AnasSarkiz/magnetic-shutter-remote/evidence/R7-components/jauch-850-pack.png

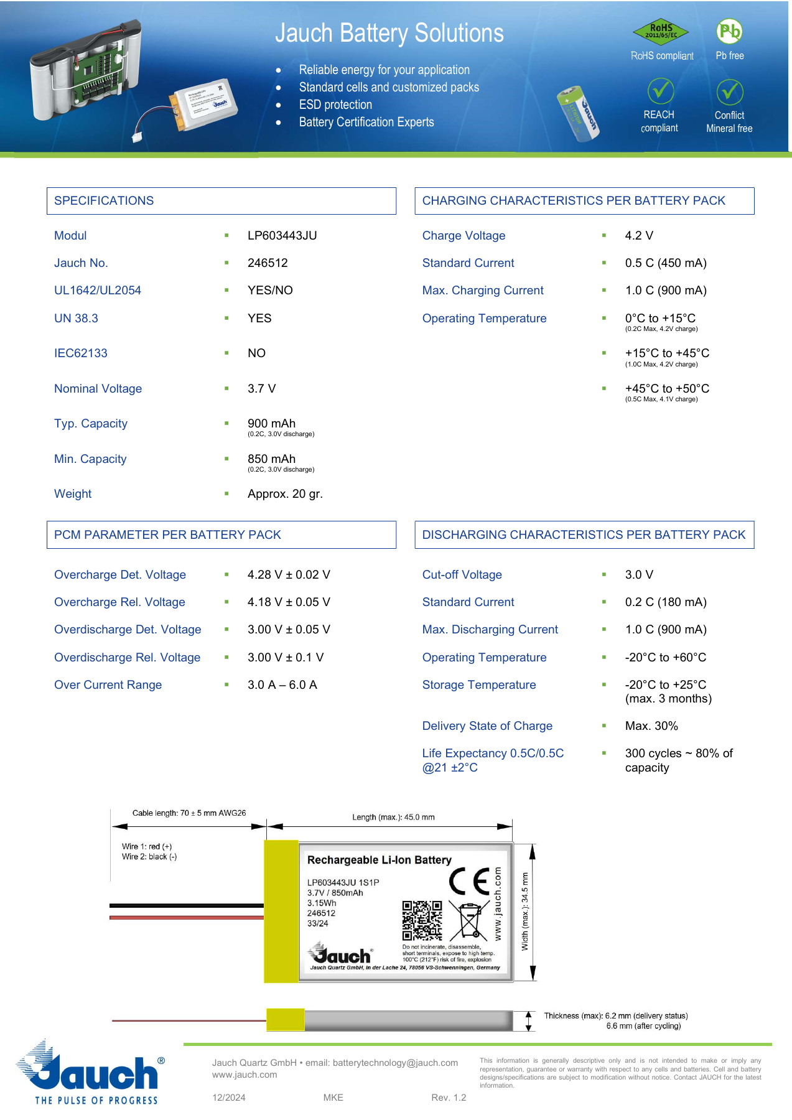
evidence/R7-components/jauch-850-pack.png
