AnasSarkiz/magnetic-shutter-remote/evidence/USB4215-import-audit/external-process-review/package/README.md

# GCT USB4215 / JLCPCB external qualification package

**ENGINEERING QUALIFICATION ONLY - NOT FOR FABRICATION**

Version **external-review-1**, 2026-10-03. Exact part **GCT USB4215-03-A / C37616412**. Candidate **BLOCKED**; remote board **R5 DFM REVIEW — NOT FOR FABRICATION**. No R6, PCB edit or manufacturing approval.

This is a component-only engineering review, not order-ready PCB data. It contains exact GCT drawing/specification, source identity, dimensioned copper/drill comparison, independent source/import/CAM paste views, four shell details, aperture table, import-fix summary, paste/process findings and separate unsent questions. No full R5 project, credentials, raw board CAM, BOM/CPL or unrelated repository content is included.

1. [Exact source register](SOURCE-REGISTER.md)
2. [Dimensioned copper/drill comparison](copper-drill-dimensioned-comparison.png)
3. [Aperture geometry](APERTURE-GEOMETRY.md)
4. [Paste qualification](PASTE-QUALIFICATION.md)
5. [Thermal/process context and shell table](SOLDER-PROCESS.md)
6. [Local tooling fix summary](IMPORTER-FIX-SUMMARY.md)
7. [GCT unresolved questions](GCT-REQUEST.md)
8. [JLCPCB exact process-coverage questions](JLCPCB-REQUEST.md)

The copper/drill comparison image/SVG is preserved **pre-fix evidence**. Its old caption "import drops 16 explicit TOP-paste regions" describes the original pipeline. The later importer fix closes that fidelity defect, as shown in the current source/import/CAM images and summary; the original dimensional evidence was not edited.

**SUPPLIER CAD INTENDS PASTE ON FOUR SHELL FEATURES**; that is not GCT process approval or JLCPCB assembly coverage. Published temperatures remain test conditions with production limits unconfirmed. Neither request has been sent; there are no external responses. No-response is not approval.

`MANIFEST.sha256` covers every other member. Verify with a SHA256-aware tool after extraction. Once sent, preserve this ZIP/hash exactly; clarification packages require a new version/name. Physical validation remains **POST-PROTOTYPE PHYSICAL VALIDATION**.
