AnasSarkiz/magnetic-shutter-remote/cloud/ENVIRONMENT-START.md

Use the existing isolated checkout /workspace/magnetic-shutter-remote; do not create a worktree. Preserve a later task-derived working branch, all changes, and local commits. Do not fetch/switch/reset an active task.
Before running anything, read AGENTS.md, cloud/SETUP.md, cloud/HANDOFF.md and cloud/STATUS.md. Require these files, cloud/R7-PORTABLE-MANIFEST.json and the R8 context; verify git merge-base --is-ancestor b25353c0a1d7adceeab9a966aaf68a6cb3594cc9 HEAD. If context is missing or HEAD is old main, stop and report; never run the old board.
No server is needed. From the checkout, use bash with set -euo pipefail. Export npm_config_cache="$PWD/.codex/runtime/npm-cache". Record git HEAD/status and actual host/cgroup memory/CPU/OOM limits under ignored .codex/logs with unique timestamps. Run bash cloud/setup.sh and bash cloud/smoke.sh, retaining separate logs with tee and pipefail. Report exit statuses, test counts, warnings and final tracked/untracked status; do not discard changes. The onboarding instance observed 32 GiB memory.max and a four-CPU quota, not a guaranteed plan allocation. Node25.6.0/Bun1.3.9 are task-local; Python>=3.11 required. Python3.14 is only for later optional CAM.
Setup/start smoke stays lightweight: do not route, run a root board build, broad DFM, viewer, 3D/CAM/SDK build as part of environment initialization. The source-edit/commit/push/PR/board-publication prohibitions apply to this onboarding run only, not permanently to later engineering tasks. Later user-authorized tasks may implement the ESP32 board and publish qualified prototype steps under AGENTS.md after the required gates pass. Frozen baselines remain immutable. Ordering, payment, assembler upload and supplier contact require separate authorization. Keep the ESP32 power-metadata warning and unresolved issues075/076 explicit; smoke is not qualification or fabrication validation.
Only later, after component qualification and placement gates pass and the task authorizes heavy work, invoke every heavy job through python3 cloud/run-heavy.py -- <command>, sequentially. This wrapper records resources/OOM and preserves failures; it does not waive gates.
Use provider-managed authentication; no user tokens/secrets. Keep environment private/only me and network restricted. Do not broaden repository access or share the environment. This onboarding task does not publish the environment or board; the user controls environment Publish.
