AnasSarkiz/magnetic-shutter-remote/cloud/TASK-PROMPT.md

Continue magnetic shutter remote R8 on this Cloud branch. Read AGENTS.md, cloud/HANDOFF.md, VALIDATION.md, issue075/076 and the repository-local tscircuit skill before changing anything. Run cloud/setup.sh and cloud/smoke.sh; report actual memory/runtime limits. Preserve baselines/ and main. Do not route on the Mac or run multiple heavy jobs. The ESP32-C3-WROOM-02-N4/C2934560 migration is unfinished: resolve the documented import/qualification gates through supported tooling, then complete power/boot/UART circuitry, mechanical fit, unrouted checks, routing and same-revision exports. One battery, one USB-C, no torch. Keep all fitted parts verified JLCPCB imports; no custom substitute footprints/generated-import or JSON patches. Use cloud/run-heavy.py for Linux heavy builds after placement passes. Do not call the existing Nordic JSON an ESP32 build, waive warnings, change manufacturer thresholds, order, pay or contact suppliers. Preserve exact prior results and known failures. Update issue reports and validation with real evidence, then publish only qualified prototype steps with matching build circuit.json. Physical tests remain POST-PROTOTYPE PHYSICAL VALIDATION.
