AnasSarkiz/magnetic-shutter-remote/evidence/USB4215-import-audit/UNSENT-QUALIFICATION-QUESTIONS.md

# USB4215 qualification questions — prepared only, NOT SENT

These are not substituted for authoritative answers. No files were sent or uploaded.

## GCT manufacturer

For USB4215-03-A, drawing/specification A, 26 April 2024, please identify the intended soldering method for each of the four through-hole shell stakes (PIP reflow, wave/selective, manual secondary, or another method). For a 1.0 mm PCB, please provide approved copper/mask/paste treatment, stencil thickness and shell paste volume/overprint guidance. The C37616412 supplier model uses twelve separate rectangular contact apertures and four segmented capsule shell apertures (~1.0 ×1.8 mm rear; ~1.0 ×2.2 mm front). Are these approved? Please provide allowable reflow-cycle count and confirm the section 7.0 time/temperature limits. If post-reflow manual shell soldering is allowed, specify maximum iron temperature, contact time, repeated operations and housing restrictions. Please identify the applicable document/revision.

Supporting drawings: preserved GCT drawing/spec, [source metrology](../USB-replacement-search-2026-10-03/continued-search/USB4215-source-metrology.png), [actual TOP paste CAM](final/cam-paste.png), [aperture dimensions](final/aperture-metrology.json). Supplier model/package UUID: 3104977db58742e399663286e4a66eac, title USB-C-SMD_GT-USB-7010B. The unrelated model title is disclosed, not treated as GCT authorization.

## JLCPCB assembler

For exact part C37616412 / GCT USB4215-03-A, does your PCBA process solder all four plated shell slots, and by what method? Is it included in Economic/Standard SMT assembly, or must a THT/PIP/selective/manual or special service be requested? What stencil thickness, shell paste/overprint, mask openings, inspection and order options do you require for a 1.0 mm PCB? Please confirm coverage of the four shell anchors explicitly; “SMT Assembly” alone does not answer this. Can you use the GCT land drawing with the separately preserved supplier paste geometry, and what changes or manufacturer approval are required? Confirm any X-ray or special inspection requirement for this exact connector.

Manufacturer process limits must come from GCT; assembler process coverage must come from JLCPCB. No party is asked to certify the other's responsibility.
