AnasSarkiz/magnetic-shutter-remote/evidence/USB4215-import-audit/external-process-review/GCT-REQUEST.md

# GCT technical request — finalized, NOT SENT

**ENGINEERING QUALIFICATION ONLY — NOT FOR FABRICATION**

Subject: USB4215-03-A stencil and shell-anchor soldering qualification

Please provide exact-part engineering guidance for GCT **USB4215-03-A**, drawing/specification Rev A, 2024-04-26. We are evaluating the C37616412 supplier package, UUID `3104977db58742e399663286e4a66eac`, for a 1.0 mm PCB. Its copper and plated-slot geometry have been compared with your drawing. The supplied CAD contains **12 contact paste apertures and four shell paste apertures**; the attached images/table preserve those contours. This is supplier CAD, not a GCT-approved stencil claim. Its library title is USB-C-SMD_GT-USB-7010B and its metadata links another part, so we need your independent approval.

**A. Stencil / paste**

1. Are the four supplied shell paste apertures intended to solder the four shell anchors during SMT reflow?
2. Is this exact supplier paste/stencil pattern approved or recommended by GCT for USB4215-03-A?
3. If not, please provide the recommended stencil thickness, contact aperture dimensions, shell aperture dimensions, and paste reduction/expansion or overprint rules for this PCB thickness. Please identify any required solder-mask treatment.

**B. Production reflow**

Section 7.0 publishes peak 255–260 °C, 60 s above 217 °C, 50 s above 230 °C and 5 s above 250 °C. Are these approved production-process limits, or heat-resistance/qualification-test conditions only? Please specify the recommended/maximum production peak temperature, maximum peak duration, time above liquidus, allowed reflow-cycle count, and ramp/preheat constraints.

**C. Shell completion**

Are **all four shell anchors on USB4215-03-A intended to be completely soldered in the same SMT reflow operation using these four apertures**? If yes, is any secondary soldering required? If no, please identify the required manual/selective/wave or other process. For any permitted manual step after reflow, provide maximum iron temperature, maximum contact time, permitted repeat/heating-cycle limits and applicable housing restrictions.

Please identify the applicable drawing/process document and revision. Responses must apply specifically to USB4215-03-A. We are not asking GCT to certify JLCPCB's assembly coverage.

Suggested attachment: `GCT-USB4215-JLCPCB-QUALIFICATION.zip`. Nothing has been sent or uploaded.
