AnasSarkiz/magnetic-shutter-remote/evidence/USB4215-import-audit/external-process-review/JLCPCB-REQUEST.md

# JLCPCB technical request — finalized, NOT SENT

**ENGINEERING QUALIFICATION ONLY — NOT FOR FABRICATION**

Subject: C37616412 exact shell-anchor coverage and stencil confirmation

Please confirm the PCBA process for **C37616412 / GCT USB4215-03-A**, supplier package UUID `3104977db58742e399663286e4a66eac`, on a 1.0 mm PCB. Your exact-part listing records Extended SMT Assembly, Economic and Standard. Our recorded 2026-10-03 check showed 145 stock / 63 available to order; availability is separate from process qualification. Attached geometry shows 12 contact paste apertures and four paste apertures over plated shell-anchor slots.

1. Does Extended SMT assembly for this exact part solder all 12 contact paste features **and all four shell-anchor paste features**?
2. Are all four shell anchors completed during normal SMT reflow using the supplied paste apertures?
3. Is any THT, selective, wave, manual or special process required after SMT? If so, identify the exact process and its operating profile/limits so it can be checked against GCT's permitted process.
4. Is this exact supplier stencil/paste geometry accepted by your standard stencil process? State the stencil thickness, any contact/shell aperture modifications or required overprint, and any mask treatment needed.
5. If the four shell anchors are not automatically included, what service/order option must be selected?
6. Are any exact-connector PCBA order notes, engineering confirmations, special inspection or other assembly requirements needed?

Please answer for C37616412 specifically. A generic statement that Extended parts are SMT compatible does not establish shell-anchor coverage. GCT manufacturer thermal/process approval is being requested separately; we are not asking JLCPCB to substitute for that approval.

Suggested attachment: `GCT-USB4215-JLCPCB-QUALIFICATION.zip`. Nothing has been sent or uploaded.
