AnasSarkiz/magnetic-shutter-remote/evidence/USB4215-import-audit/external-process-review/package/SOURCE-REGISTER.md

# Exact source register

**ENGINEERING QUALIFICATION ONLY - NOT FOR FABRICATION**

GCT / Global Connector Technology **USB4215-03-A / C37616412**. Drawing/specification **Rev A, 2024-04-26**. Component UUID `907b9bea7a60481d8a3d3aef3cba8ef1`; package UUID `3104977db58742e399663286e4a66eac`.

Supplier library title `USB-C-SMD_GT-USB-7010B`; its metadata links another part, C2837092. Neither that title/link nor successful import is GCT authority. Copper/drills were independently compared against the included GCT drawing. The paste shapes are supplier geometry requiring separate manufacturer approval.

[Machine-readable source register](SOURCE-REGISTER.json) records exact original raw CAD, regenerated import, Circuit JSON and final paste hashes, together with manufacturer/supplier URLs. Those full CAD/CAM files are preserved locally and intentionally excluded from this compact external review.

The 2026-10-03 stock observation is **145 stock / 63 available to order / Extended / SMT Assembly / Economic and Standard / MSL1**. This is a dated observation, not a sourceability guarantee or shell-process approval. No special X-ray requirement was displayed; that is not a waiver. No response, contact or upload occurred.

Official sources: [GCT exact product](https://gct.co/connector/usb4215), [GCT drawing](https://gct.co/files/drawings/usb4215.pdf), [GCT specification](https://gct.co/files/specs/usb4215-spec.pdf), [JLCPCB exact part](https://jlcpcb.com/partdetail/39339856-USB4215_03A/C37616412).
