AnasSarkiz/magnetic-shutter-remote/tooling/r7-paste-review-requirements.txt

aiofiles==25.1.0
blinker==1.9.0
cairocffi==0.9.0
cffi==2.1.1
charset-normalizer==3.5.2
click==8.5.0
Flask==3.1.3
gerbonara==1.5.0
h11==0.16.0
h2==4.4.1
hpack==4.2.0
Hypercorn==0.18.0
hyperframe==6.1.0
itsdangerous==2.2.0
Jinja2==3.1.6
MarkupSafe==3.0.3
numpy==2.5.3
pcb-tools==0.1.6
pillow==12.3.0
priority==2.0.0
pycparser==3.0
Quart==0.23.1
reportlab==4.4.3
rtree==1.4.1
scipy==1.18.1
shapely==2.1.2
svgpathtools==1.7.2
svgwrite==1.4.3
Werkzeug==3.1.9
wsproto==1.3.2
