AnasSarkiz/magnetic-shutter-remote/baselines/r7/mechanical/drawing-r2-1.png

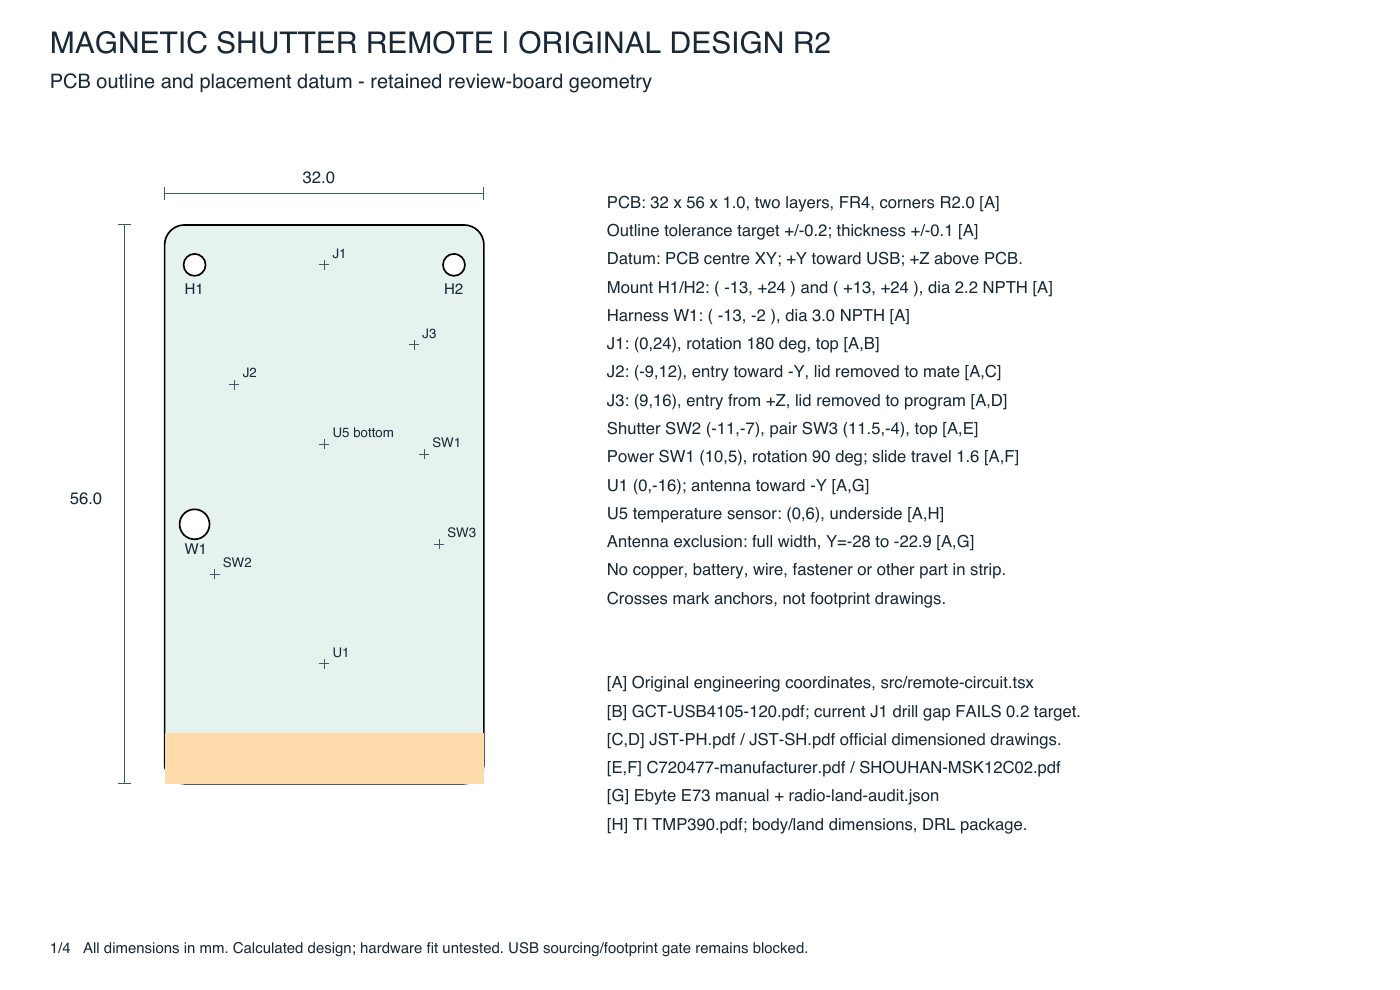
baselines/r7/mechanical/drawing-r2-1.png
