AnasSarkiz/magnetic-shutter-remote/baselines/r7/mechanical/drawing-r2-4.png

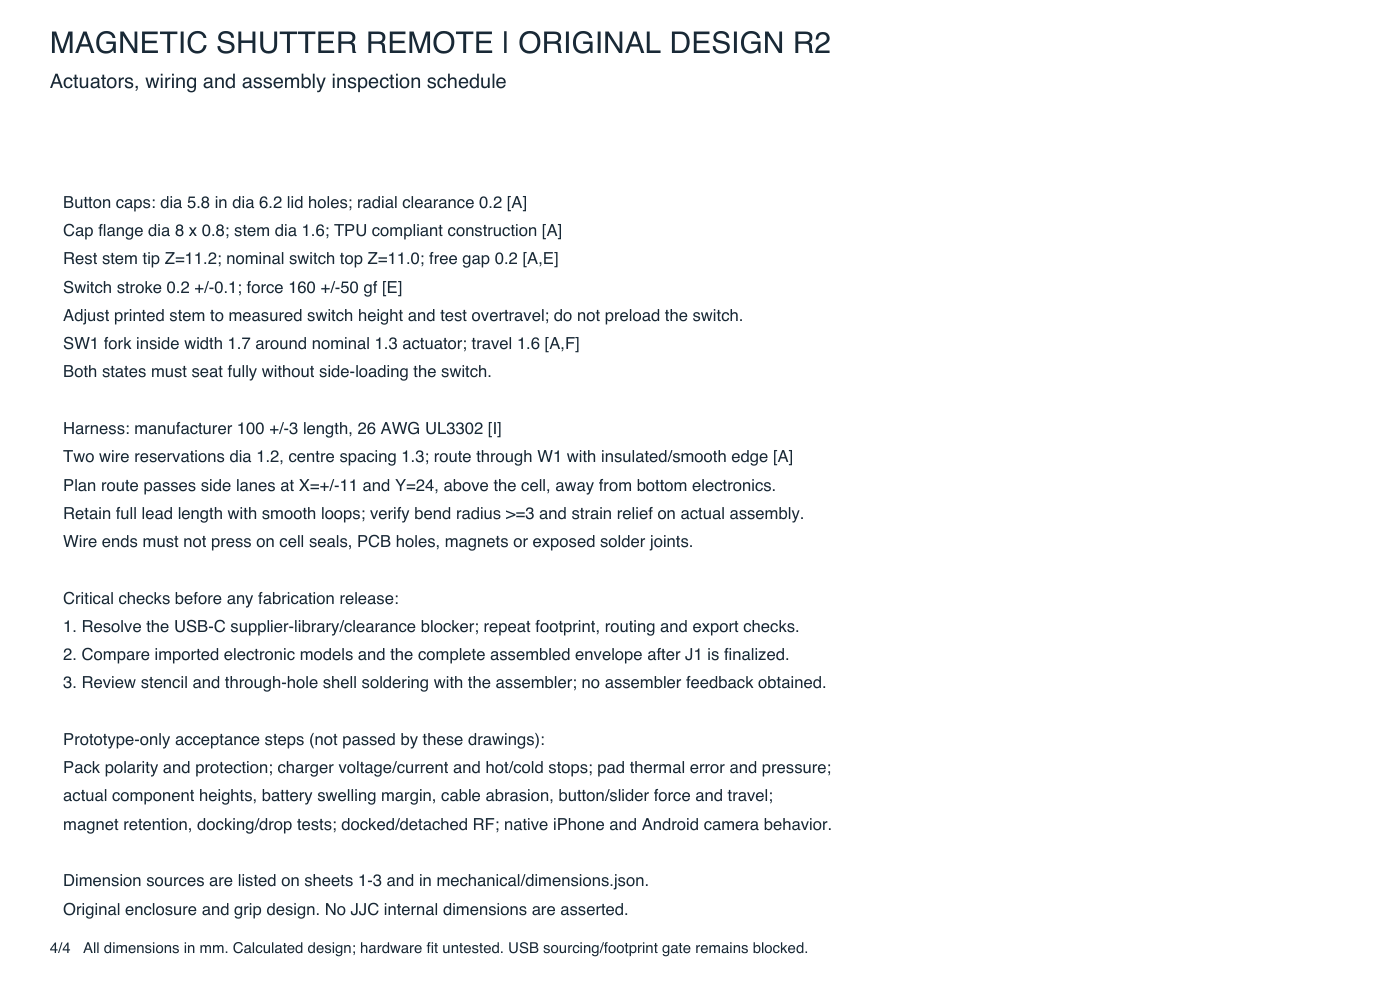
baselines/r7/mechanical/drawing-r2-4.png
