AnasSarkiz/magnetic-shutter-remote/baselines/r7/mechanical/drawing-r3-2.png

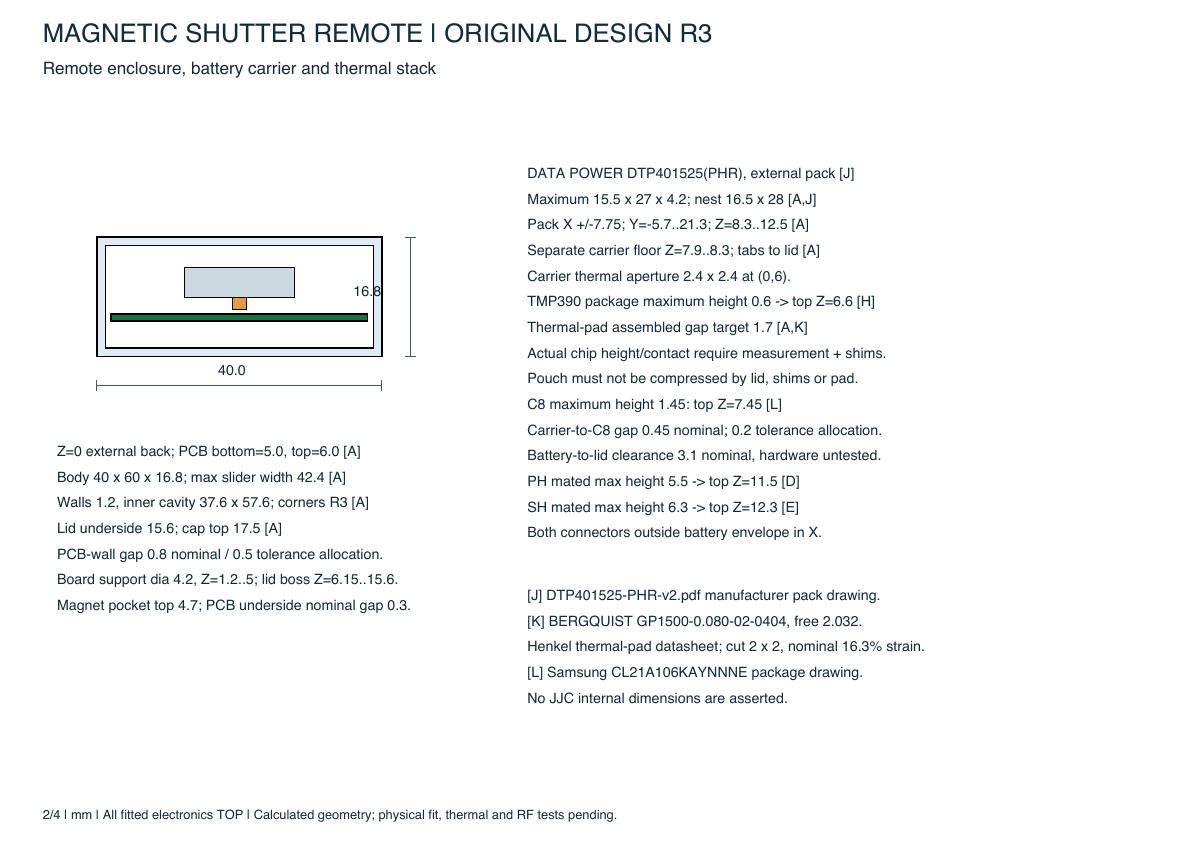
baselines/r7/mechanical/drawing-r3-2.png
