AnasSarkiz/magnetic-shutter-remote/baselines/r7/mechanical/drawing-r3-4.png

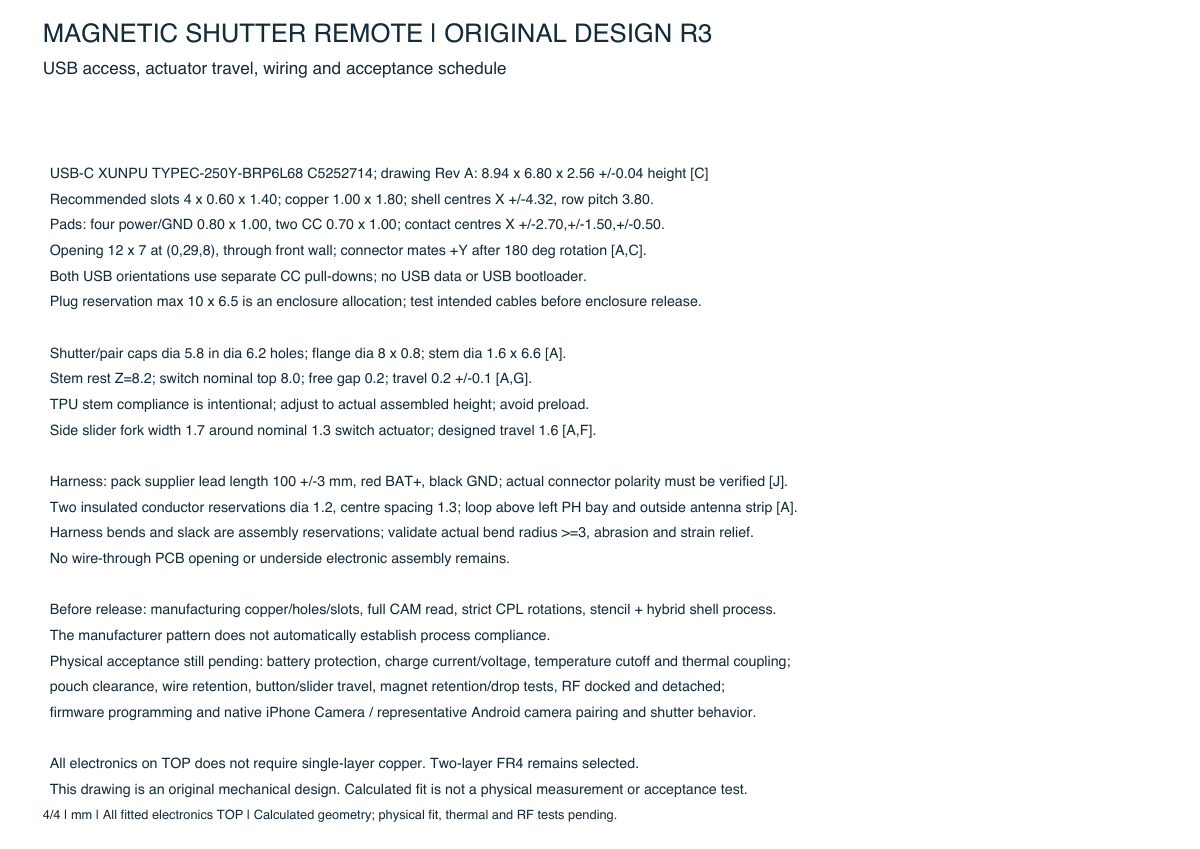
baselines/r7/mechanical/drawing-r3-4.png
