AnasSarkiz/magnetic-shutter-remote/baselines/r7/mechanical/remote-cutaway-r3.png

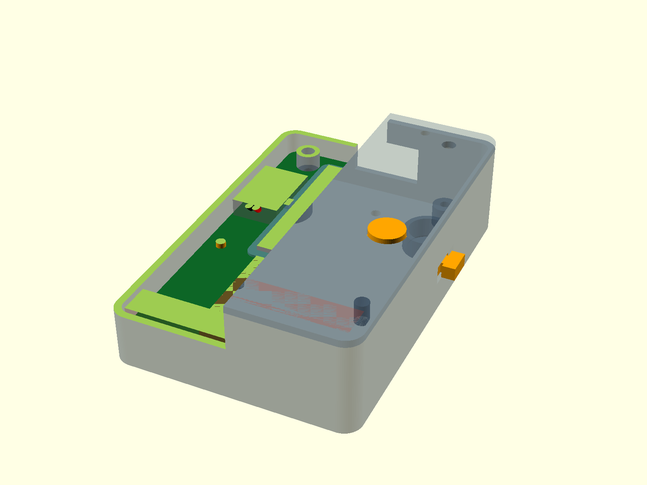
baselines/r7/mechanical/remote-cutaway-r3.png
