AnasSarkiz/magnetic-shutter-remote/evidence/R7-components/pt4115-official-pinout.png

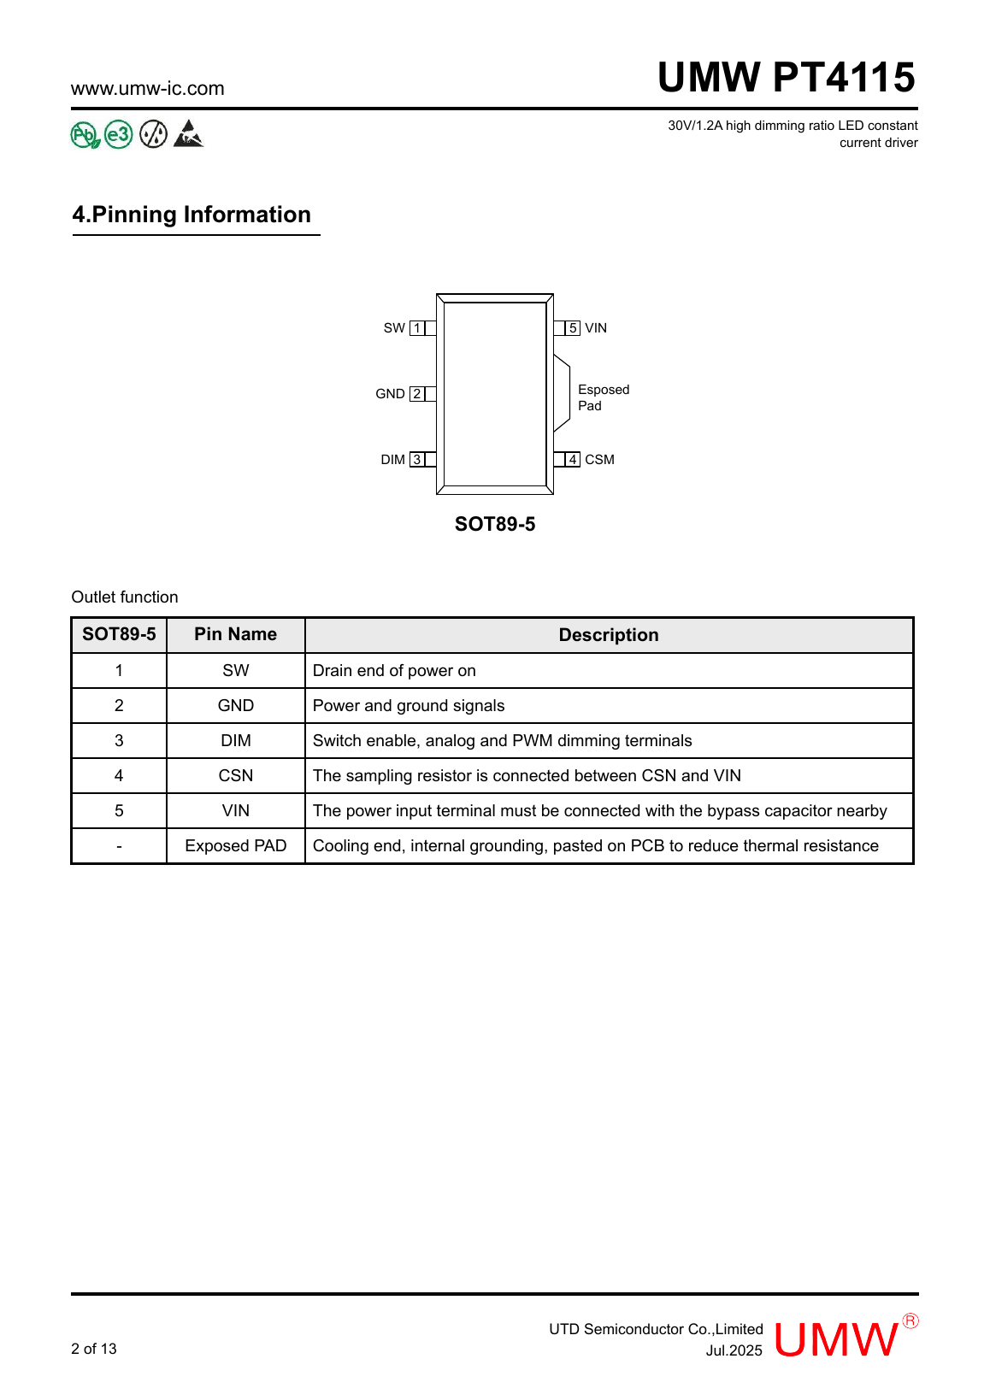
evidence/R7-components/pt4115-official-pinout.png
