AnasSarkiz/magnetic-shutter-remote/evidence/R7-components/pt4115-pinout.png

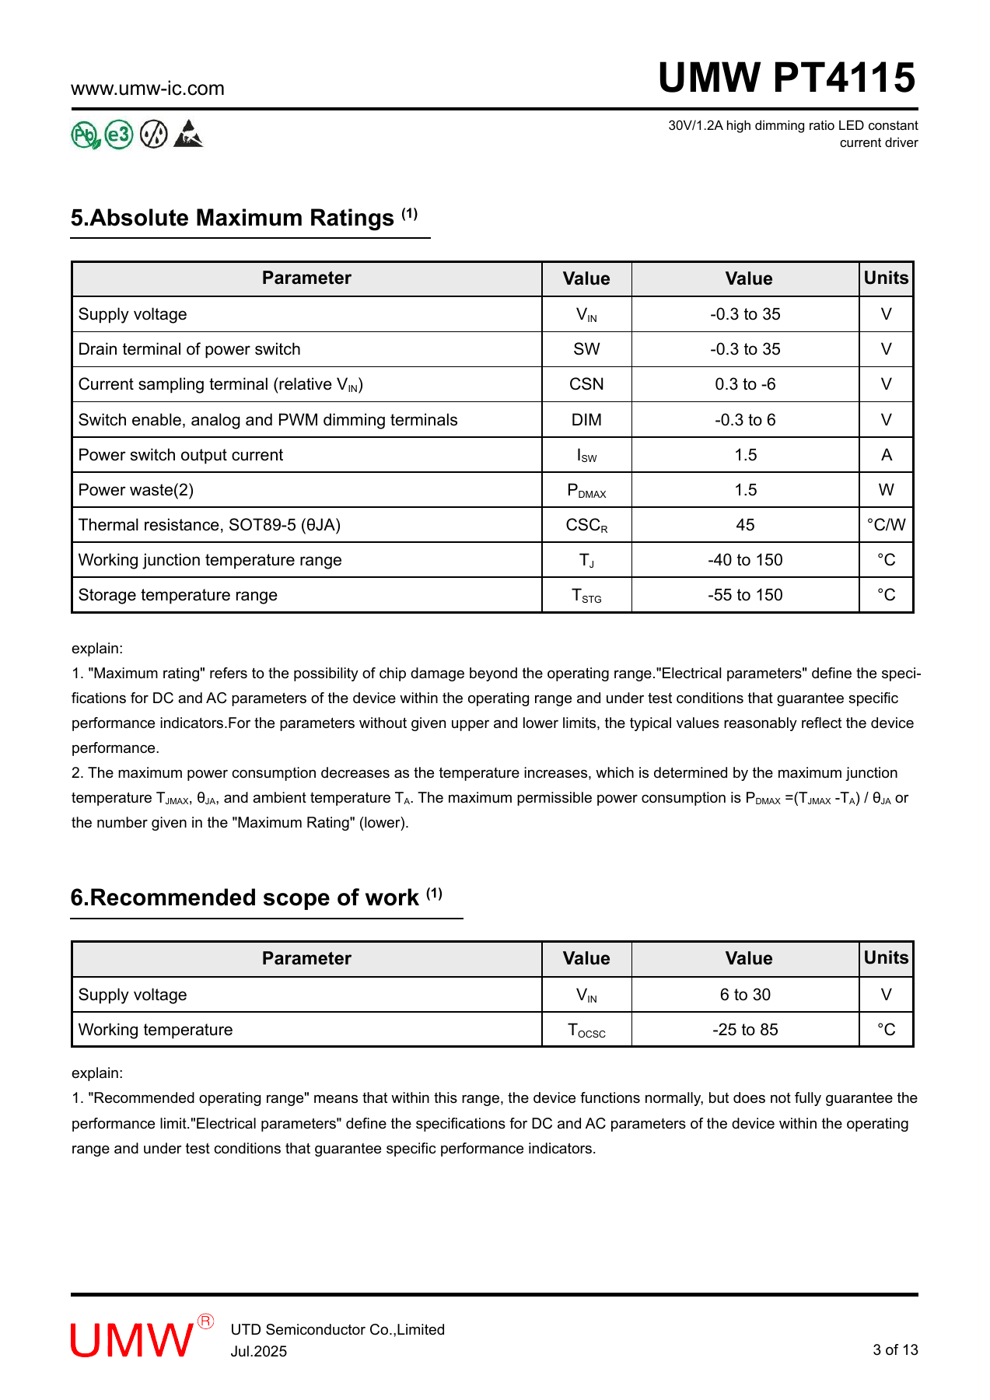
evidence/R7-components/pt4115-pinout.png
