AnasSarkiz/magnetic-shutter-remote/evidence/R7-power/DTP603443-pack-drawing.png

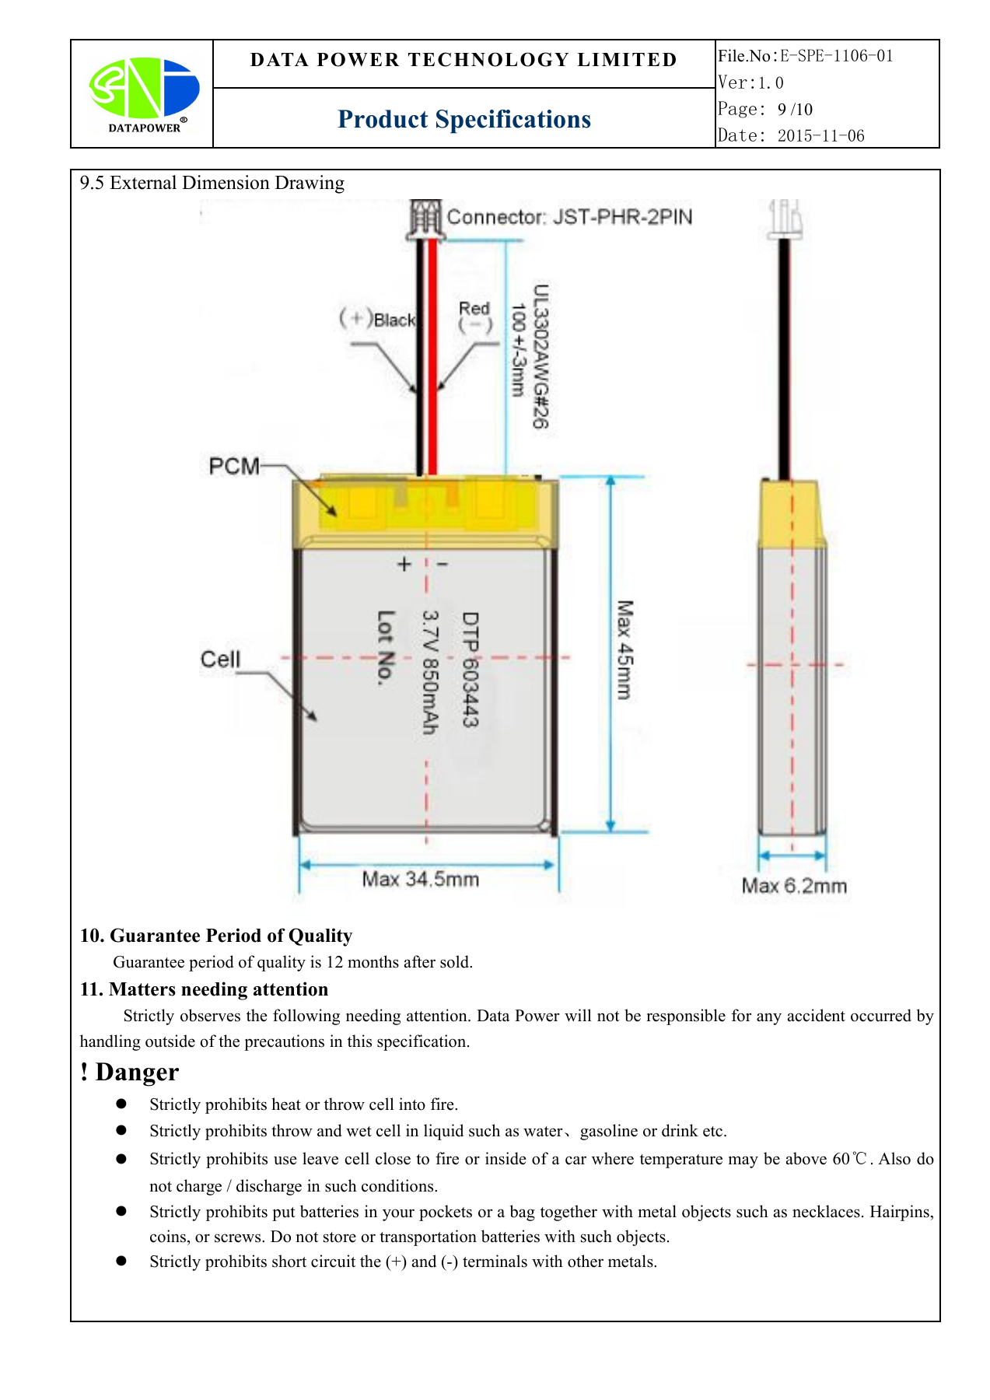
evidence/R7-power/DTP603443-pack-drawing.png
