AnasSarkiz/magnetic-shutter-remote/evidence/R7-power/PKCELL-pack-drawing.png

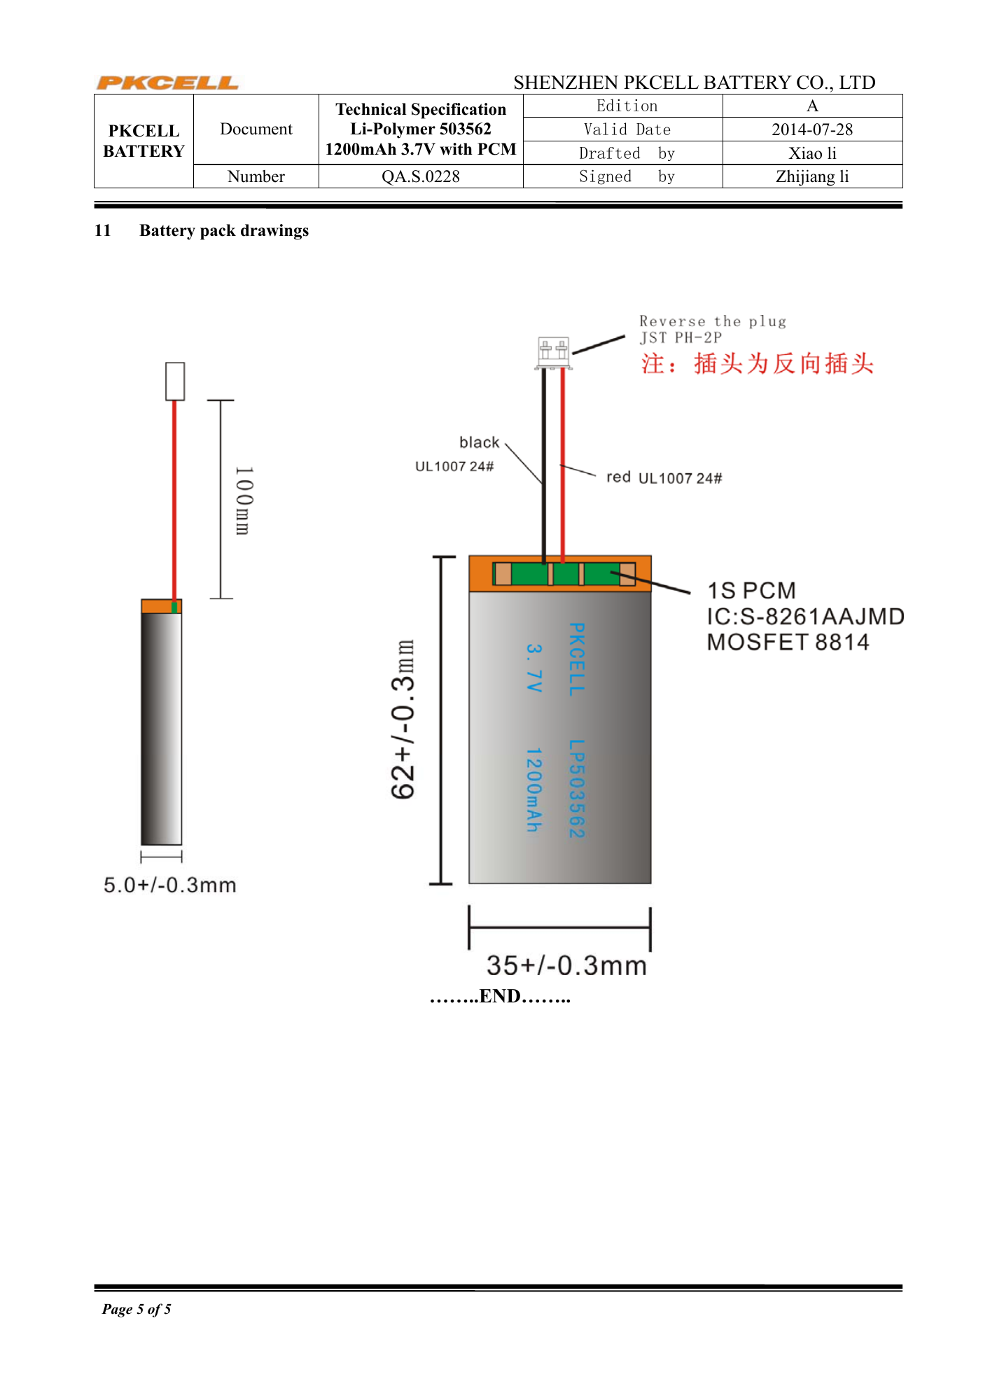
evidence/R7-power/PKCELL-pack-drawing.png
