AnasSarkiz/magnetic-shutter-remote/evidence/R7-power/TI-current-limit-equation.png

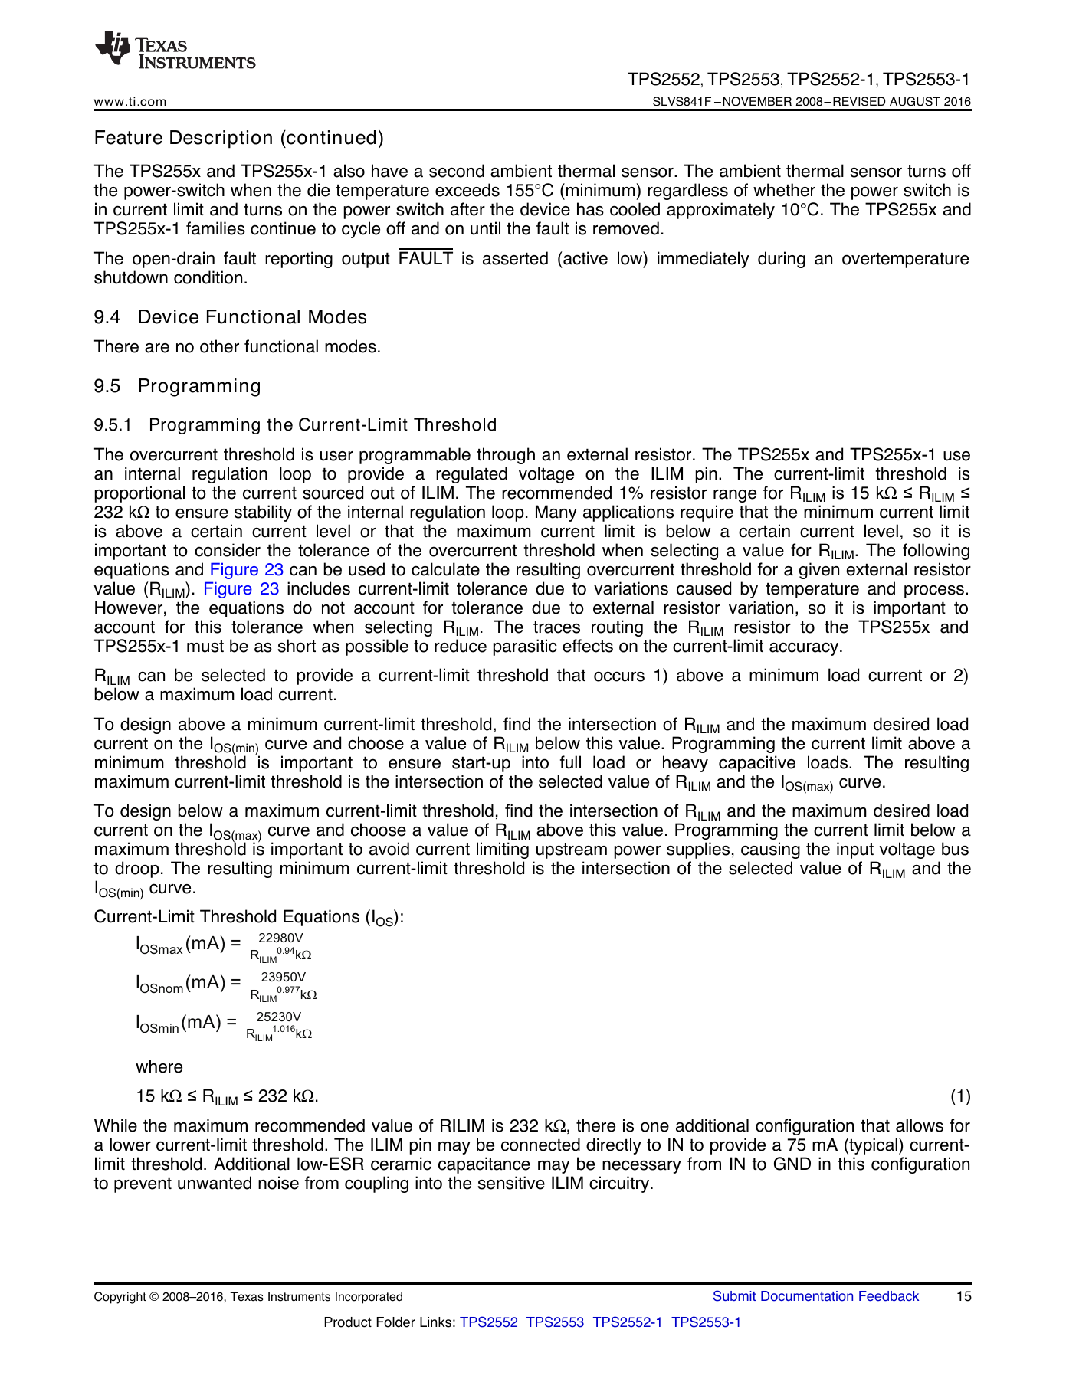
evidence/R7-power/TI-current-limit-equation.png
