AnasSarkiz/magnetic-shutter-remote/references/R5/C456012.png

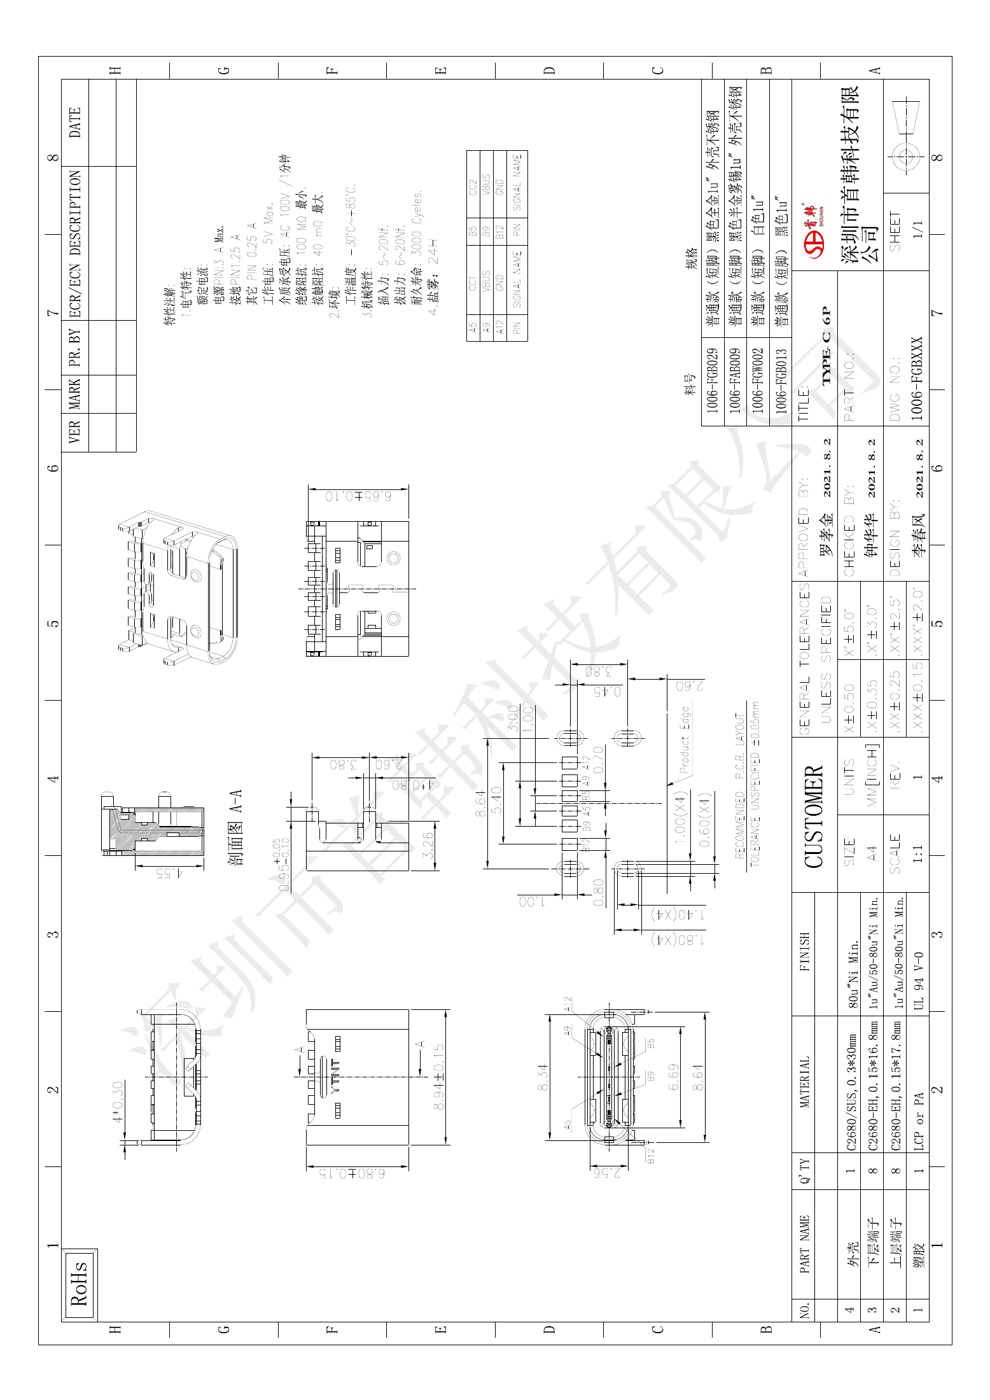
references/R5/C456012.png
