AnasSarkiz/magnetic-shutter-remote/references/R5/C668623.png

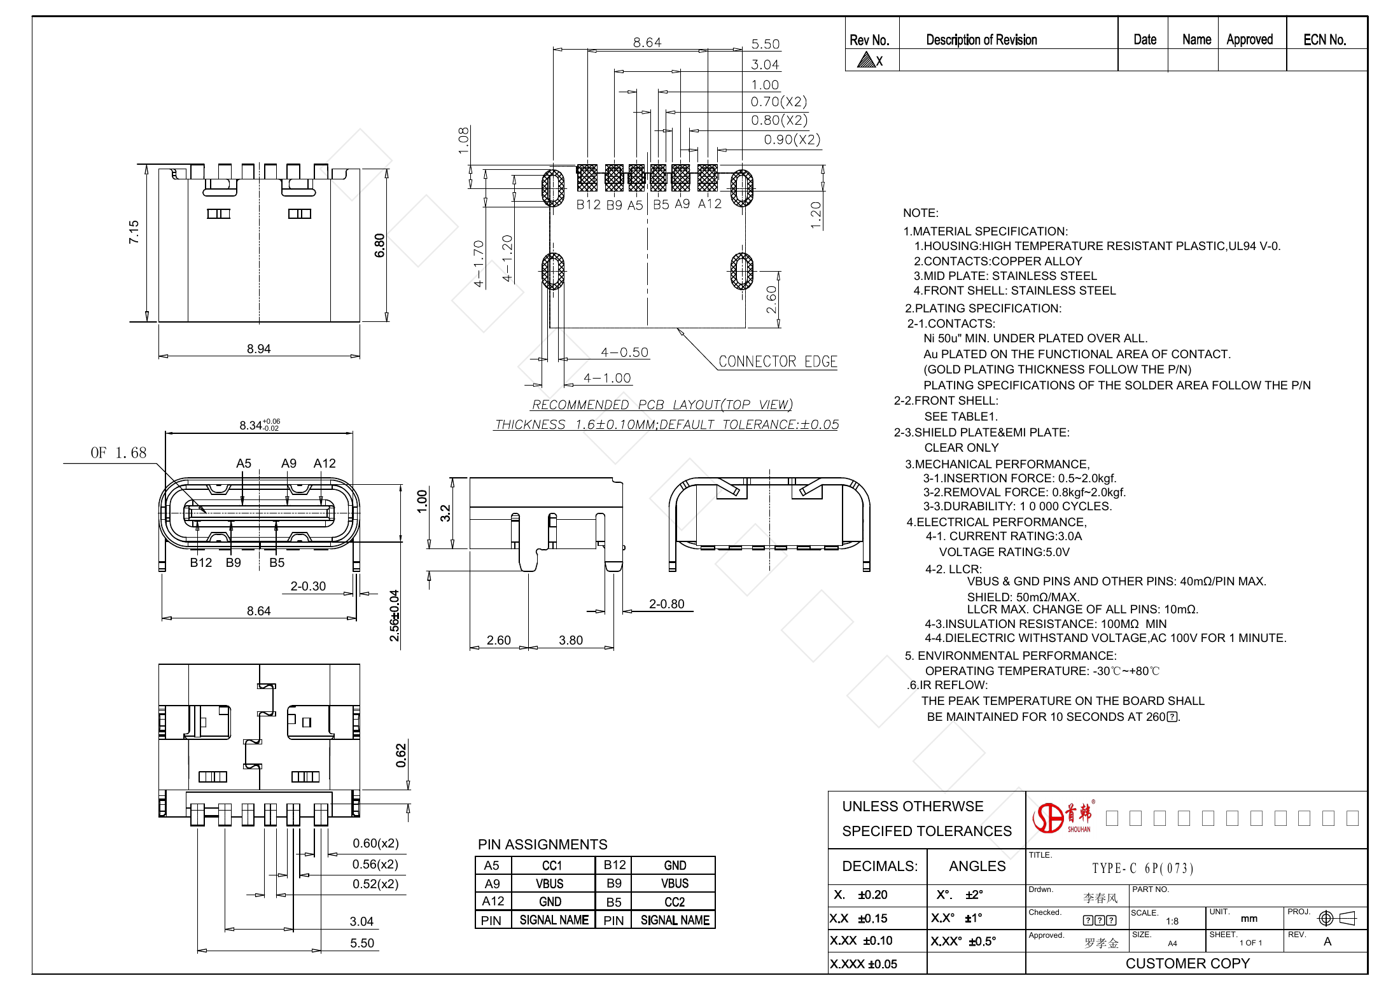
references/R5/C668623.png
