AnasSarkiz/magnetic-shutter-remote/references/R5/GCT-USB4125-current.png

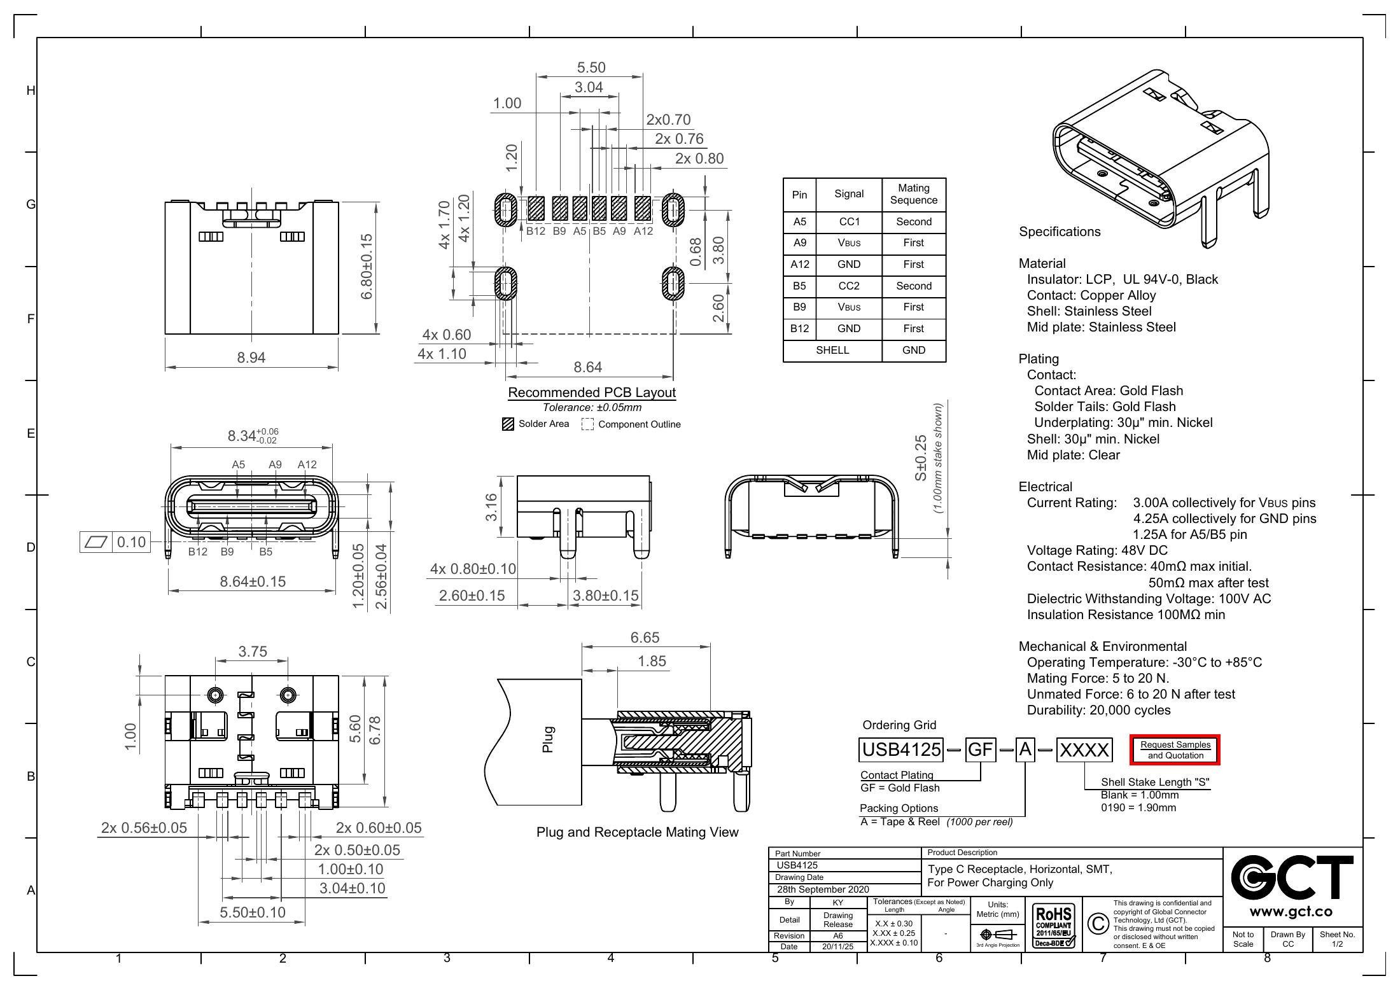
references/R5/GCT-USB4125-current.png
