AnasSarkiz/magnetic-shutter-remote/tscircuit-issues/evidence/023-fanout-treats-schematic-sheet-as-routing-group/repro-fanout-in-schematic-sheet.png

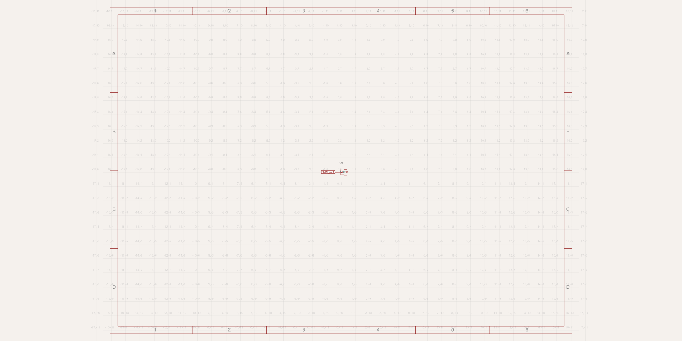
tscircuit-issues/evidence/023-fanout-treats-schematic-sheet-as-routing-group/repro-fanout-in-schematic-sheet.png
