AnasSarkiz/magnetic-shutter-remote/BOM.md

# R6 verified electronic BOM

37 fitted references; TOP only; J1 GCT USB4215-03-A. Engineering prototype — not production qualified. Shell inspection/manual rework may be required.

J1 availability rechecked 2026-10-03: 125 stock, 43 orderable. Other sourcing dates remain explicit in CSV. No reservations. U1 requires Standard assembly and X-ray. Battery and mechanical parts are separately installed.

| References | Qty | Exact MPN | Package | C-number | Category | Available | Checked |
|---|---:|---|---|---|---|---:|---|
| U1 | 1 | E73-2G4M08S1C | SMD module, 43 pads, 13 x 18 x 3 mm | [C356849](https://jlcpcb.com/partdetail/Chengdu_Ebyte_ElecTech-E732G4M08S1C/C356849) | Extended | 1246 | 2026-10-01 |
| U2 | 1 | BQ25185DLHR | WSON-10, 2.2 x 2 mm, exposed pad | [C19725033](https://jlcpcb.com/partdetail/BQ25185DLHR/C19725033) | Extended | 3739 | 2026-10-01 |
| U5 | 1 | TMP390A2DRLR | SOT-563 / DRL-6 | [C5219772](https://jlcpcb.com/partdetail/TMP390A2DRLR/C5219772) | Extended | 37585 | 2026-10-01 |
| U4 | 1 | TPS3839G33DBZR | SOT-23-3 / DBZ | [C485802](https://jlcpcb.com/partdetail/TPS3839G33DBZR/C485802) | Extended | 3375 | 2026-10-01 |
| R3 | 1 | 0603WAF1502T5E | 0603 | [C22809](https://jlcpcb.com/partdetail/0603WAF1502T5E/C22809) | Basic | 4275297 | 2026-10-01 |
| R8 | 1 | 0603WAF1303T5E | 0603 | [C22795](https://jlcpcb.com/partdetail/0603WAF1303T5E/C22795) | Extended | 546495 | 2026-10-01 |
| R9 | 1 | 0603WAF1002T5E | 0603 | [C25804](https://jlcpcb.com/partdetail/0603WAF1002T5E/C25804) | Basic | 16156915 | 2026-10-01 |
| R10 | 1 | 0603WAF1621T5E | 0603 | [C22844](https://jlcpcb.com/partdetail/0603WAF1621T5E/C22844) | Extended | 27604 | 2026-10-01 |
| R11 | 1 | 0603WAF1872T5E | 0603 | [C22893](https://jlcpcb.com/partdetail/0603WAF1872T5E/C22893) | Extended | 131350 | 2026-10-01 |
| C8 | 1 | CL21A106KAYNNNE | 0805 | [C15850](https://jlcpcb.com/partdetail/CL21A106KAYNNNE/C15850) | Basic | 3794120 | 2026-10-01 |
| C9 | 1 | TCC0603COG470J500CT | 0603 | [C282505](https://jlcpcb.com/partdetail/TCC0603COG470J500CT/C282505) | Extended | 8111 | 2026-10-01 |
| U3 | 1 | TPS7A0230PDBVR | SOT-23-5 (DBV) | [C3747031](https://jlcpcb.com/partdetail/TexasInstruments-TPS7A0230PDBVR/C3747031) | Extended | 37516 | 2026-10-01 |
| J1 | 1 | USB4215-03-A | SMT 16-contact USB-C; four plated shell slots | [C37616412](https://jlcpcb.com/partdetail/39339856-USB4215_03A/C37616412) | Extended | 43 | 2026-10-03 |
| J2 | 1 | S2B-PH-SM4-TB(LF)(SN) | PH 2 mm, side-entry SMT | [C295747](https://jlcpcb.com/partdetail/JST-S2B_PH_SM4_TB_LF_SN/C295747) | Extended | 20398 | 2026-10-01 |
| J3 | 1 | BM06B-SRSS-TB(LF)(SN) | SH 1 mm, top-entry SMT | [C160392](https://jlcpcb.com/partdetail/JST-BM06B_SRSS_TB_LF_SN/C160392) | Extended | 28818 | 2026-10-01 |
| SW1 | 1 | MSK12C02 | SMD 8 x 2.8 mm, 3 contacts + shell | [C431540](https://jlcpcb.com/partdetail/MSK12C02/C431540) | Extended | 188023 | 2026-10-01 |
| SW2, SW3 | 2 | TS-1088-AR02016 | SMD tactile 4 x 3 x 2 mm | [C720477](https://jlcpcb.com/partdetail/SHOUHAN-TS_1088_AR02016/C720477) | Basic | 742195 | 2026-10-01 |
| Q1, Q2 | 2 | 2N7002 | SOT-23 | [C8545](https://jlcpcb.com/partdetail/JiangsuChangjingElectronicsTechnologyCoLtd-2N7002/C8545) | Basic | 1522993 | 2026-10-01 |
| R1, R2 | 2 | 0603WAF5101T5E | 0603 imperial / 1608 metric | [C23186](https://jlcpcb.com/partdetail/UNIROYAL-0603WAF5101T5E/C23186) | Basic | 24338678 | 2026-10-01 |
| R4, R7 | 2 | 0603WAF1001T5E | 0603 imperial / 1608 metric | [C21190](https://jlcpcb.com/partdetail/UNIROYAL-0603WAF1001T5E/C21190) | Basic | 16868949 | 2026-10-01 |
| R5, R6, R12, R13 | 4 | 0603WAF1003T5E | 0603 imperial / 1608 metric | [C25803](https://jlcpcb.com/partdetail/UNIROYAL-0603WAF1003T5E/C25803) | Basic | 20485261 | 2026-10-01 |
| C1, C2, C3, C4 | 4 | CL10A475KO8NNNC | 0603 imperial / 1608 metric | [C19666](https://jlcpcb.com/partdetail/Samsung-CL10A475KO8NNNC/C19666) | Basic | 2016787 | 2026-10-01 |
| C5, C6, C7 | 3 | CC0603KRX7R9BB104 | 0603 imperial / 1608 metric | [C14663](https://jlcpcb.com/partdetail/YAGEO-CC0603KRX7R9BB104/C14663) | Basic | 41987508 | 2026-10-01 |
| LED1, LED2 | 2 | KT-0603R | 0603 imperial / 1608 metric | [C2286](https://jlcpcb.com/partdetail/HubeiKENTOElec-KT_0603R/C2286) | Basic | 4349467 | 2026-10-01 |
