AnasSarkiz/magnetic-shutter-remote/evidence/R7-power/PURCHASED-RING-SHORTLIST.md

# Inexpensive purchased ring options — checked 2026-10-04

User requested inexpensive DigiKey or Mouser options. These are assembled external rings, not JLCPCB board BOM entries. Prices shown in USD for quantity one, excluding shipping/tax. Listed stock is not reserved and may change. No order, automatic selection or R7 PCB modification.

| Exact product | Purchase sources and listed price | Dimensions / control | Requirement gaps |
|---|---|---|---|
| Adafruit 5138, DigiKey 1528-5138-ND / Mouser 485-5138 | [DigiKey](https://www.digikey.com/en/products/detail/adafruit-industries-llc/5138/15293458), [Mouser](https://www.mouser.com/en/ProductDetail/Adafruit/5138?qs=TCDPyi3sCW3uGD3Iop6Jrw%3D%3D): $8.50; respective pages list 90 / 20 available | 70 mm OD; 5 mm PCB width; 5 V power-only; power PWM controls entire ring | Fixed cool white; no verified CRI ≥90. Manufacturer technical table states 1 A at 5 V (5 W input), while description references 500 mA supply capability. Do not resolve that inconsistency by guessing. Manufacturer explicitly requires heat mitigation for operation longer than a minute. Not accepted at full power for current compact 1.5–2 W target. |
| Adafruit 2855, DigiKey 1528-1607-ND / Mouser 485-2855 | [DigiKey](https://www.digikey.com/en/products/detail/adafruit-industries-llc/2855/5878297), [Mouser](https://www.mouser.com/en/ProductDetail/Adafruit/2855?qs=E8JTJTJKghaSu1Gt5cN4OQ%3D%3D): $11.95; respective pages list 269 / 13 available | 16 RGBW LEDs; 44.5 mm OD, 31.75 mm ID, 3.25 mm stated thickness; neutral-white approximately 4500 K plus RGB; serial control | No verified CRI ≥90 or photography-quality tunable-white endpoints. Requires power, ground and data, with proper logic interface. Power budget and camera PWM/banding not qualified. Candidate for low-cost interface/fit experiments, not final photography acceptance. |
| Adafruit 2862, DigiKey 1528-2333-ND | [DigiKey](https://www.digikey.com/en/products/detail/adafruit-industries-llc/2862/5878439): $19.95; search result lists 33 available | 24 RGBW LEDs; 65.5 mm OD; neutral-white approximately 4500 K plus RGB; 5 V, 800 kHz serial input | Same unverified CRI/CCT limitations as 2855. Larger format; current limit must prevent full simultaneous RGBW drive exceeding battery budget. Not final-qualified. |

## Manufacturer evidence

- [Adafruit 5138](https://www.adafruit.com/product/5138): power/current table, fixed white, PWM and heat warning. Power-only integration is possible in principle but exact reduced-power performance is not documented here.
- [Adafruit 2855](https://www.adafruit.com/product/2855): assembled/tested RGBW ring, dimensions, serial brightness control.
- [Adafruit 2862](https://www.adafruit.com/product/2862) and [manufacturer product document](https://mm.digikey.com/Volume0/opasdata/d220001/medias/docus/2379/2862_Web.pdf): 5 V / serial protocol; approximately 400 Hz PWM stated in historical document. Product revisions must be identified before binding firmware. This may produce camera banding; physical phone exposure tests remain pending, not presumed failures or passes.
- [Manufacturer ring guide](https://learn.adafruit.com/adafruit-neopixel-uberguide/advanced-coding?view=all): RGBW white variants have fixed approximately 3000/4500/6000 K white emitters. Adding RGB to a fixed-white ring does not establish CRI ≥90 or qualified 2500/5500/9000 K output.

No option above has been shown to meet all previously accepted photography requirements. Do not silently relax those requirements. The 2855 is the most compact inexpensive digital-control experiment among these, not a claimed final solution. The 5138 is the cheapest power-only connection but has explicit power/heat and color limitations. Exact supply, connector and battery sizing remain unselected.

## Cheaper-options follow-up — 2026-10-04

- **DFRobot DFR0888-12**, DigiKey **1738-DFR0888-12-ND**, Mouser **426-DFR0888-12**: listed **$6.90** at [DigiKey](https://www.digikey.com/en/products/detail/dfrobot/DFR0888-12/16678681) and [Mouser](https://www.mouser.com/ProductDetail/DFRobot/DFR0888-12?qs=MyNHzdoqoQJ5TOT4n%252BLeCw%3D%3D). [Manufacturer](https://www.dfrobot.com/product-2540.html) identifies 12 WS2812 RGB LEDs, 47 mm OD / 26 mm ID, 3.3–5 V, PH2.0-3P interface and cable included. RGB only, no dedicated white emitter or verified CRI ≥90. Manufacturer lists maximum current <100 mA; do not infer a 1.5–2 W photography output from generic WS2812 specifications. **Cheaper assembled ring, but not selected or qualified for the fill-light requirements.** DigiKey's erroneous one-LED category entry is not the manufacturer bead count.
- **DFRobot FIT0875**, [manufacturer listing](https://www.dfrobot.com/product-2498.html): **$3.90**, preassembled white 6500 K COB light **bar, not a ring**, 60×8×1.7 mm, 5 V / 600 mA / 3 W, heat sink included and required for long-term use. No verified CRI ≥90 or variable white. This would change product geometry and require a lower-power qualification; not selected. Do not claim the rigid 60 mm bar can be bent into a ring.
- AliExpress listing `1005008305573236` could not be accessed through the reader (internal error). Price-aggregator history was not treated as a verified current seller price or authoritative power/CRI evidence. No candidate accepted from it.

Cheaper assembled hardware exists, but no newly reviewed option closes the photography-quality or shared-power integration gates. No PCB, BOM, connector, battery or firmware change was made for this follow-up.
