AnasSarkiz/magnetic-shutter-remote/evidence/R8-components/C15516-listing-text.txt

TPS63031DSKR | Texas Instruments | JLCPCB Coupons Assembly Parts Lib For PCBA Only Upload BOM Search 0 Parts Cart Sign In Sign In Upload BOM Search Products In Stock Parts Bom Tool Request a Quote Support Online Chat > Chat with our live agent for fast reply. Mon-Fri: 24 hours, Sat: 9am-6pm, GMT+8 Email Us > Contact us at support@jlcpcb.com Typically reply within hours. Help Center > Get instant answers. 24/7 Available. Services & Tools Electronic Parts BOM Tool Request a Quote Manufacturers PCB Assembly Support Contact Us How to Order User Guides Sourcing Tips Payment Methods Company About Us Quality Assurance How We Work Certifications Security JLCAPI News Cooperation Careers Electronics EasyEDA JLCPCB JLCDFM LCSC OSHWLAB Mechanical JLC3DP JLCCNC JLCMC Download JLCONE Desktop—Get $524 Exclusive Coupons CONNECT WITH US Services & Tools Electronic Parts BOM Tool Request a Quote Manufacturers PCB Assembly Support Contact Us How to Order User Guides Sourcing Tips Payment Methods Company About Us Quality Assurance How We Work Certifications Security JLCAPI News Cooperation Careers Electronics EasyEDA JLCPCB JLCDFM LCSC OSHWLAB Mechanical JLC3DP JLCCNC JLCMC Download JLCONE Desktop—Get $524 Exclusive Coupons CONNECT WITH US © 2026 JLCPCB.COM All Rights Reserved. Privacy Policy Terms & Conditions Cookies Policy Do Not Sell or Share My Personal Information JLCPCB Parts Library All Components Power Management (PMIC) DC-DC Converters TPS63031DSKR Extended 1 / 4 * Images are for reference only TPS63031DSKR Attributes Value Manufacturer Texas Instruments MFR.Part # TPS63031DSKR JLCPCB Part # C15516 Package SON-10-EP(2.5x2.5) Description -40℃~+125℃@(TJ) 1 1.8V~5.5V 2.4MHz 25uA 3.3V 900mA Buck-Boost Buck-Boost Built-in Fixed Yes SON-10-EP(2.5x2.5) DC-DC Converters ROHS EasyEDA Libraries PCB Footprint or Symbol ECCN EAR99 Datasheet Download Source JLCPCB Assembly Type SMT Assembly PCBA Type Economic and Standard MSL Level MSL 1 Note: The purchased components are stored in your JLCPCB parts library for future PCBA orders only, and cannot be shipped separately. Specifications Attributes Value Category Power Management (PMIC)/DC-DC Converters Manufacturer Texas Instruments Package SON-10-EP(2.5x2.5) Operating Temperature -40℃~+125℃@(TJ) Function Buck-Boost Synchronous Rectifier Yes Frequency - Switching 2.4MHz Output Type Fixed Voltage - Supply 1.8V~5.5V Output Current 900mA Quiescent Current 25uA Features Overcurrent Protection、Light load efficient mode、Load disconnect、Frequency synchronization Switch tube (built-in/external) Built-in Topology Buck-Boost Output Voltage 3.3V Number of Outputs 1 Results remaining : 0 View Similar PCB Assembly Tips Documents PCB Footprint/Symbol Related Products JLCPCB Parts Library All Components Power Management (PMIC) DC-DC Converters TPS63031DSKR * Images are for reference only TPS63031DSKR Extended Manufacturer Texas Instruments MFR.Part # TPS63031DSKR JLCPCB Part # C15516 Package SON-10-EP(2.5x2.5) Description -40℃~+125℃@(TJ) 1 1.8V~5.5V 2.4MHz 25uA 3.3V 900mA Buck-Boost Buck-Boost Built-in Fixed Yes SON-10-EP(2.5x2.5) DC-DC Converters ROHS EasyEDA Libraries PCB Footprint or Symbol ECCN EAR99 Datasheet Download Source JLCPCB Assembly Type SMT Assembly PCBA Type Economic and Standard MSL Level MSL 1 Note: The purchased components are stored in your JLCPCB parts library for future PCBA orders only, and cannot be shipped separately. * Images are for reference only TPS63031DSKR Extended Manufacturer Texas Instruments MFR.Part # TPS63031DSKR JLCPCB Part # C15516 Package SON-10-EP(2.5x2.5) Description -40℃~+125℃@(TJ) 1 1.8V~5.5V 2.4MHz 25uA 3.3V 900mA Buck-Boost Buck-Boost Built-in Fixed Yes SON-10-EP(2.5x2.5) DC-DC Converters ROHS EasyEDA Libraries PCB Footprint or Symbol ECCN EAR99 Datasheet Download Source JLCPCB Assembly Type SMT Assembly PCBA Type Economic and Standard MSL Level MSL 1 Note: The purchased components are stored in your JLCPCB parts library for future PCBA orders only, and cannot be shipped separately. Specifications PCB Assembly Tips Documents PCB Footprint/Symbol TPS63031DSKR Specifications TPS63031DSKR technical specifications, attributes, and parameters. Report an Error? Attributes Value Category Power Management (PMIC)/DC-DC Converters Manufacturer Texas Instruments Package SON-10-EP(2.5x2.5) Operating Temperature -40℃~+125℃@(TJ) Function Buck-Boost Synchronous Rectifier Yes Frequency - Switching 2.4MHz Output Type Fixed Voltage - Supply 1.8V~5.5V Output Current 900mA Quiescent Current 25uA Features Overcurrent Protection、Light load efficient mode、Load disconnect、Frequency synchronization Switch tube (built-in/external) Built-in Topology Buck-Boost Output Voltage 3.3V Number of Outputs 1 Results remaining : 0 View Similar PCB Assembly Tips From components to fully assembled PCBs. JLCPCB supports PCB assembly for the TPS63031DSKR . Sign up to receive and start your assembly today → 1 Step 1 - Pre-order the parts you need from JLCPCB. 2 Step 2 - Place a PCBA order to have those parts assembled onto your boards. 3 Step 3 - JLCPCB manufactures and assembles your boards in as fast as 3 days. Learn more about JLCPCB Assembly TPS63031DSKR Documents TPS63031DSKR datasheets or manufacturer documentation. Datasheet: TPS63031DSKR Datasheet (PDF) TPS63031DSKR Schematic Symbol & PCB Footprint The TPS63031DSKR schematic symbol and PCB footprint are available in the EasyEDA PCB design tool.
