AnasSarkiz/magnetic-shutter-remote/evidence/R8-components/C2934560-listing-text.txt

ESP32-C3-WROOM-02-N4 | Espressif Systems | JLCPCB Coupons Assembly Parts Lib For PCBA Only Upload BOM Search 0 Parts Cart Sign In Sign In Upload BOM Search Products In Stock Parts Bom Tool Request a Quote Support Online Chat > Chat with our live agent for fast reply. Mon-Fri: 24 hours, Sat: 9am-6pm, GMT+8 Email Us > Contact us at support@jlcpcb.com Typically reply within hours. Help Center > Get instant answers. 24/7 Available. Services & Tools Electronic Parts BOM Tool Request a Quote Manufacturers PCB Assembly Support Contact Us How to Order User Guides Sourcing Tips Payment Methods Company About Us Quality Assurance How We Work Certifications Security JLCAPI News Cooperation Careers Electronics EasyEDA JLCPCB JLCDFM LCSC OSHWLAB Mechanical JLC3DP JLCCNC JLCMC Download JLCONE Desktop—Get $524 Exclusive Coupons CONNECT WITH US Services & Tools Electronic Parts BOM Tool Request a Quote Manufacturers PCB Assembly Support Contact Us How to Order User Guides Sourcing Tips Payment Methods Company About Us Quality Assurance How We Work Certifications Security JLCAPI News Cooperation Careers Electronics EasyEDA JLCPCB JLCDFM LCSC OSHWLAB Mechanical JLC3DP JLCCNC JLCMC Download JLCONE Desktop—Get $524 Exclusive Coupons CONNECT WITH US © 2026 JLCPCB.COM All Rights Reserved. Privacy Policy Terms & Conditions Cookies Policy Do Not Sell or Share My Personal Information JLCPCB Parts Library All Components IoT/Communication Modules WiFi Modules ESP32-C3-WROOM-02-N4 Extended 1 / 3 * Images are for reference only ESP32-C3-WROOM-02-N4 Attributes Value Manufacturer Espressif Systems MFR.Part # ESP32-C3-WROOM-02-N4 JLCPCB Part # C2934560 Package SMD,20x18mm Description -105dBm -40℃~+85℃ 2.4GHz 20.5dBm 345mA 3V~3.6V 82mA Bluetooth5.0 ESP32-C3 Chip Integrated Bluetooth function、Support USB interface On-board PCB Antenna UART、SPI、I2C、I2S、JTAG、USB SMD,20x18mm WiFi Modules ROHS EasyEDA Libraries PCB Footprint or Symbol ECCN 5A992C Datasheet Download Source JLCPCB Assembly Type SMT Assembly PCBA Type Economic and Standard MSL Level MSL 3 Note: The purchased components are stored in your JLCPCB parts library for future PCBA orders only, and cannot be shipped separately. Specifications Attributes Value Category IoT/Communication Modules/WiFi Modules Manufacturer Espressif Systems Package SMD,20x18mm Antenna Type On-board PCB Antenna Operating Temperature -40℃~+85℃ Sensitivity -105dBm Output Power 20.5dBm Voltage - Supply 3V~3.6V Frequency 2.4GHz Features Integrated Bluetooth function、Support USB interface Utilized IC / Part ESP32-C3 Chip Interface Type UART、SPI、I2C、I2S、JTAG、USB Receive  Current 82mA Wireless Standard Bluetooth5.0 Send  Current 345mA Results remaining : 0 View Similar PCB Assembly Tips Documents PCB Footprint/Symbol Related Products JLCPCB Parts Library All Components IoT/Communication Modules WiFi Modules ESP32-C3-WROOM-02-N4 * Images are for reference only ESP32-C3-WROOM-02-N4 Extended Manufacturer Espressif Systems MFR.Part # ESP32-C3-WROOM-02-N4 JLCPCB Part # C2934560 Package SMD,20x18mm Description -105dBm -40℃~+85℃ 2.4GHz 20.5dBm 345mA 3V~3.6V 82mA Bluetooth5.0 ESP32-C3 Chip Integrated Bluetooth function、Support USB interface On-board PCB Antenna UART、SPI、I2C、I2S、JTAG、USB SMD,20x18mm WiFi Modules ROHS EasyEDA Libraries PCB Footprint or Symbol ECCN 5A992C Datasheet Download Source JLCPCB Assembly Type SMT Assembly PCBA Type Economic and Standard MSL Level MSL 3 Note: The purchased components are stored in your JLCPCB parts library for future PCBA orders only, and cannot be shipped separately. * Images are for reference only ESP32-C3-WROOM-02-N4 Extended Manufacturer Espressif Systems MFR.Part # ESP32-C3-WROOM-02-N4 JLCPCB Part # C2934560 Package SMD,20x18mm Description -105dBm -40℃~+85℃ 2.4GHz 20.5dBm 345mA 3V~3.6V 82mA Bluetooth5.0 ESP32-C3 Chip Integrated Bluetooth function、Support USB interface On-board PCB Antenna UART、SPI、I2C、I2S、JTAG、USB SMD,20x18mm WiFi Modules ROHS EasyEDA Libraries PCB Footprint or Symbol ECCN 5A992C Datasheet Download Source JLCPCB Assembly Type SMT Assembly PCBA Type Economic and Standard MSL Level MSL 3 Note: The purchased components are stored in your JLCPCB parts library for future PCBA orders only, and cannot be shipped separately. Specifications PCB Assembly Tips Documents PCB Footprint/Symbol ESP32-C3-WROOM-02-N4 Specifications ESP32-C3-WROOM-02-N4 technical specifications, attributes, and parameters. Report an Error? Attributes Value Category IoT/Communication Modules/WiFi Modules Manufacturer Espressif Systems Package SMD,20x18mm Antenna Type On-board PCB Antenna Operating Temperature -40℃~+85℃ Sensitivity -105dBm Output Power 20.5dBm Voltage - Supply 3V~3.6V Frequency 2.4GHz Features Integrated Bluetooth function、Support USB interface Utilized IC / Part ESP32-C3 Chip Interface Type UART、SPI、I2C、I2S、JTAG、USB Receive  Current 82mA Wireless Standard Bluetooth5.0 Send  Current 345mA Results remaining : 0 View Similar PCB Assembly Tips From components to fully assembled PCBs. JLCPCB supports PCB assembly for the ESP32-C3-WROOM-02-N4 . Sign up to receive and start your assembly today → 1 Step 1 - Pre-order the parts you need from JLCPCB. 2 Step 2 - Place a PCBA order to have those parts assembled onto your boards. 3 Step 3 - JLCPCB manufactures and assembles your boards in as fast as 3 days. Learn more about JLCPCB Assembly ESP32-C3-WROOM-02-N4 Documents ESP32-C3-WROOM-02-N4 datasheets or manufacturer documentation. Datasheet: ESP32-C3-WROOM-02-N4 Datasheet (PDF) ESP32-C3-WROOM-02-N4 Schematic Symbol & PCB Footprint The ESP32-C3-WROOM-02-N4 schematic symbol and PCB footprint are available in the EasyEDA PCB design tool.
