AnasSarkiz/magnetic-shutter-remote/evidence/R8-components/ESP32-GEOMETRY.md

# ESP32-C3 footprint audit

| Terminal | X (mm) | Y (mm) | Imported copper (mm) | Espressif recommendation (mm) |
|---|---:|---:|---|---|
| 1 | -8.750046 | 5.999988 | 1.9999960 × 0.9999980 | 1.5 × 0.9 |
| 2 | -8.750046 | 4.500118 | 1.9999960 × 0.9999980 | 1.5 × 0.9 |
| 3 | -8.750046 | 2.999994 | 1.9999960 × 0.9999980 | 1.5 × 0.9 |
| 4 | -8.750046 | 1.500124 | 1.9999960 × 0.9999980 | 1.5 × 0.9 |
| 5 | -8.750046 | 0.000000 | 1.9999960 × 0.9999980 | 1.5 × 0.9 |
| 6 | -8.750046 | -1.499870 | 1.9999960 × 0.9999980 | 1.5 × 0.9 |
| 7 | -8.750046 | -2.999994 | 1.9999960 × 0.9999980 | 1.5 × 0.9 |
| 8 | -8.750046 | -4.499864 | 1.9999960 × 0.9999980 | 1.5 × 0.9 |
| 9 | -8.750046 | -5.999988 | 1.9999960 × 0.9999980 | 1.5 × 0.9 |
| 10 | 8.750046 | -5.999988 | 1.9999960 × 0.9999980 | 1.5 × 0.9 |
| 11 | 8.750046 | -4.499864 | 1.9999960 × 0.9999980 | 1.5 × 0.9 |
| 12 | 8.750046 | -2.999994 | 1.9999960 × 0.9999980 | 1.5 × 0.9 |
| 13 | 8.750046 | -1.499870 | 1.9999960 × 0.9999980 | 1.5 × 0.9 |
| 14 | 8.750046 | 0.000000 | 1.9999960 × 0.9999980 | 1.5 × 0.9 |
| 15 | 8.750046 | 1.500124 | 1.9999960 × 0.9999980 | 1.5 × 0.9 |
| 16 | 8.750046 | 2.999994 | 1.9999960 × 0.9999980 | 1.5 × 0.9 |
| 17 | 8.750046 | 4.500118 | 1.9999960 × 0.9999980 | 1.5 × 0.9 |
| 18 | 8.750046 | 5.999988 | 1.9999960 × 0.9999980 | 1.5 × 0.9 |
| 19 | -0.139954 | 0.900176 | 0.6999986 × 0.6999986 | 0.7 × 0.7 |
| 19 | -0.139954 | -0.199898 | 0.6999986 × 0.6999986 | 0.7 × 0.7 |
| 19 | -0.139954 | -1.299972 | 0.6999986 × 0.6999986 | 0.7 × 0.7 |
| 19 | 0.959866 | 0.900176 | 0.6999986 × 0.6999986 | 0.7 × 0.7 |
| 19 | 0.959866 | -0.199898 | 0.6999986 × 0.6999986 | 0.7 × 0.7 |
| 19 | 0.959866 | -1.299972 | 0.6999986 × 0.6999986 | 0.7 × 0.7 |
| 19 | 2.059940 | -1.299972 | 0.6999986 × 0.6999986 | 0.7 × 0.7 |
| 19 | 2.059940 | -0.199898 | 0.6999986 × 0.6999986 | 0.7 × 0.7 |
| 19 | 2.059940 | 0.900176 | 0.6999986 × 0.6999986 | 0.7 × 0.7 |

Source → import geometry maximum difference: 5.084821452783217e-14 mm.
Pin 19 has nine ground tiles. No source or import was altered.
Recommendations are not manufacturer-published dimensional tolerances. Larger lands are an unqualified variation, not proof the physical part cannot fit.
