AnasSarkiz/magnetic-shutter-remote/evidence/R7-components/al1793-land-pattern.png

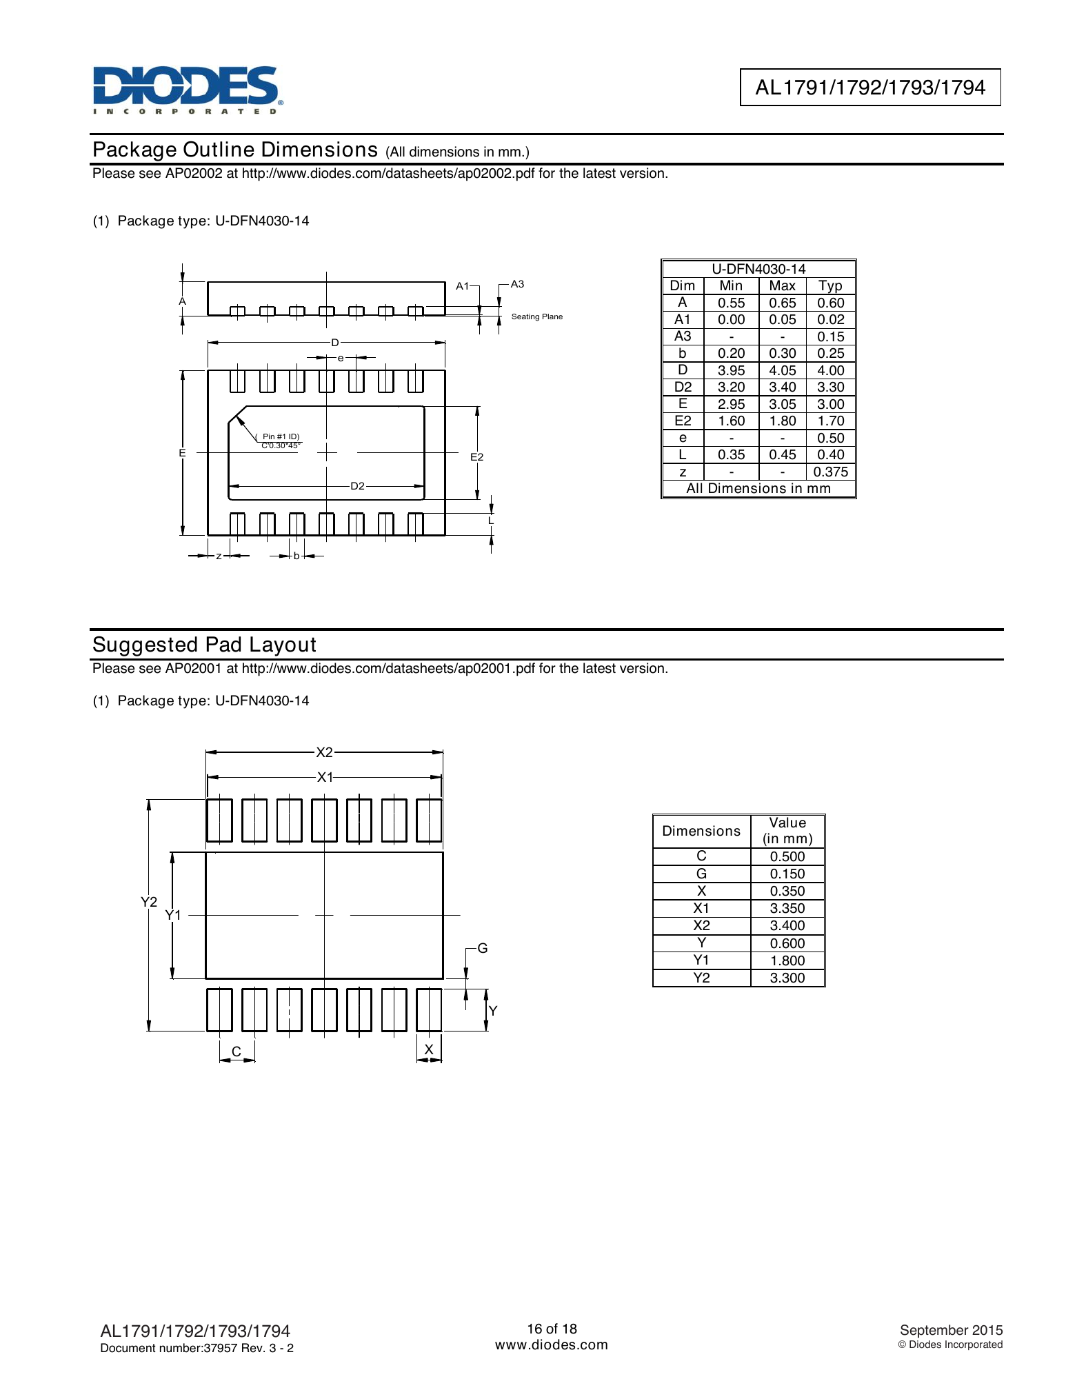
evidence/R7-components/al1793-land-pattern.png
