AnasSarkiz/magnetic-shutter-remote/evidence/R7-components/al8860-land-pattern.png

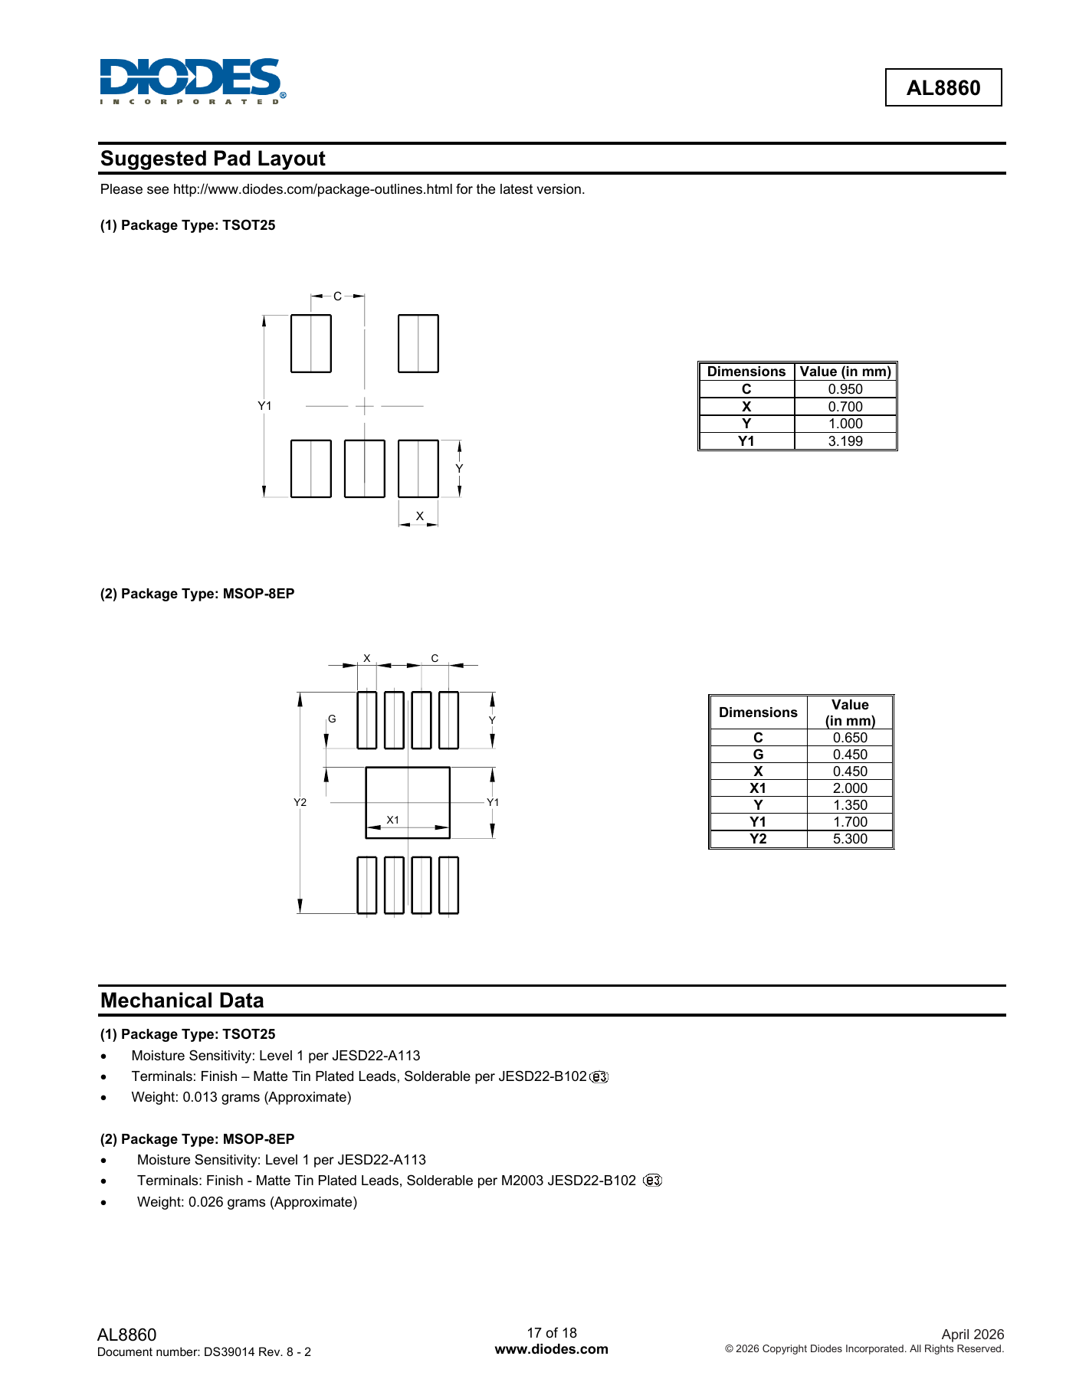
evidence/R7-components/al8860-land-pattern.png
