AnasSarkiz/magnetic-shutter-remote/evidence/R7-components/jauch-850-dimensions.png

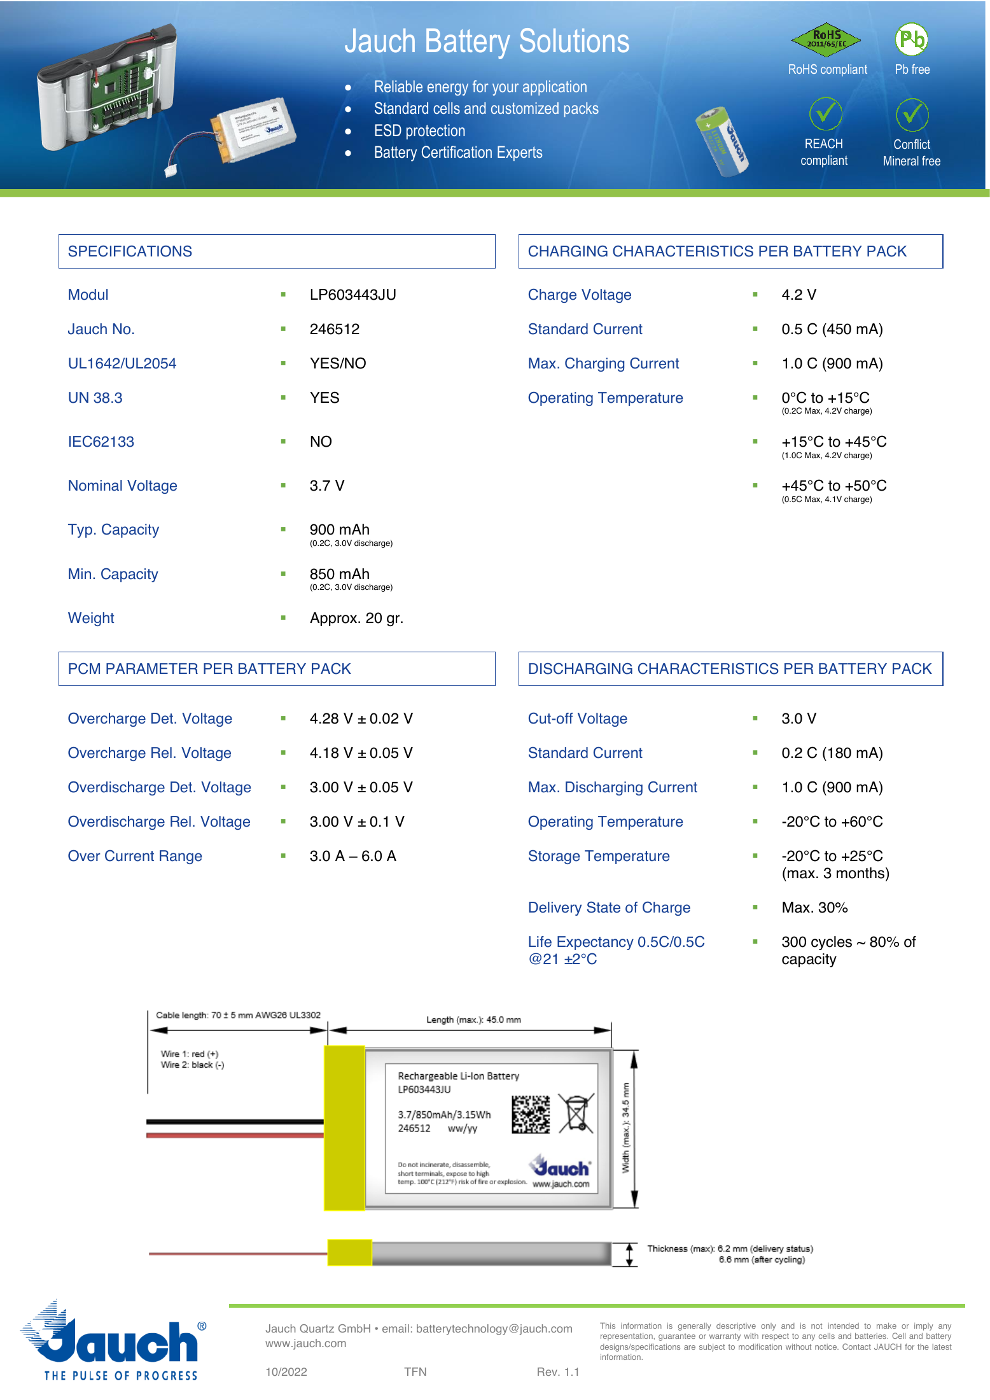
evidence/R7-components/jauch-850-dimensions.png
