AnasSarkiz/magnetic-shutter-remote/evidence/R7-components/jst-land-pattern.png

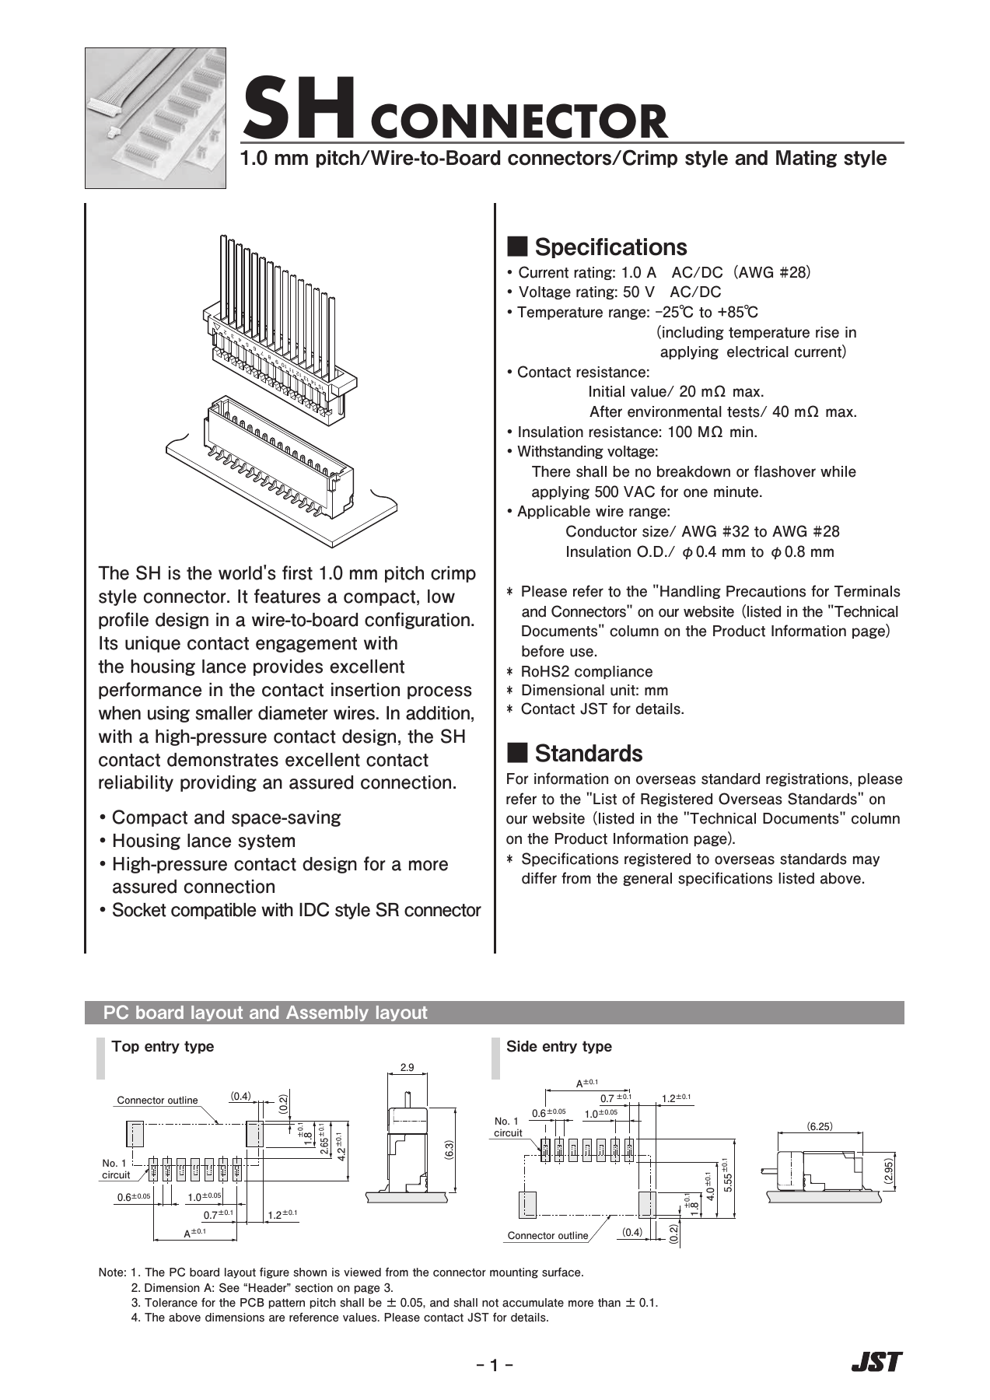
evidence/R7-components/jst-land-pattern.png
