AnasSarkiz/magnetic-shutter-remote/evidence/R7-components/osram-page-15.png

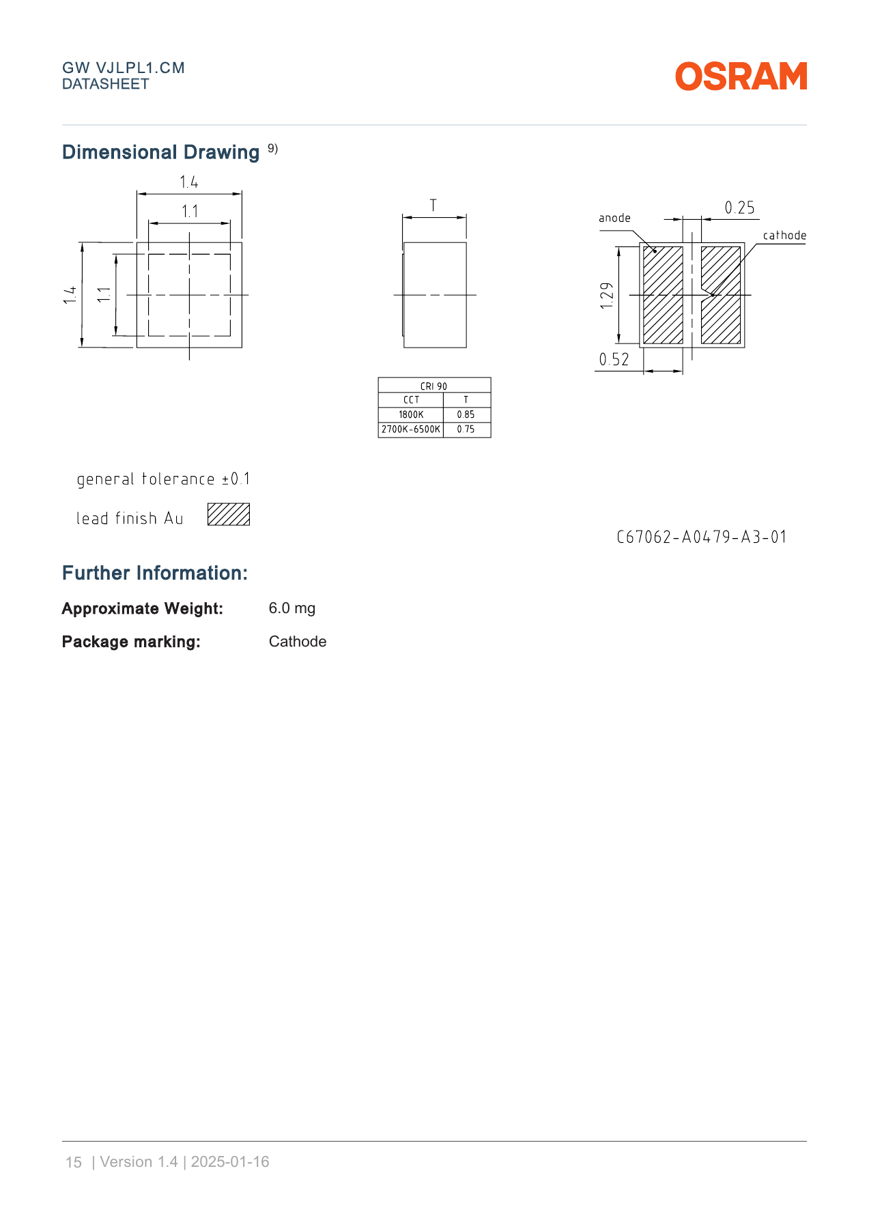
evidence/R7-components/osram-page-15.png
