AnasSarkiz/magnetic-shutter-remote/evidence/R7-components/osram-page-16.png

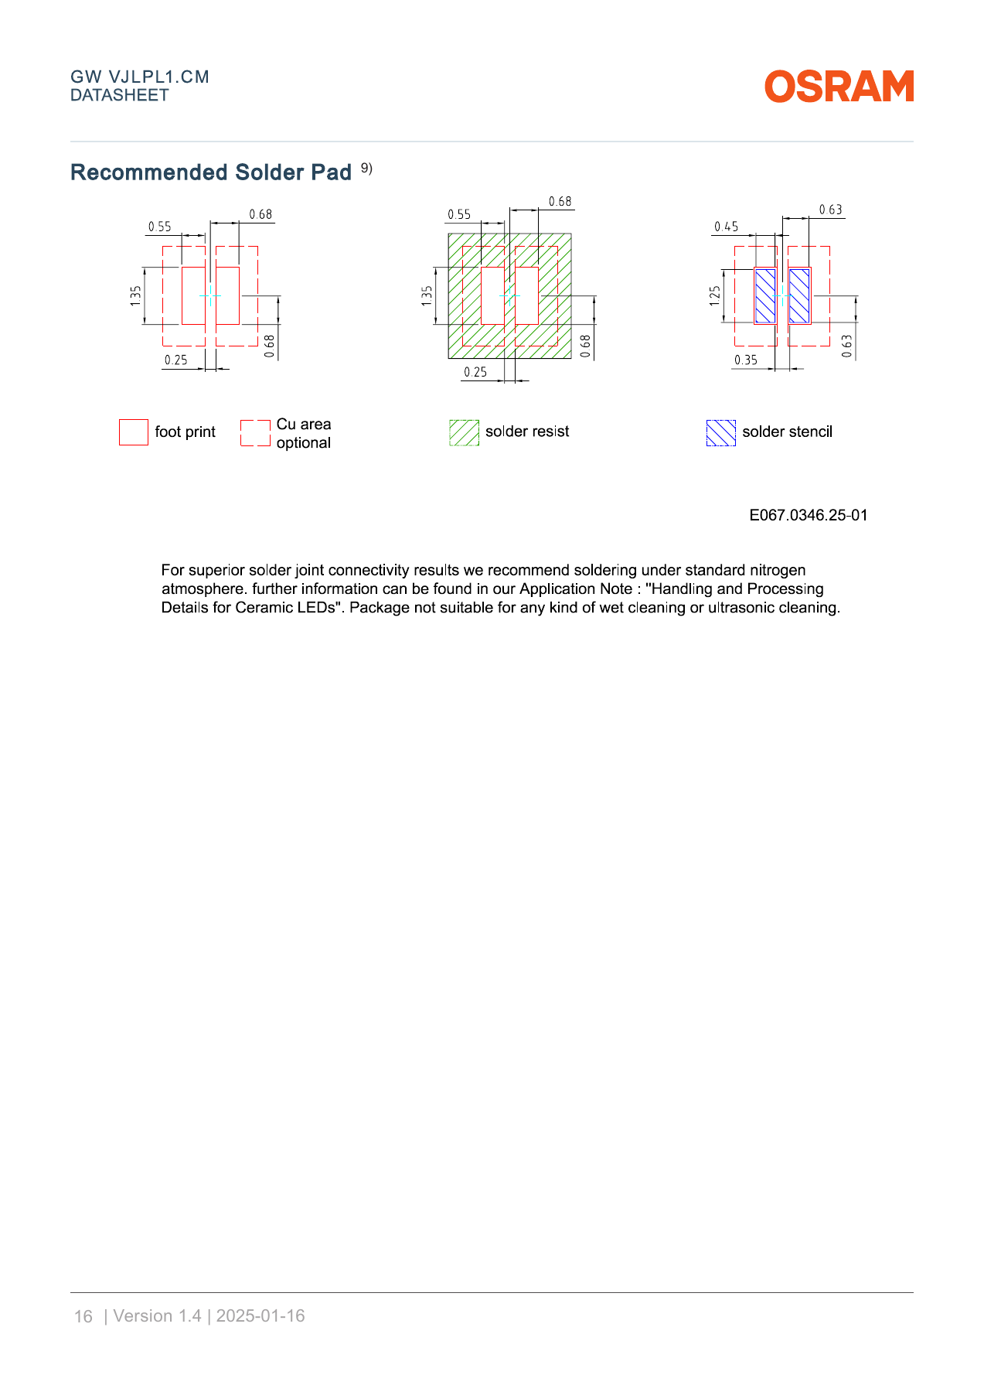
evidence/R7-components/osram-page-16.png
