AnasSarkiz/magnetic-shutter-remote/evidence/R7-components/osram-page-17.png

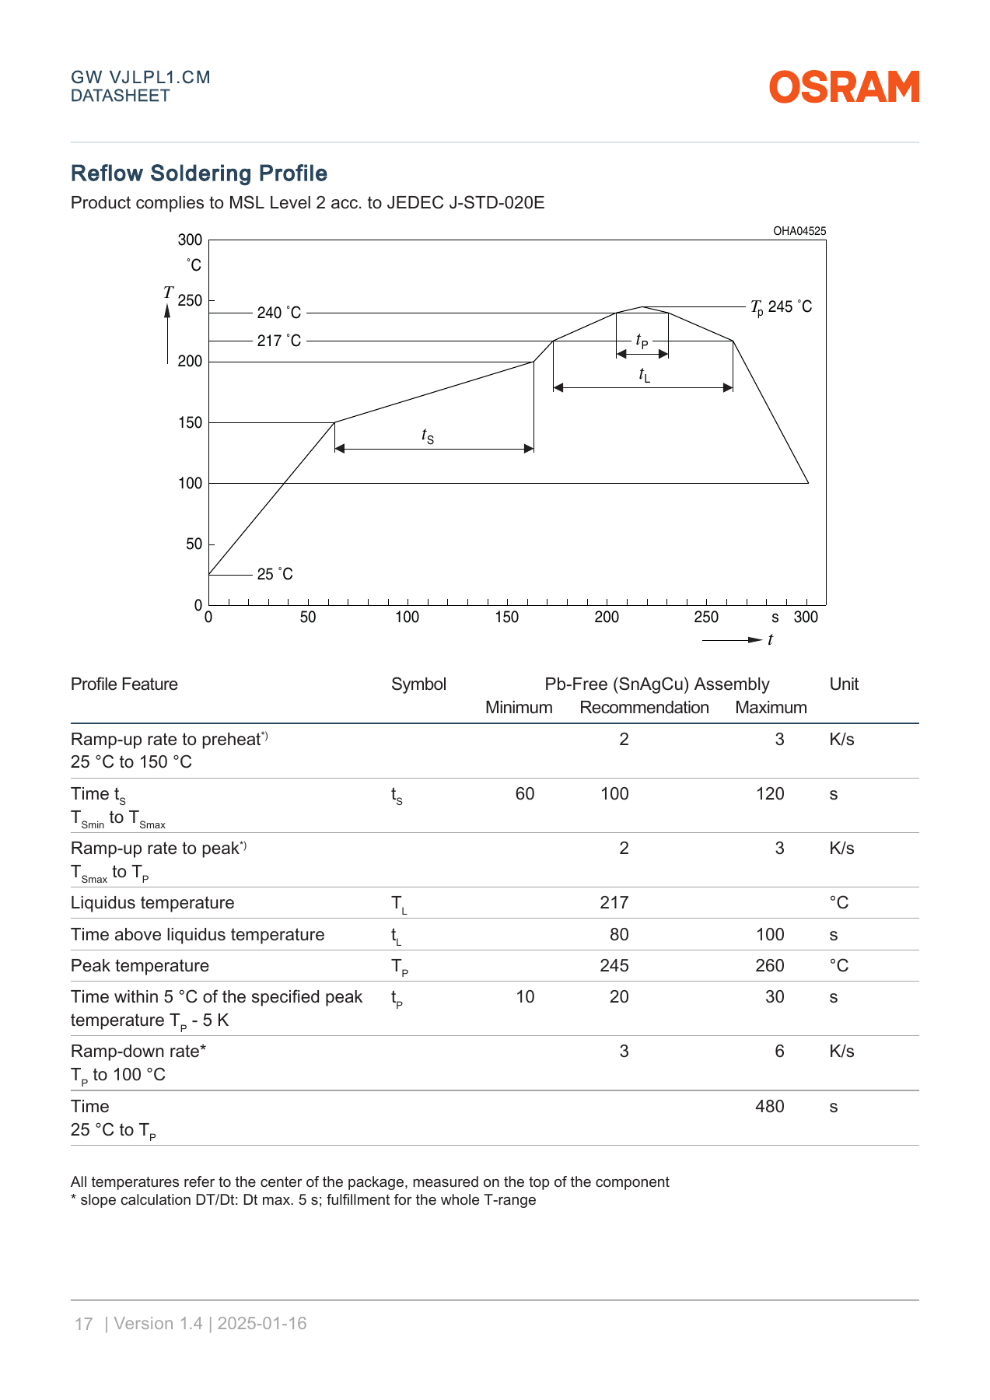
evidence/R7-components/osram-page-17.png
