AnasSarkiz/magnetic-shutter-remote/evidence/R7-components/osram-reflow-profile.png

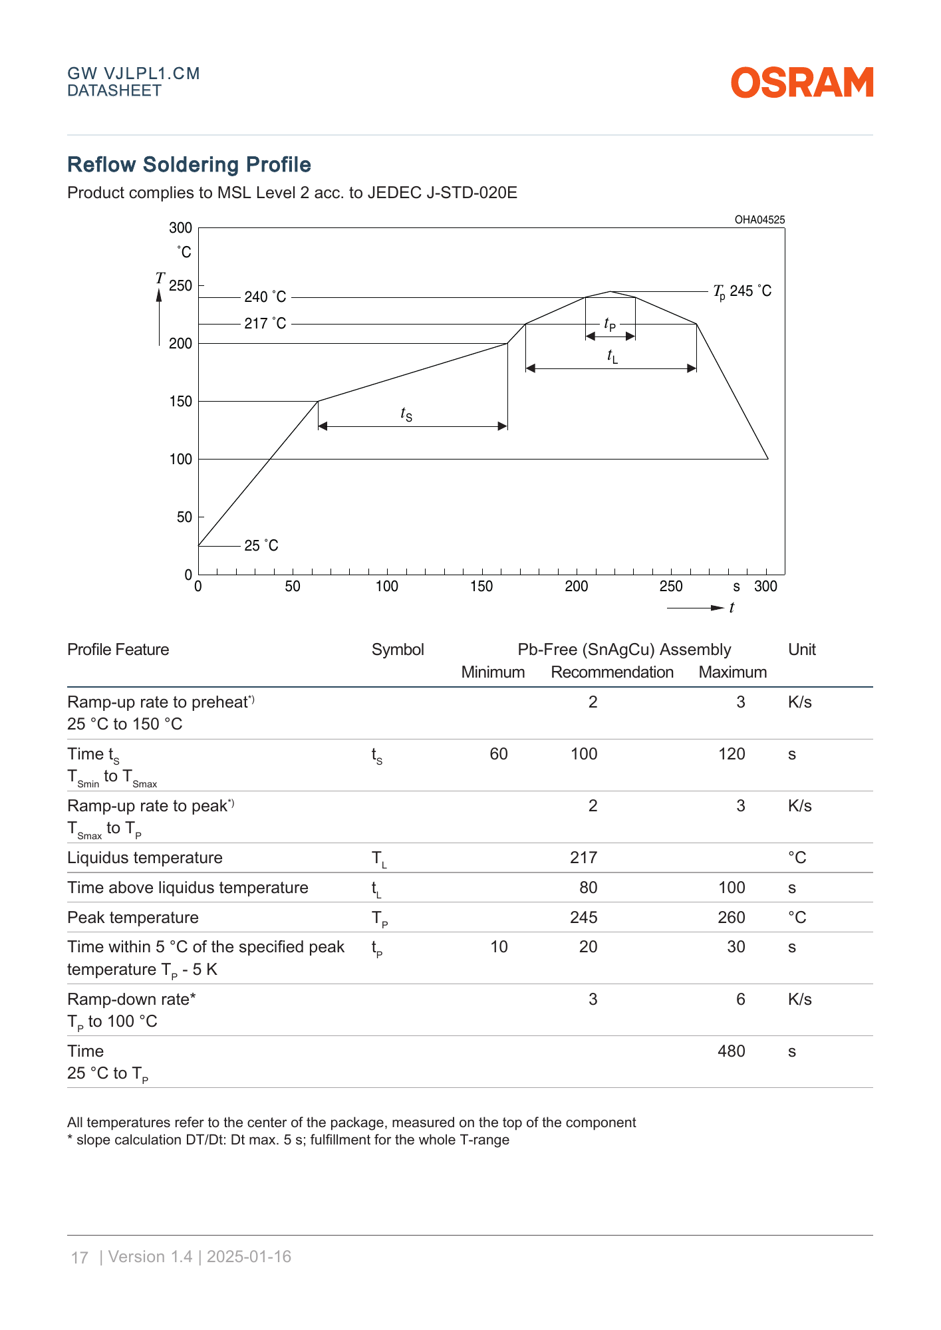
evidence/R7-components/osram-reflow-profile.png
