AnasSarkiz/magnetic-shutter-remote/evidence/R7-components/pt4115-package.png

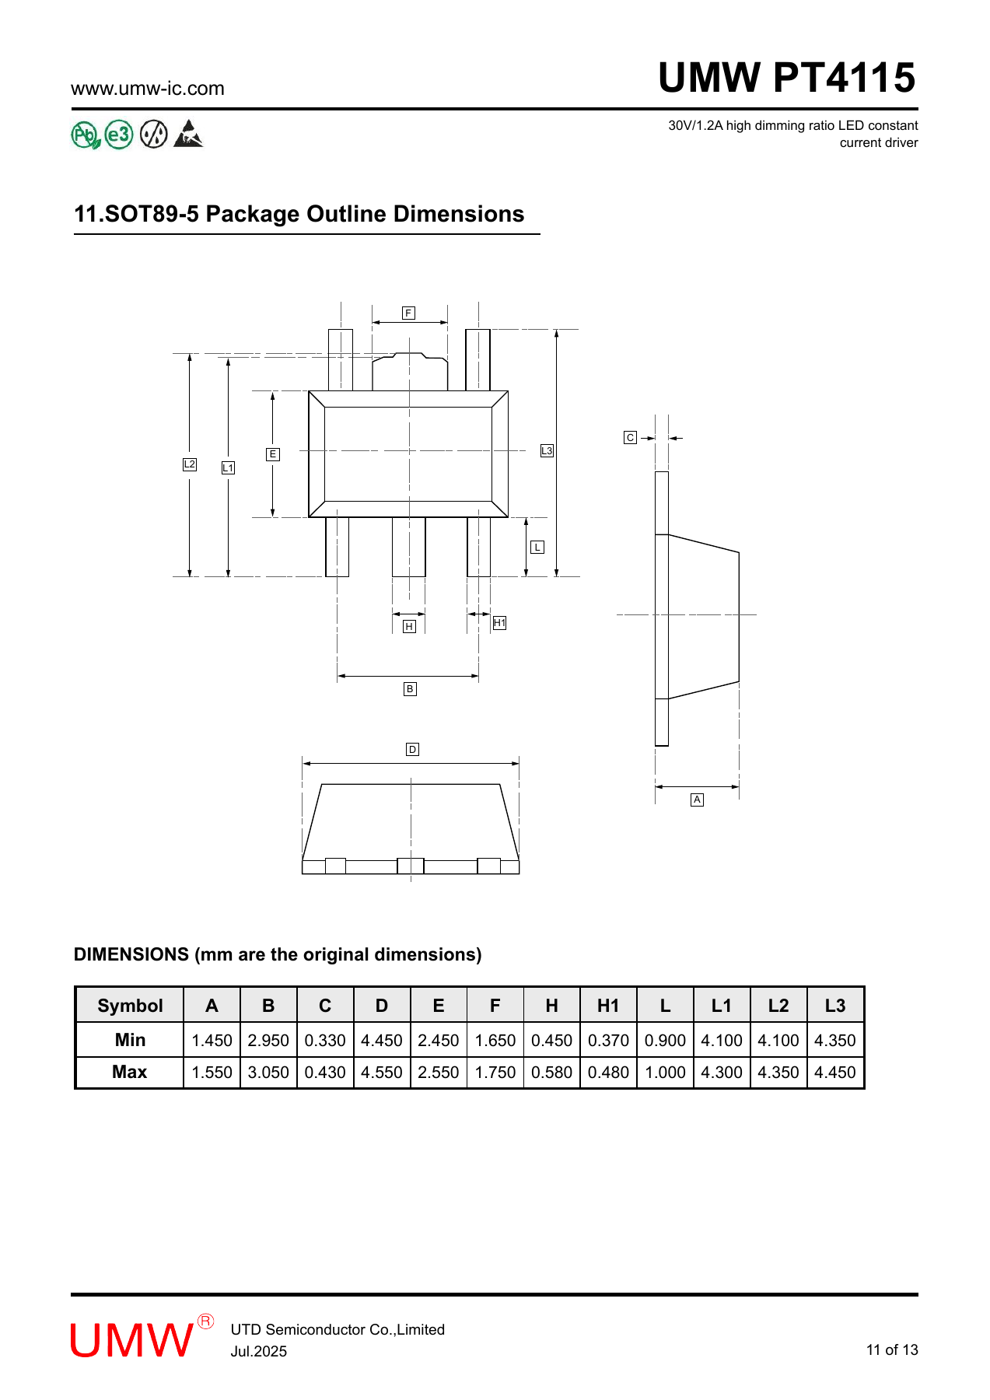
evidence/R7-components/pt4115-package.png
