AnasSarkiz/magnetic-shutter-remote/evidence/R7-components/pt4115-paste-cam.png

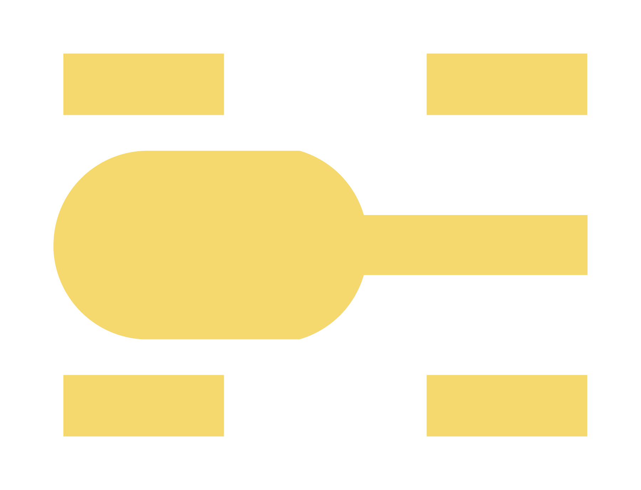
evidence/R7-components/pt4115-paste-cam.png
