AnasSarkiz/magnetic-shutter-remote/evidence/R7-order-review/board-dimensions.png

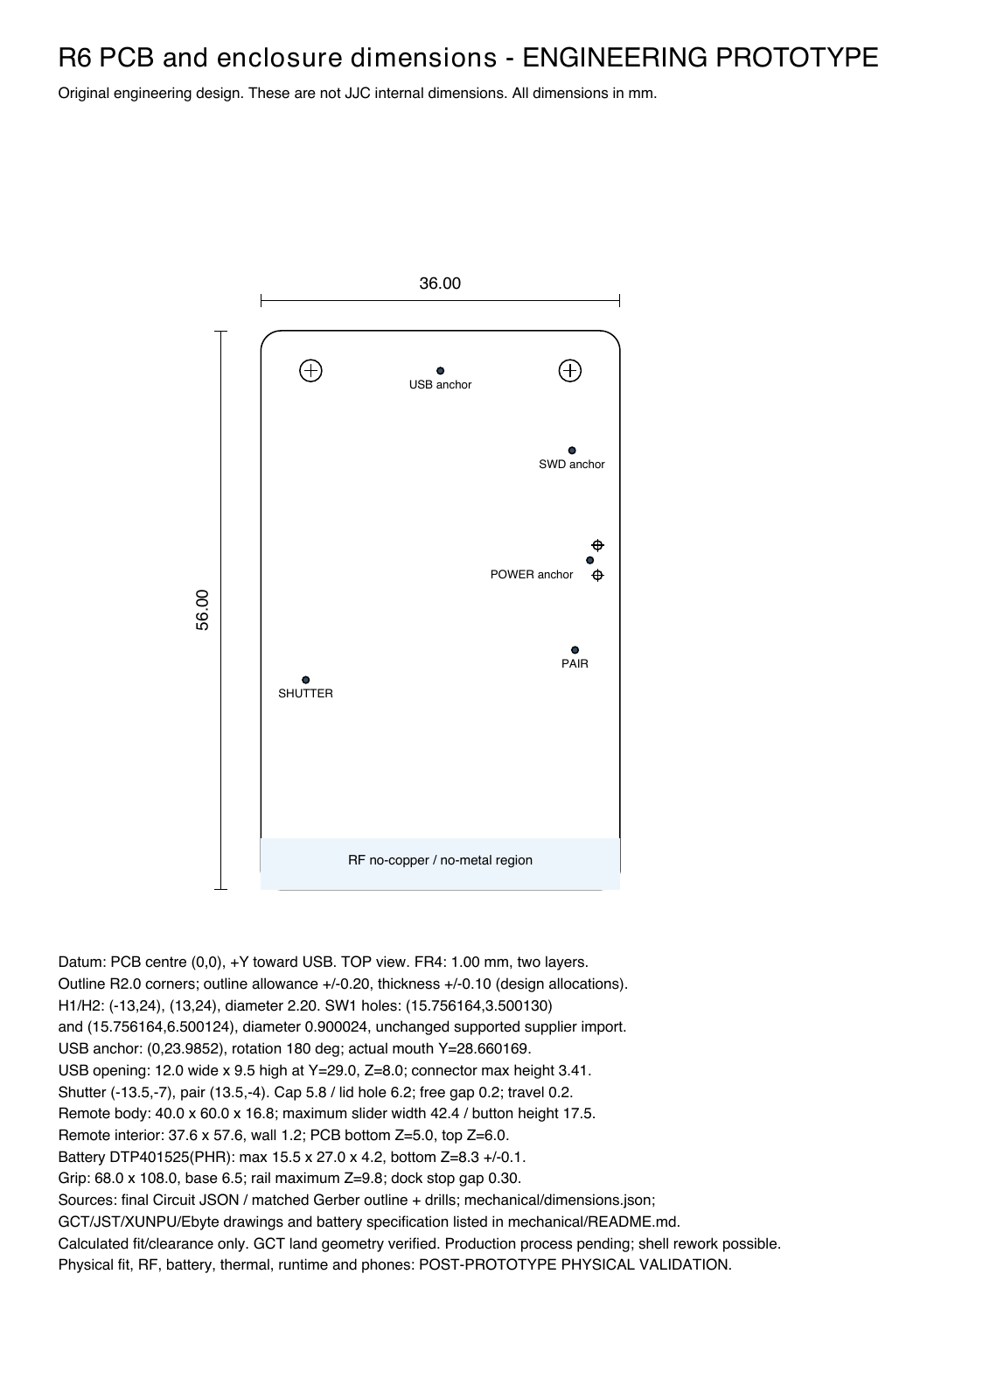
evidence/R7-order-review/board-dimensions.png
