AnasSarkiz/magnetic-shutter-remote/evidence/R7-order-review/J1-actual-cam-overlay.png

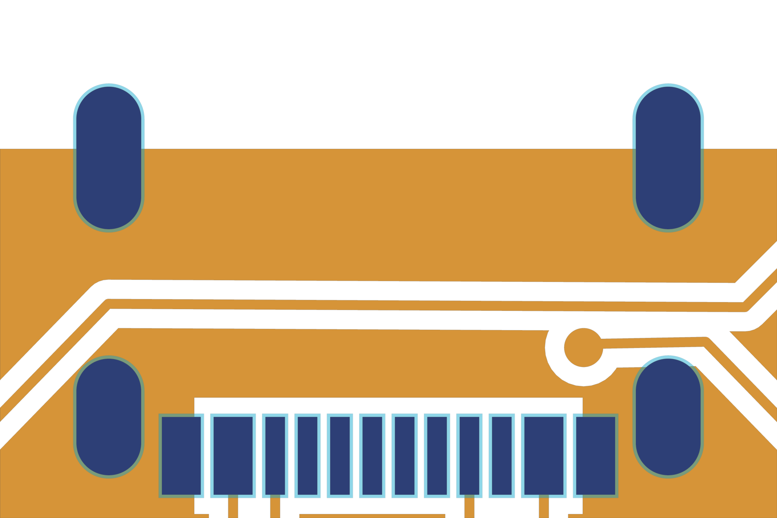
evidence/R7-order-review/J1-actual-cam-overlay.png
