AnasSarkiz/magnetic-shutter-remote/evidence/R7-order-review/visual/B_Mask.png

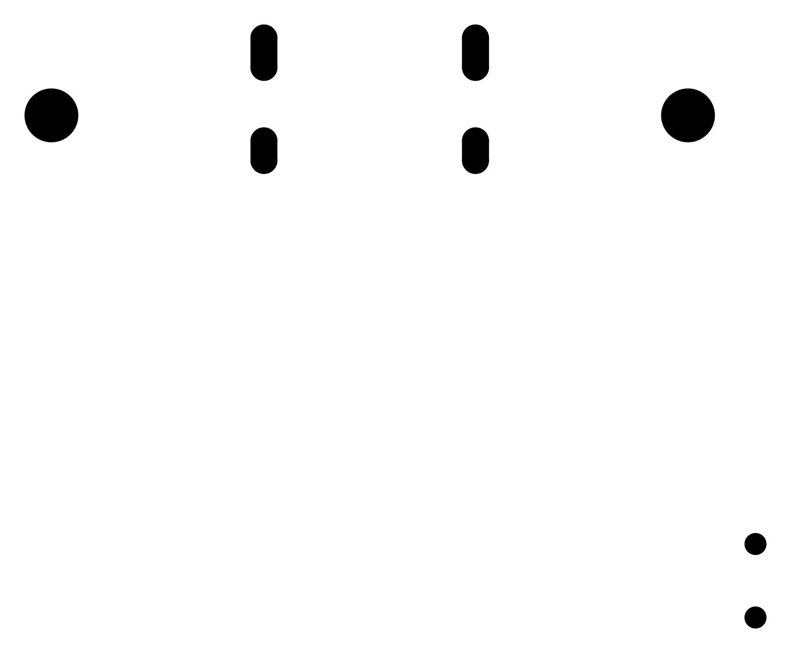
evidence/R7-order-review/visual/B_Mask.png
