AnasSarkiz/magnetic-shutter-remote/evidence/R7-order-review/visual/CAM-top-all-drills.png

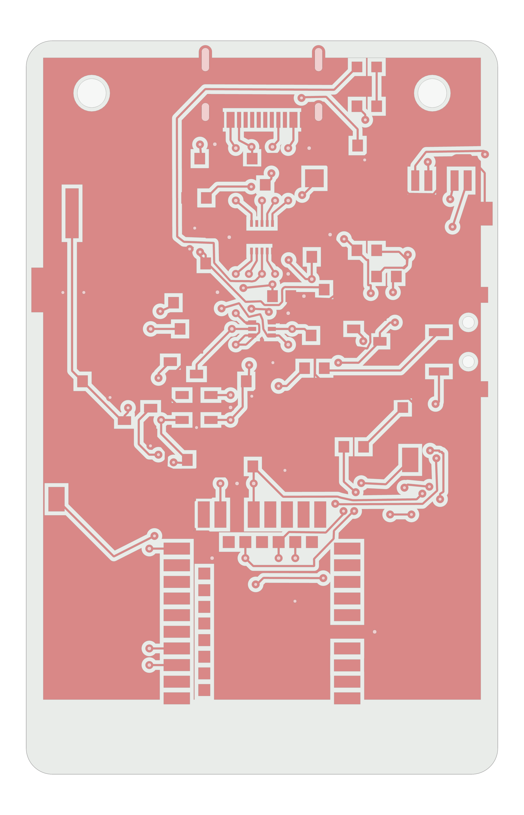
evidence/R7-order-review/visual/CAM-top-all-drills.png
