AnasSarkiz/magnetic-shutter-remote/evidence/R7-order-review/visual/Edge_Cuts.png

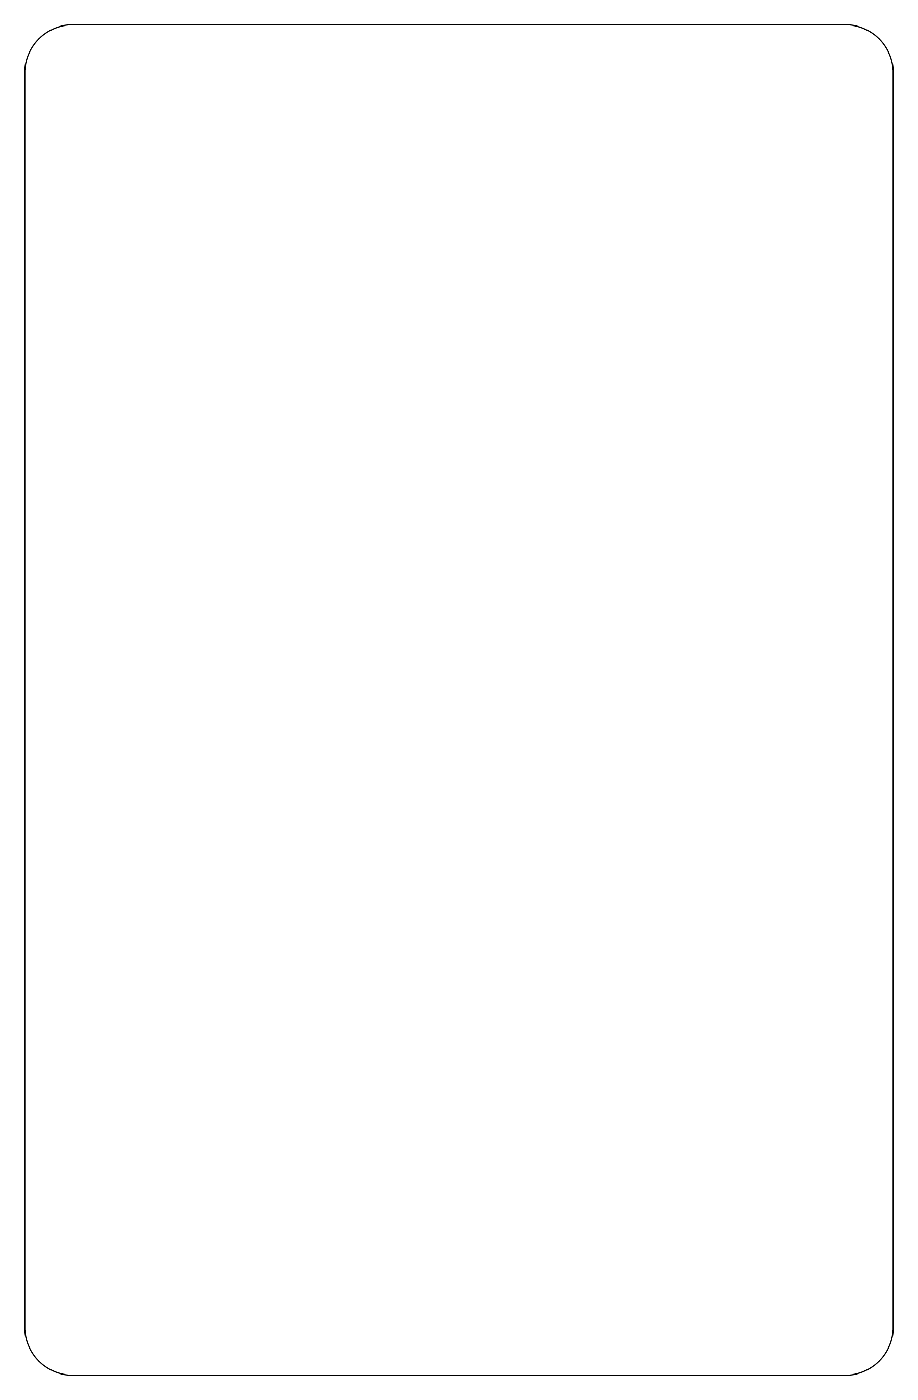
evidence/R7-order-review/visual/Edge_Cuts.png
