AnasSarkiz/magnetic-shutter-remote/evidence/R7-order-review/visual/F_Mask.png

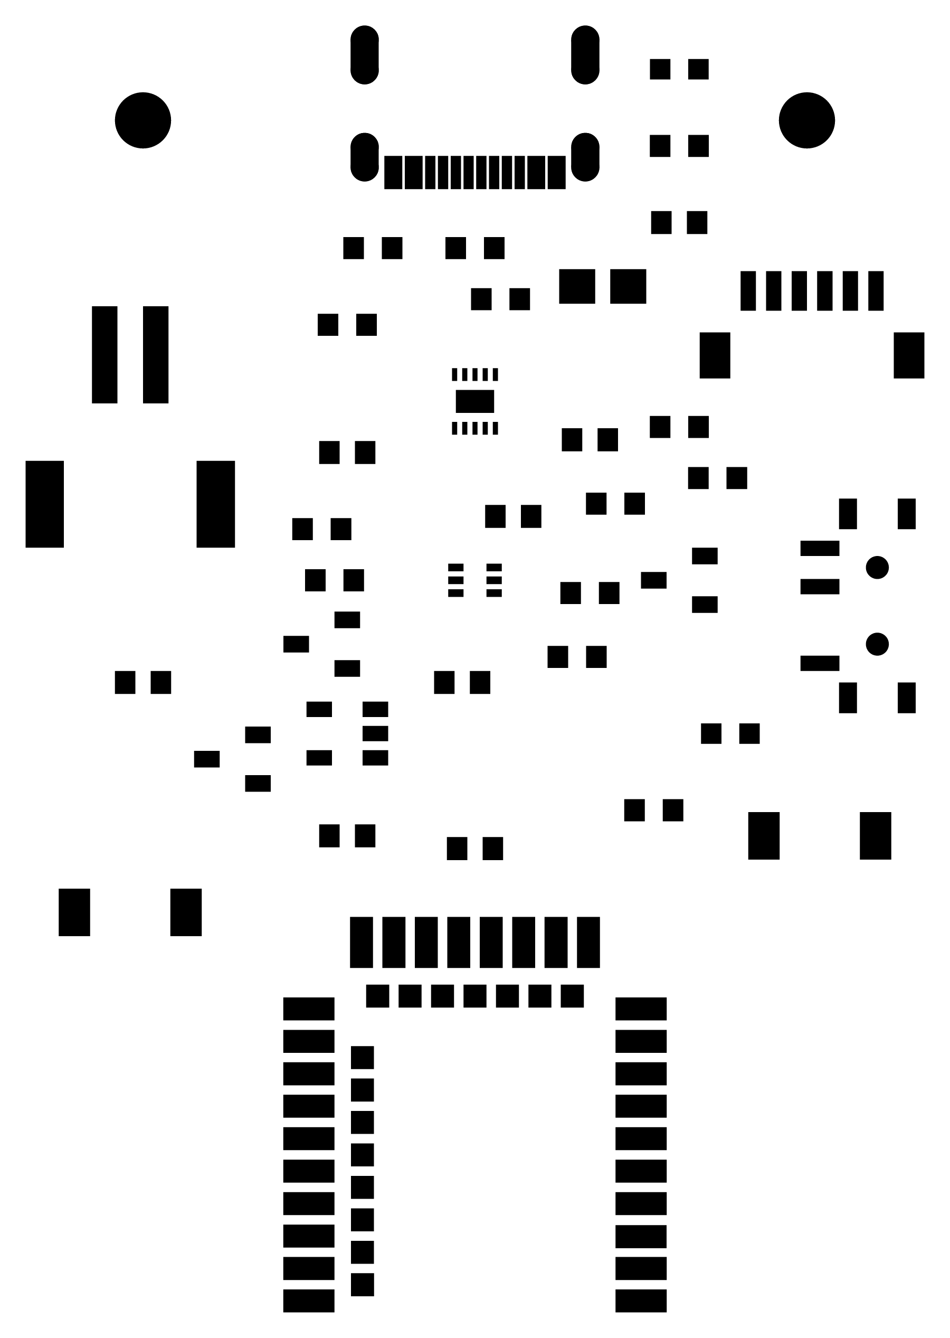
evidence/R7-order-review/visual/F_Mask.png
