AnasSarkiz/magnetic-shutter-remote/evidence/R7-order-review/visual/F_Paste.png

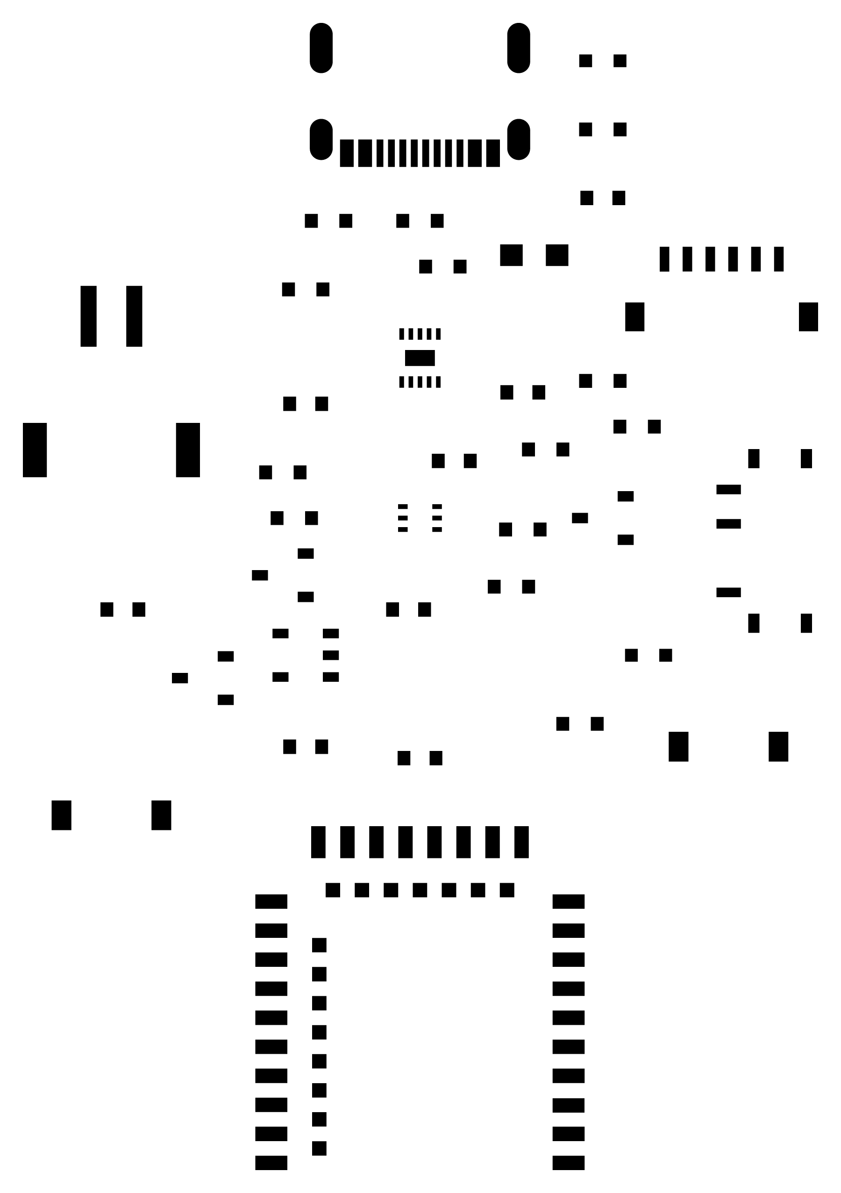
evidence/R7-order-review/visual/F_Paste.png
