AnasSarkiz/magnetic-shutter-remote/evidence/R8-components/esp32-dimensions.png

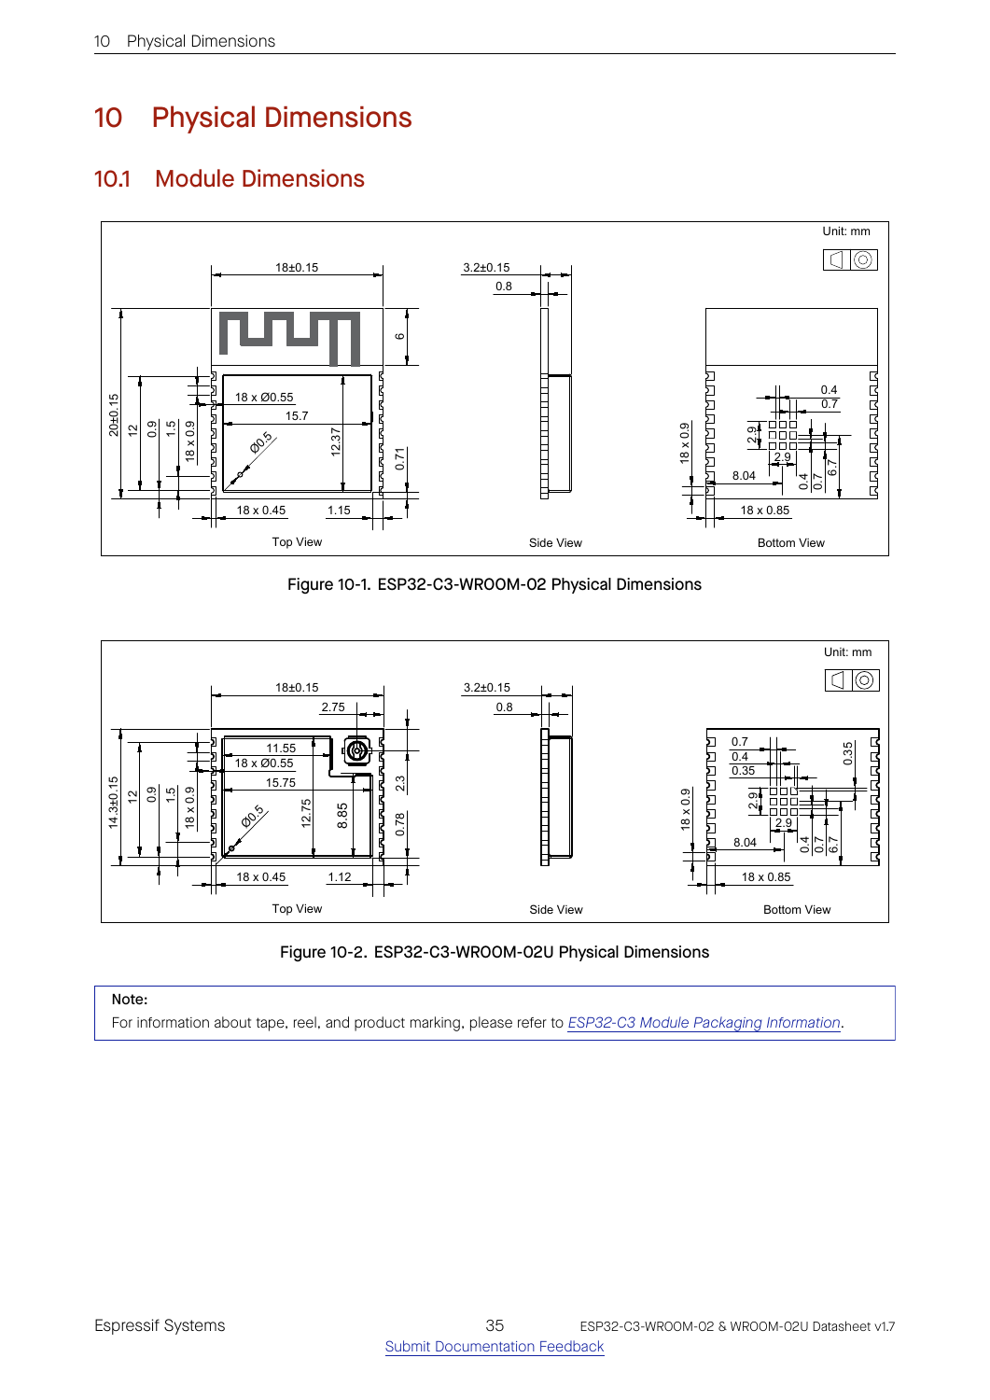
evidence/R8-components/esp32-dimensions.png
