AnasSarkiz/magnetic-shutter-remote/evidence/R8-components/official-devkit-top.png

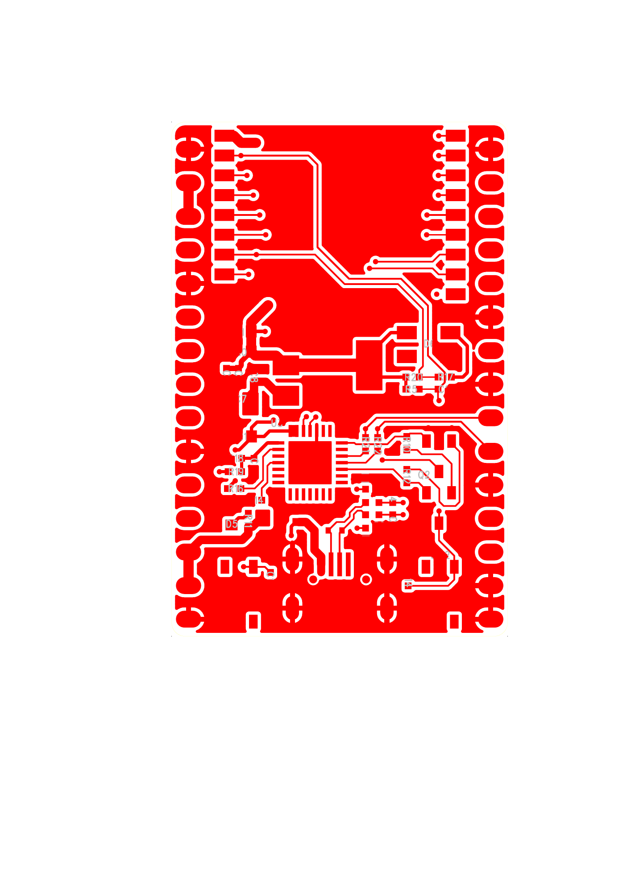
evidence/R8-components/official-devkit-top.png
