AnasSarkiz/magnetic-shutter-remote/evidence/R7-order-review/assembly-top.png

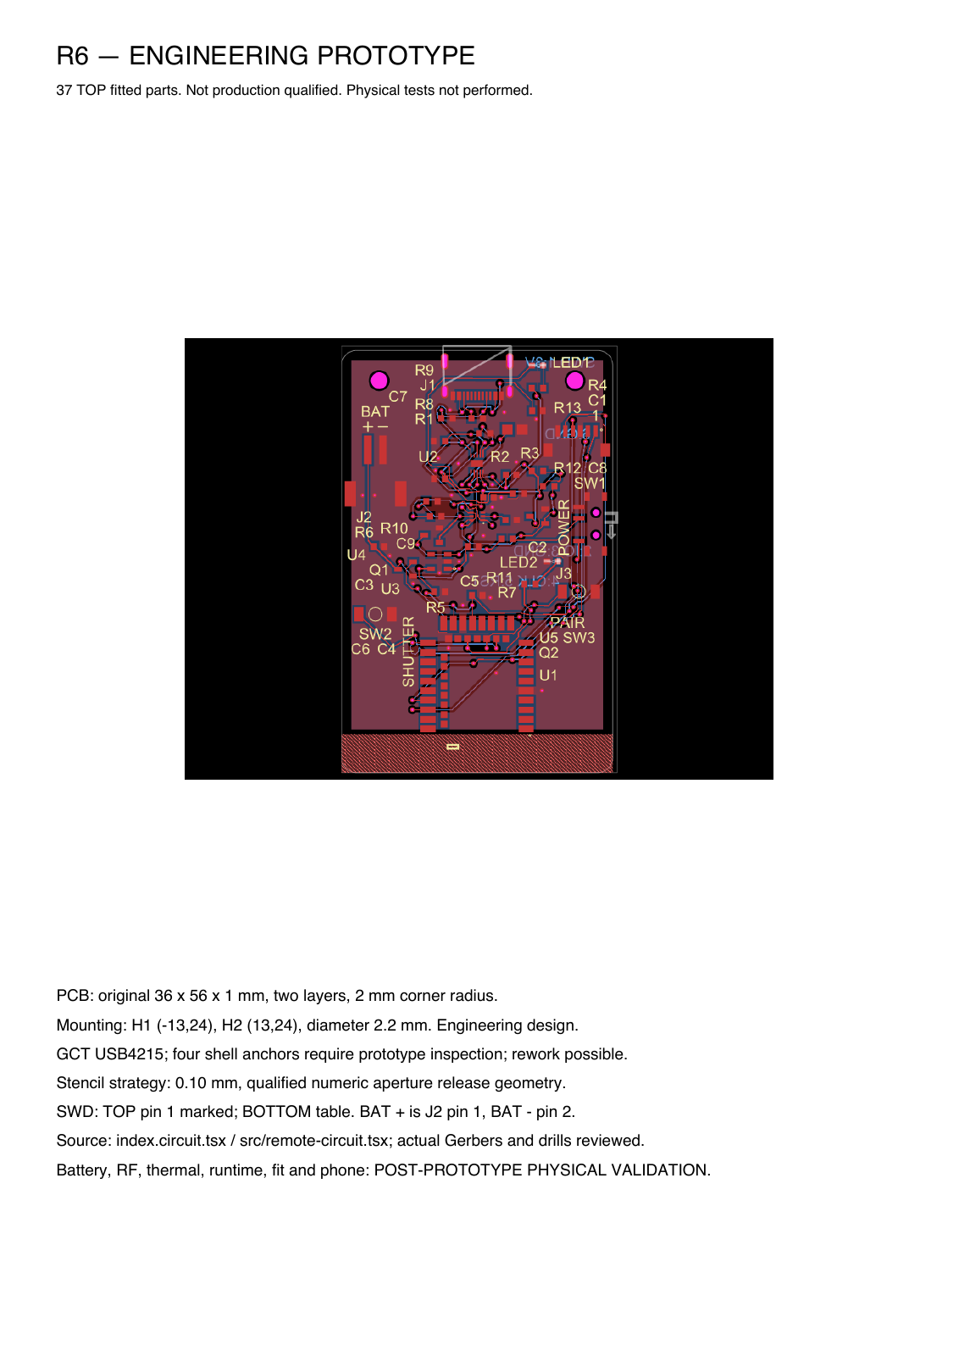
evidence/R7-order-review/assembly-top.png
