AnasSarkiz/magnetic-shutter-remote/tscircuit-issues/065-r6-clone-retains-stale-secondary-previews.md

# R6 clone initially retained secondary previews from R5

**Status: fixed locally. Classification: project artifact inventory mistake, not a confirmed tscircuit footprint or copper defect.**

R6started as an isolated copy of R5. Current CLIbuild produced fresh pcb.svg/png, schematic.svg, schematic_sheet_*.svg/png,3d.png and3d.glb. Extra copied files board.glb/final-pcb-bottom.png/final-schematic-sheet-*.png retained R5dates and the old USBconnector. They must not be presented as R6outputs.

Affected producer: @tscircuit/cli0.1.2237/tscircuit0.0.2702; stale files were copied project artifacts, not outputs falsely claimed to be generated by that command. J1changed HCTLHC-TYPE-C-6P-01A/C2894893 → GCTUSB4215-03-A/C37616412. [Official current geometry](../references/GCT-USB4215-drawing-Rev-A.pdf).

Reproduction: copy R5into an isolated R6directory, replace J1through the supported importer, run `tsci build index.circuit.tsx --pcb-png --pcb-svgs --schematic-svgs --3d-png --glbs`, then list existing dist/index filenames/dates. Expected release inventory contains only current generated artifacts. Actual draft inventory initially selected all files, including copied secondary files. No released R6ZIPexisted at discovery.

Confirmed cause: recursive copy plus overbroad package inventory. Source/geometry/CAMunaffected. Fix: supported native `convertCircuitJsonToPcbSvg`BOTTOM rendering from the final schema-valid CircuitJSON; explicit current-preview hash manifest and excluded legacy names. Package builder excludes the copied board.glb/final-* files; original R5files remain immutable. `scripts/render-r6-pcb.ts`and `scripts/package_r6_prototype.py`contain the source fix; no generated previews hand-edited.

Evidence: [current render log](../evidence/R6/current-preview-render.log), [hash/producer inventory](../evidence/R6/current-preview-outputs.json), [current BOTTOM image](../dist/index/pcb-bottom.png), [actual 3D37-mesh coverage](../evidence/R6/3d-coverage.json). Regression verifies exact archive inventory against this current-output manifest and refuses legacy filenames. Final package integrity/preview review pass. No current PCBsource, routing, Gerbers or drills changed during this repair.

Impact: stale illustrations could misrepresent connector/routing/mechanical position. Closed before prototype release; no upstream publication or issue created.
