AnasSarkiz/magnetic-shutter-remote/evidence/USB4215-import-audit/tscircuit-issues/059-full-importer-suite-residual-failures.md

# Full importer regression gate still has residual baseline failures

Status: **suspected** compatibility/test-expectation failures requiring triage. No confirmed new tscircuit bug is asserted from a failing test alone. Gate: **blocked**.

## Affected versions and component context

`easyeda` 0.0.364, R5 local source based on 140046d000238f3d6c8611989682efb2872f25a9, final isolated peers/versions in [manifest](../working-dependency-manifest.json). SVG 0.0.433 is newer than the importer's original test-driver range 0.0.408. Earlier R4/R5 local changes are retained. Qualification target: GCT USB4215-03-A/C37616412; its focused regression is passing, not among the failed cases. Other components here are existing library test inputs, not additional fitted board parts or approved substitutions.

## Reproduction, input files and exact command

From `toolchain/easyeda-converter`, run `bun test` with the locked local peer graph and public component/3D-model access. Inputs, tests and existing golden snapshots are in [fixed source archive](../source-bases/easyeda-converter-fixed.tar.gz), with the unchanged control in [base archive](../source-bases/easyeda-converter-base.tar.gz). The isolated installed graph is described by [REPRODUCE.md](../REPRODUCE.md) and fixture/bun.lock. Run the same command in toolchain/easyeda-baseline for the paired source control.

## Expected and actual

The complete suite should pass before claiming a generally validated importer release. Final corrected run:278 pass / 33 fail,311 tests,57 snapshots passed/3 failed. Paired unchanged-source control:237 pass / 72 fail,309 tests. All 33 failing names also fail the control; no new failing name in that pair. Earlier public-download/control results differ, so name parity does not prove identical root causes or waive assertions.

[Exact full log](../logs/importer-final-qualified-suite.log), [control log](../logs/baseline-final-qualified-suite.log), [comparison](../logs/suite-comparison-final-qualified.json) and [machine-readable cases/errors](../logs/unresolved-suite-failures.json). Snapshot differences, source expectations and renderer/resource errors remain preserved; no blanket snapshot update or tolerance change was performed.

## Root-cause facts and hypotheses

Confirmed: the failures are reproducible in retained runs and all final failing names appear in the control. The new USB4215 raw/CAM regression, 48 existing source-field/contour fixtures, seven declaration builds and locked fixture checks pass. Reviewed inline changes add only raw-source paste/mask fields/regions. The broader failure set was not fully triaged in this focused run. Hypotheses include inherited local-source/older expectation mismatches, SVG/3D driver drift and public-resource variation. These must be verified case by case; they are not reported as confirmed defects or automatically accepted warnings.

## Impact and remaining work

Blocks declaring the entire toolchain/upstream patch release fully regression-qualified. It does not invalidate the recorded independent USB4215 source-fidelity measurements, and it does not supply missing manufacturer/assembler approval. No patch to these residual tests or their source is offered. A maintainer must compare each failure against current documented behavior and authoritative fixture input before changing expectations or code. Broad frozen-board regression was not rerun. R5 remains NOT FOR FABRICATION; no R6.

## Retained failing cases and visual evidence

|Case | Test/input location | Error category from log | Available visual diffs |
|---|---|---|---|
|imports C5378731 supplier fabrication notes into its footprint string |[tests/convert-to-ts/C5378731-to-ts.test.ts](../toolchain/easyeda-converter/tests/convert-to-ts/C5378731-to-ts.test.ts) |error:  |[C5378731-to-ts.diff.png](../toolchain/easyeda-converter/tests/convert-to-ts/__snapshots__/C5378731-to-ts.diff.png) |
|preserves package RECT layer and line-width fields with correct stroke units |[tests/convert-to-ts/package-rect-field-order-and-stroke-units.test.ts](../toolchain/easyeda-converter/tests/convert-to-ts/package-rect-field-order-and-stroke-units.test.ts) |error:  |Exact error retained in full log; no matching screenshot filename |
|renders the C2941005 schematic and PCB |[tests/convert-to-ts/C2941005-to-ts.test.ts](../toolchain/easyeda-converter/tests/convert-to-ts/C2941005-to-ts.test.ts) |error:  |Exact error retained in full log; no matching screenshot filename |
|should convert C136720 slide switch into a switch component with pin labels |[tests/convert-to-ts/C136720-to-ts.test.ts](../toolchain/easyeda-converter/tests/convert-to-ts/C136720-to-ts.test.ts) |error: expect(received).toMatchInlineSnapshot(expected) |[C136720-to-ts.diff.png](../toolchain/easyeda-converter/tests/convert-to-ts/__snapshots__/C136720-to-ts.diff.png) |
|converts C49234237 into a pushbutton component |[tests/convert-to-ts/C49234237-to-ts.test.ts](../toolchain/easyeda-converter/tests/convert-to-ts/C49234237-to-ts.test.ts) |error:  |[C49234237-to-ts-schematic.diff.png](../toolchain/easyeda-converter/tests/convert-to-ts/__snapshots__/C49234237-to-ts-schematic.diff.png) |
|should convert C9900017879 into typescript file |[tests/convert-to-ts/C9900017879-to-ts.test.ts](../toolchain/easyeda-converter/tests/convert-to-ts/C9900017879-to-ts.test.ts) |error:  |[C9900017879-to-ts-rotation.diff.png](../toolchain/easyeda-converter/tests/convert-to-ts/__snapshots__/C9900017879-to-ts-rotation.diff.png) |
|should convert C2828420 diode with metadata-derived pin labels |[tests/convert-to-ts/C2828420-to-ts.test.ts](../toolchain/easyeda-converter/tests/convert-to-ts/C2828420-to-ts.test.ts) |error:  |[C2828420-to-ts.diff.png](../toolchain/easyeda-converter/tests/convert-to-ts/__snapshots__/C2828420-to-ts.diff.png) |
|renders the C19943592 pin 1 rectangular footprint pad |[tests/convert-to-ts/C19943592-pin1-footprint-repro.test.ts](../toolchain/easyeda-converter/tests/convert-to-ts/C19943592-pin1-footprint-repro.test.ts) |error:  |[C19943592-pin1-footprint-repro.diff.png](../toolchain/easyeda-converter/tests/convert-to-ts/__snapshots__/C19943592-pin1-footprint-repro.diff.png) |
|should convert C2998002 into typescript file |[tests/convert-to-ts/C2998002-to-ts.test.ts](../toolchain/easyeda-converter/tests/convert-to-ts/C2998002-to-ts.test.ts) |error:  |[C2998002-to-ts-schematic.diff.png](../toolchain/easyeda-converter/tests/convert-to-ts/__snapshots__/C2998002-to-ts-schematic.diff.png) |
|should convert C51950748 into typescript file |[tests/convert-to-ts/C51950748-to-ts.test.ts](../toolchain/easyeda-converter/tests/convert-to-ts/C51950748-to-ts.test.ts) |error:  |[C51950748-to-ts-schematic.diff.png](../toolchain/easyeda-converter/tests/convert-to-ts/__snapshots__/C51950748-to-ts-schematic.diff.png) |
|preserves all C165948 pin aliases in generated TSX |[tests/convert-to-ts/c165948-multiple-pin-aliases.test.ts](../toolchain/easyeda-converter/tests/convert-to-ts/c165948-multiple-pin-aliases.test.ts) |error:  |[c165948-multiple-pin-aliases-pcb.diff.png](../toolchain/easyeda-converter/tests/convert-to-ts/__snapshots__/c165948-multiple-pin-aliases-pcb.diff.png) |
|renders the C488251 PCB view |[tests/convert-to-ts/C488251-pcb-view-repro.test.ts](../toolchain/easyeda-converter/tests/convert-to-ts/C488251-pcb-view-repro.test.ts) |error:  |Exact error retained in full log; no matching screenshot filename |
|C2055640 should preserve courtyard outlines when round-tripping through TSX |[tests/convert-to-ts/C2055640-to-ts.test.ts](../toolchain/easyeda-converter/tests/convert-to-ts/C2055640-to-ts.test.ts) |error:  |[C2055640-to-ts.diff.png](../toolchain/easyeda-converter/tests/convert-to-ts/__snapshots__/C2055640-to-ts.diff.png) |
|should convert C22446580 into typescript file |[tests/convert-to-ts/C22446580.test.ts](../toolchain/easyeda-converter/tests/convert-to-ts/C22446580.test.ts) |error: expect(received).toMatchInlineSnapshot(expected) |Exact error retained in full log; no matching screenshot filename |
|should convert C139797 tactile switch into a pushbutton component |[tests/convert-to-ts/C139797-to-ts.test.ts](../toolchain/easyeda-converter/tests/convert-to-ts/C139797-to-ts.test.ts) |error: expect(received).toMatchInlineSnapshot(expected) |Exact error retained in full log; no matching screenshot filename |
|repro: imports C8545 with its custom schematic symbol |[tests/convert-to-ts/C8545-to-ts.test.ts](../toolchain/easyeda-converter/tests/convert-to-ts/C8545-to-ts.test.ts) |error:  |Exact error retained in full log; no matching screenshot filename |
|preserves C490691 trailing-hash active-low pin names |[tests/convert-to-ts/C490691-active-low-labels.test.ts](../toolchain/easyeda-converter/tests/convert-to-ts/C490691-active-low-labels.test.ts) |error:  |[C490691-active-low-labels-preserved.diff.png](../toolchain/easyeda-converter/tests/convert-to-ts/__snapshots__/C490691-active-low-labels-preserved.diff.png) |
|preserves C472489 slash-separated pin 20 label |[tests/convert-to-ts/c472489-slash-separated-pin-label.test.ts](../toolchain/easyeda-converter/tests/convert-to-ts/c472489-slash-separated-pin-label.test.ts) |error:  |Exact error retained in full log; no matching screenshot filename |
|should normalize decorated C8598 diode polarity labels |[tests/convert-to-ts/C8598-to-ts.test.ts](../toolchain/easyeda-converter/tests/convert-to-ts/C8598-to-ts.test.ts) |error:  |[C8598-to-ts.diff.png](../toolchain/easyeda-converter/tests/convert-to-ts/__snapshots__/C8598-to-ts.diff.png) |
|should import C2943786 into a snapshotted typescript component |[tests/convert-to-ts/c2943786-to-ts.test.ts](../toolchain/easyeda-converter/tests/convert-to-ts/c2943786-to-ts.test.ts) |error:  |Exact error retained in full log; no matching screenshot filename |
|renders a payload with issue #464 variants |[tests/convert-to-ts/additional-payload-variants.test.ts](../toolchain/easyeda-converter/tests/convert-to-ts/additional-payload-variants.test.ts) |error:  |[additional-payload-variants-pcb.diff.png](../toolchain/easyeda-converter/tests/convert-to-ts/__snapshots__/additional-payload-variants-pcb.diff.png), [additional-payload-variants-schematic.diff.png](../toolchain/easyeda-converter/tests/convert-to-ts/__snapshots__/additional-payload-variants-schematic.diff.png) |
|renders the C55266 schematic and PCB |[tests/convert-to-ts/C55266-power-distribution-switch.test.ts](../toolchain/easyeda-converter/tests/convert-to-ts/C55266-power-distribution-switch.test.ts) |error:  |Exact error retained in full log; no matching screenshot filename |
|should convert C5248081 into typescript file |[tests/convert-to-ts/C5248081-to-ts.test.ts](../toolchain/easyeda-converter/tests/convert-to-ts/C5248081-to-ts.test.ts) |error:  |[C5248081-to-ts-simple-3d.diff.png](../toolchain/easyeda-converter/tests/convert-to-ts/__snapshots__/C5248081-to-ts-simple-3d.diff.png) |
|C2879827 preserves the board cutout in generated component TSX |[tests/convert-to-ts/C2879827-to-ts.test.ts](../toolchain/easyeda-converter/tests/convert-to-ts/C2879827-to-ts.test.ts) |error:  |[C2879827-to-ts.diff.png](../toolchain/easyeda-converter/tests/convert-to-ts/__snapshots__/C2879827-to-ts.diff.png) |
|should convert C2886621 into typescript file |[tests/convert-to-ts/C2886621-to-ts.test.ts](../toolchain/easyeda-converter/tests/convert-to-ts/C2886621-to-ts.test.ts) |error:  |[C2886621-to-ts-simple-3d.diff.png](../toolchain/easyeda-converter/tests/convert-to-ts/__snapshots__/C2886621-to-ts-simple-3d.diff.png) |
|should convert C113367 into typescript file |[tests/convert-to-ts/C113367-to-ts.test.ts](../toolchain/easyeda-converter/tests/convert-to-ts/C113367-to-ts.test.ts) |error:  |[C113367-to-ts-schematic.diff.png](../toolchain/easyeda-converter/tests/convert-to-ts/__snapshots__/C113367-to-ts-schematic.diff.png), [C113367-to-ts-simple-3d.diff.png](../toolchain/easyeda-converter/tests/convert-to-ts/__snapshots__/C113367-to-ts-simple-3d.diff.png) |
|should convert C60708 into typescript file |[tests/convert-to-ts/C60708-to-ts.test.ts](../toolchain/easyeda-converter/tests/convert-to-ts/C60708-to-ts.test.ts) |error:  |[C60708-to-ts-simple-3d.diff.png](../toolchain/easyeda-converter/tests/convert-to-ts/__snapshots__/C60708-to-ts-simple-3d.diff.png) |
|should convert C472489 into typescript file |[tests/convert-to-ts/C472489-to-ts.test.ts](../toolchain/easyeda-converter/tests/convert-to-ts/C472489-to-ts.test.ts) |error:  |[C472489-to-ts-simple-3d.diff.png](../toolchain/easyeda-converter/tests/convert-to-ts/__snapshots__/C472489-to-ts-simple-3d.diff.png) |
|should convert C2652953 into typescript file |[tests/convert-to-ts/C2652953-to-ts.test.ts](../toolchain/easyeda-converter/tests/convert-to-ts/C2652953-to-ts.test.ts) |error:  |[C2652953-to-ts-simple-3d.diff.png](../toolchain/easyeda-converter/tests/convert-to-ts/__snapshots__/C2652953-to-ts-simple-3d.diff.png) |
|reproduces C1046 L0805 inductor being generated as a generic chip |[tests/convert-to-ts/l0805-inductors-detected-as-chips.test.ts](../toolchain/easyeda-converter/tests/convert-to-ts/l0805-inductors-detected-as-chips.test.ts) |error:  |Exact error retained in full log; no matching screenshot filename |
|reproduces C281113 L0805 inductor being generated as a generic chip |[tests/convert-to-ts/l0805-inductors-detected-as-chips.test.ts](../toolchain/easyeda-converter/tests/convert-to-ts/l0805-inductors-detected-as-chips.test.ts) |error:  |Exact error retained in full log; no matching screenshot filename |
|preserves rotated silkscreen text in the PCB snapshot |[tests/convert-to-soup-tests/silkscreen-text-rotation.test.ts](../toolchain/easyeda-converter/tests/convert-to-soup-tests/silkscreen-text-rotation.test.ts) |error:  |[silkscreen-text-rotation.diff.png](../toolchain/easyeda-converter/tests/convert-to-soup-tests/__snapshots__/silkscreen-text-rotation.diff.png) |
|C41430893 should generate Circuit Json without errors |[tests/fetch-tests/c41430893.test.ts](../toolchain/easyeda-converter/tests/fetch-tests/c41430893.test.ts) |error:  |[c41430893-simple-3d.diff.png](../toolchain/easyeda-converter/tests/fetch-tests/__snapshots__/c41430893-simple-3d.diff.png) |
|imports C5378731 supplier fabrication notes into its footprint string |[tests/parse-tests/pin-label-hash.test.ts](../toolchain/easyeda-converter/tests/parse-tests/pin-label-hash.test.ts) | |Exact error retained in full log; no matching screenshot filename |
|preserves package RECT layer and line-width fields with correct stroke units |[tests/parse-tests/pin-label-hash.test.ts](../toolchain/easyeda-converter/tests/parse-tests/pin-label-hash.test.ts) | |Exact error retained in full log; no matching screenshot filename |
|renders the C2941005 schematic and PCB |[tests/parse-tests/pin-label-hash.test.ts](../toolchain/easyeda-converter/tests/parse-tests/pin-label-hash.test.ts) | |Exact error retained in full log; no matching screenshot filename |
|should convert C136720 slide switch into a switch component with pin labels |[tests/parse-tests/pin-label-hash.test.ts](../toolchain/easyeda-converter/tests/parse-tests/pin-label-hash.test.ts) | |Exact error retained in full log; no matching screenshot filename |
|converts C49234237 into a pushbutton component |[tests/parse-tests/pin-label-hash.test.ts](../toolchain/easyeda-converter/tests/parse-tests/pin-label-hash.test.ts) | |Exact error retained in full log; no matching screenshot filename |
|should convert C9900017879 into typescript file |[tests/parse-tests/pin-label-hash.test.ts](../toolchain/easyeda-converter/tests/parse-tests/pin-label-hash.test.ts) | |Exact error retained in full log; no matching screenshot filename |
|should convert C2828420 diode with metadata-derived pin labels |[tests/parse-tests/pin-label-hash.test.ts](../toolchain/easyeda-converter/tests/parse-tests/pin-label-hash.test.ts) | |Exact error retained in full log; no matching screenshot filename |
|renders the C19943592 pin 1 rectangular footprint pad |[tests/parse-tests/pin-label-hash.test.ts](../toolchain/easyeda-converter/tests/parse-tests/pin-label-hash.test.ts) | |Exact error retained in full log; no matching screenshot filename |
|should convert C2998002 into typescript file |[tests/parse-tests/pin-label-hash.test.ts](../toolchain/easyeda-converter/tests/parse-tests/pin-label-hash.test.ts) | |Exact error retained in full log; no matching screenshot filename |
|should convert C51950748 into typescript file |[tests/parse-tests/pin-label-hash.test.ts](../toolchain/easyeda-converter/tests/parse-tests/pin-label-hash.test.ts) | |Exact error retained in full log; no matching screenshot filename |
|preserves all C165948 pin aliases in generated TSX |[tests/parse-tests/pin-label-hash.test.ts](../toolchain/easyeda-converter/tests/parse-tests/pin-label-hash.test.ts) | |Exact error retained in full log; no matching screenshot filename |
|renders the C488251 PCB view |[tests/parse-tests/pin-label-hash.test.ts](../toolchain/easyeda-converter/tests/parse-tests/pin-label-hash.test.ts) | |Exact error retained in full log; no matching screenshot filename |
|C2055640 should preserve courtyard outlines when round-tripping through TSX |[tests/parse-tests/pin-label-hash.test.ts](../toolchain/easyeda-converter/tests/parse-tests/pin-label-hash.test.ts) | |Exact error retained in full log; no matching screenshot filename |
|should convert C22446580 into typescript file |[tests/parse-tests/pin-label-hash.test.ts](../toolchain/easyeda-converter/tests/parse-tests/pin-label-hash.test.ts) | |Exact error retained in full log; no matching screenshot filename |
|should convert C139797 tactile switch into a pushbutton component |[tests/parse-tests/pin-label-hash.test.ts](../toolchain/easyeda-converter/tests/parse-tests/pin-label-hash.test.ts) | |Exact error retained in full log; no matching screenshot filename |
|repro: imports C8545 with its custom schematic symbol |[tests/parse-tests/pin-label-hash.test.ts](../toolchain/easyeda-converter/tests/parse-tests/pin-label-hash.test.ts) | |Exact error retained in full log; no matching screenshot filename |
|preserves C490691 trailing-hash active-low pin names |[tests/parse-tests/pin-label-hash.test.ts](../toolchain/easyeda-converter/tests/parse-tests/pin-label-hash.test.ts) | |Exact error retained in full log; no matching screenshot filename |
|preserves C472489 slash-separated pin 20 label |[tests/parse-tests/pin-label-hash.test.ts](../toolchain/easyeda-converter/tests/parse-tests/pin-label-hash.test.ts) | |Exact error retained in full log; no matching screenshot filename |
|should normalize decorated C8598 diode polarity labels |[tests/parse-tests/pin-label-hash.test.ts](../toolchain/easyeda-converter/tests/parse-tests/pin-label-hash.test.ts) | |Exact error retained in full log; no matching screenshot filename |
|should import C2943786 into a snapshotted typescript component |[tests/parse-tests/pin-label-hash.test.ts](../toolchain/easyeda-converter/tests/parse-tests/pin-label-hash.test.ts) | |Exact error retained in full log; no matching screenshot filename |
|renders a payload with issue #464 variants |[tests/parse-tests/pin-label-hash.test.ts](../toolchain/easyeda-converter/tests/parse-tests/pin-label-hash.test.ts) | |Exact error retained in full log; no matching screenshot filename |
|renders the C55266 schematic and PCB |[tests/parse-tests/pin-label-hash.test.ts](../toolchain/easyeda-converter/tests/parse-tests/pin-label-hash.test.ts) | |Exact error retained in full log; no matching screenshot filename |
|should convert C5248081 into typescript file |[tests/parse-tests/pin-label-hash.test.ts](../toolchain/easyeda-converter/tests/parse-tests/pin-label-hash.test.ts) | |Exact error retained in full log; no matching screenshot filename |
|C2879827 preserves the board cutout in generated component TSX |[tests/parse-tests/pin-label-hash.test.ts](../toolchain/easyeda-converter/tests/parse-tests/pin-label-hash.test.ts) | |Exact error retained in full log; no matching screenshot filename |
|should convert C2886621 into typescript file |[tests/parse-tests/pin-label-hash.test.ts](../toolchain/easyeda-converter/tests/parse-tests/pin-label-hash.test.ts) | |Exact error retained in full log; no matching screenshot filename |
|should convert C113367 into typescript file |[tests/parse-tests/pin-label-hash.test.ts](../toolchain/easyeda-converter/tests/parse-tests/pin-label-hash.test.ts) | |Exact error retained in full log; no matching screenshot filename |
|should convert C60708 into typescript file |[tests/parse-tests/pin-label-hash.test.ts](../toolchain/easyeda-converter/tests/parse-tests/pin-label-hash.test.ts) | |Exact error retained in full log; no matching screenshot filename |
|should convert C472489 into typescript file |[tests/parse-tests/pin-label-hash.test.ts](../toolchain/easyeda-converter/tests/parse-tests/pin-label-hash.test.ts) | |Exact error retained in full log; no matching screenshot filename |
|should convert C2652953 into typescript file |[tests/parse-tests/pin-label-hash.test.ts](../toolchain/easyeda-converter/tests/parse-tests/pin-label-hash.test.ts) | |Exact error retained in full log; no matching screenshot filename |
|reproduces C1046 L0805 inductor being generated as a generic chip |[tests/parse-tests/pin-label-hash.test.ts](../toolchain/easyeda-converter/tests/parse-tests/pin-label-hash.test.ts) | |Exact error retained in full log; no matching screenshot filename |
|reproduces C281113 L0805 inductor being generated as a generic chip |[tests/parse-tests/pin-label-hash.test.ts](../toolchain/easyeda-converter/tests/parse-tests/pin-label-hash.test.ts) | |Exact error retained in full log; no matching screenshot filename |
|preserves rotated silkscreen text in the PCB snapshot |[tests/parse-tests/pin-label-hash.test.ts](../toolchain/easyeda-converter/tests/parse-tests/pin-label-hash.test.ts) | |Exact error retained in full log; no matching screenshot filename |
|C41430893 should generate Circuit Json without errors |[tests/parse-tests/pin-label-hash.test.ts](../toolchain/easyeda-converter/tests/parse-tests/pin-label-hash.test.ts) | |Exact error retained in full log; no matching screenshot filename |
