AnasSarkiz/magnetic-shutter-remote/tscircuit-issues/evidence/075/land-comparison.pdf

## ESP32-C3-WROOM-02-N4 / C2934560

### QUALIFICATION BLOCKED — SUPPLIER VARIATION NOT APPROVED

Espressif v1.7, Figure 11-1 p38; preserved EasyEDA package ab901810668e4ba2b431728512d738d6

Outer contact, same-centre dimension overlay

Supplier: 1.999996 x 0.999998 mm Espressif recommendation: 1.5 x 0.9 mm

All 18 outer contacts have the same discrepancy.

Nine EP ground tiles agree: 0.7 x 0.7 mm.

27/27 raw-source/import copper features retained.

Conversion discrepancy: 5.085e-14 mm maximum.

19/19 logical pin identities checked against datasheet.

No imported definition or generated JSON was edited.

This is NOT a fabrication drawing or a proposed substitute footprint.

The manufacturer specifies recommended lands, not a tolerance envelope. No failure tolerance is invented.

Faithful supplier import does not establish manufacturer approval of the larger copper/paste pattern.

Raw input, all pad coordinates, native renders and original import are preserved alongside the report.

Source attribution: JLCEDA/EasyEDA Official Library — https://lceda.cn/ — https://easyeda.com/

Engineering review date: 2026-10-05. R6/R7 unchanged; R8 is not ready for fabrication.
