AnasSarkiz/magnetic-shutter-remote/tscircuit-issues/evidence/015-usb-land-pattern-conflicts-with-npth-process/j1-clearance-annotated.png

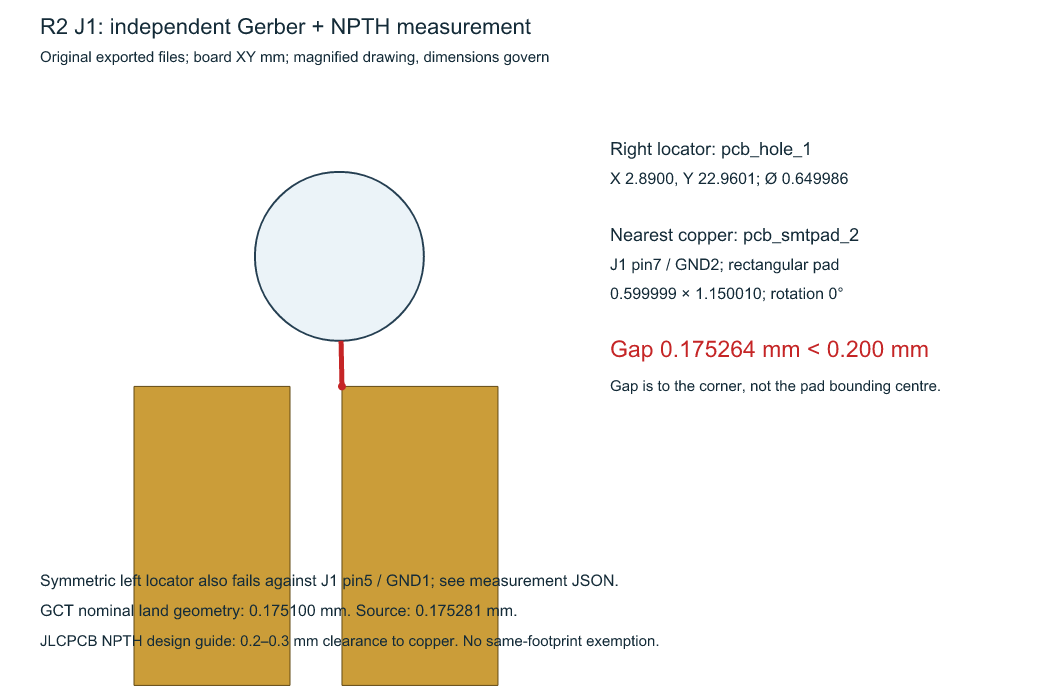
tscircuit-issues/evidence/015-usb-land-pattern-conflicts-with-npth-process/j1-clearance-annotated.png
