AnasSarkiz/magnetic-shutter-remote/tscircuit-issues/evidence/024-excellon-g85-slot-record-and-mode-export/R2-g85-reader-before.png

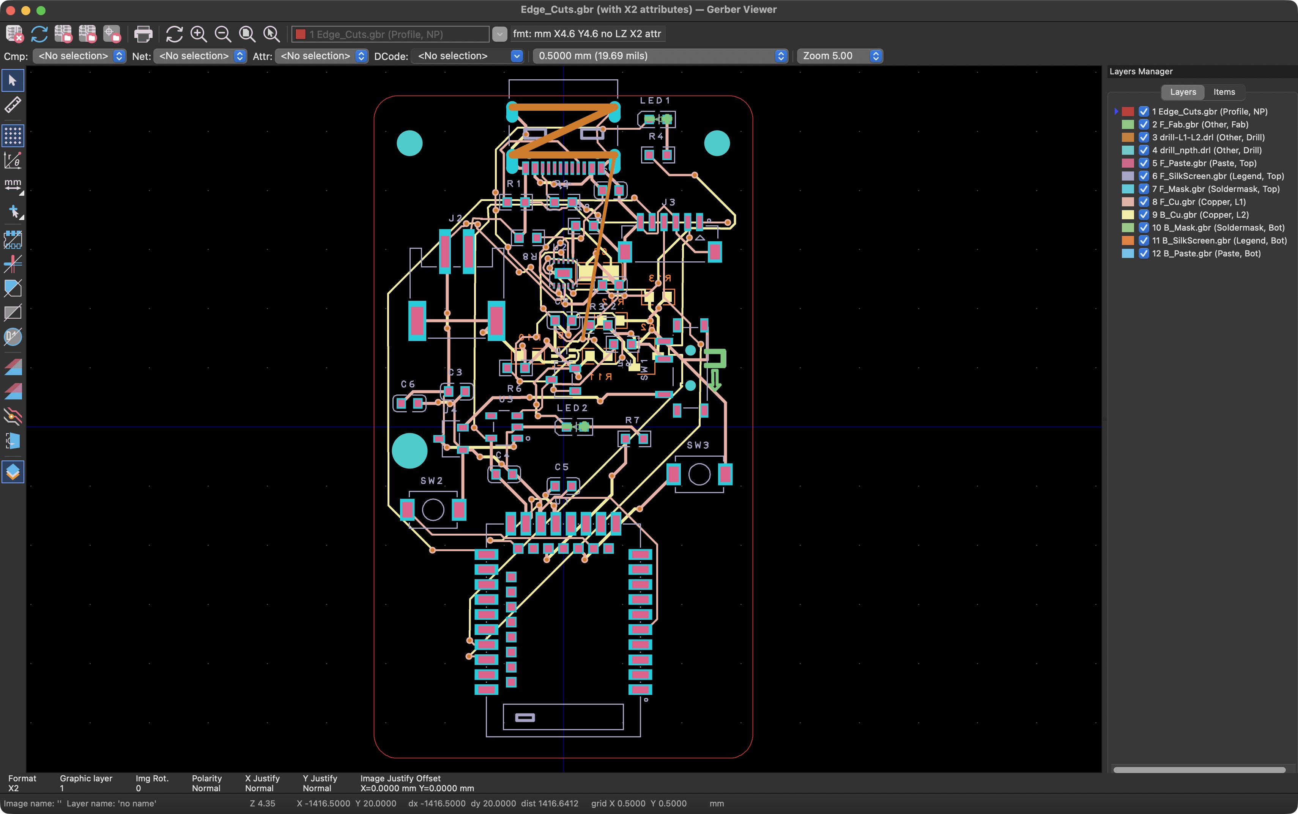
tscircuit-issues/evidence/024-excellon-g85-slot-record-and-mode-export/R2-g85-reader-before.png
