AnasSarkiz/magnetic-shutter-remote/tscircuit-issues/evidence/071-smtpad-bounds/mixed-pad-bounds-convention.png

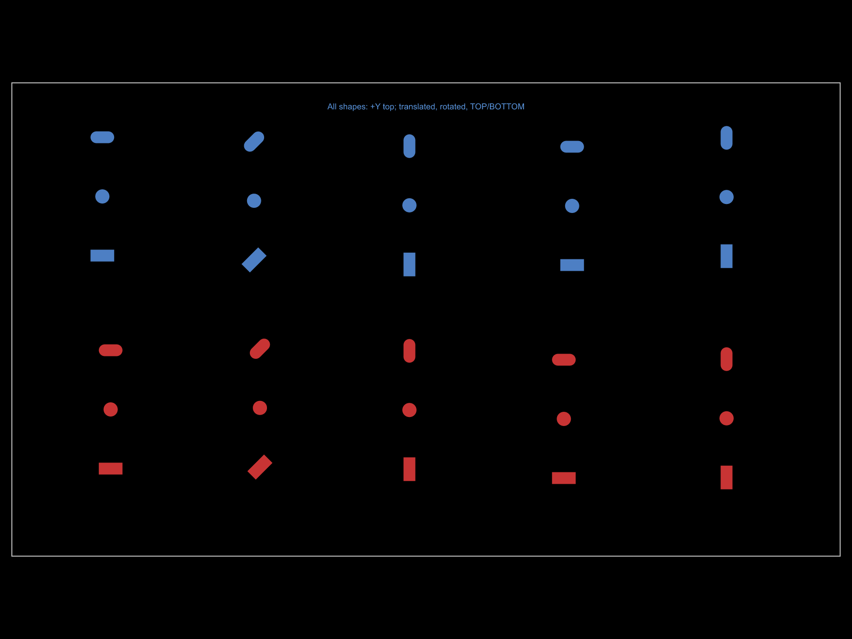
tscircuit-issues/evidence/071-smtpad-bounds/mixed-pad-bounds-convention.png
