AnasSarkiz/magnetic-shutter-remote/tscircuit-issues/evidence/071-smtpad-bounds/pt4115-overlapping-ground-pads.png

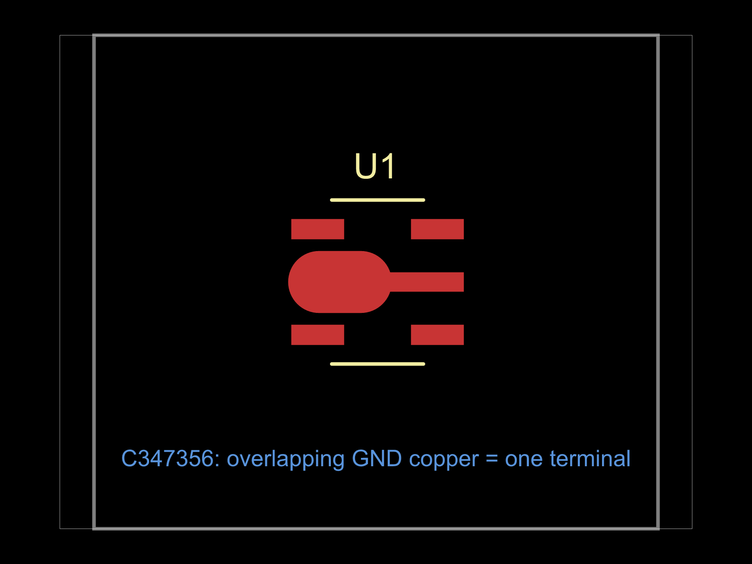
tscircuit-issues/evidence/071-smtpad-bounds/pt4115-overlapping-ground-pads.png
