AnasSarkiz/magnetic-shutter-remote/tscircuit-issues/evidence/071-smtpad-bounds/separated-mixed-ground-pads.png

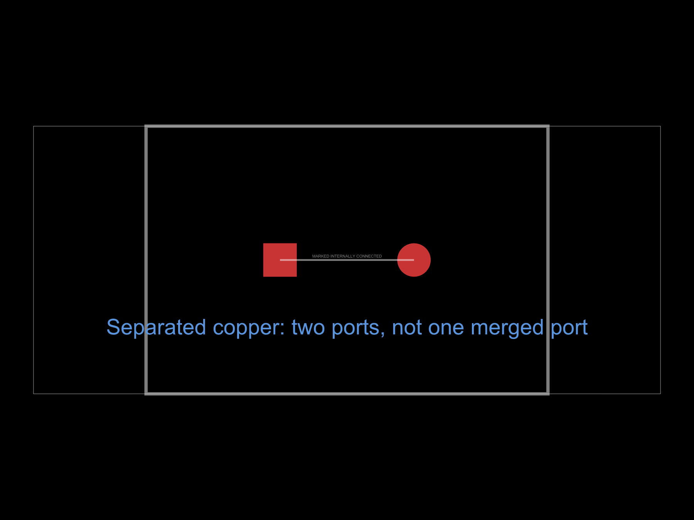
tscircuit-issues/evidence/071-smtpad-bounds/separated-mixed-ground-pads.png
