AnasSarkiz/magnetic-shutter-remote/tscircuit-issues/evidence/075/imported-3d.png

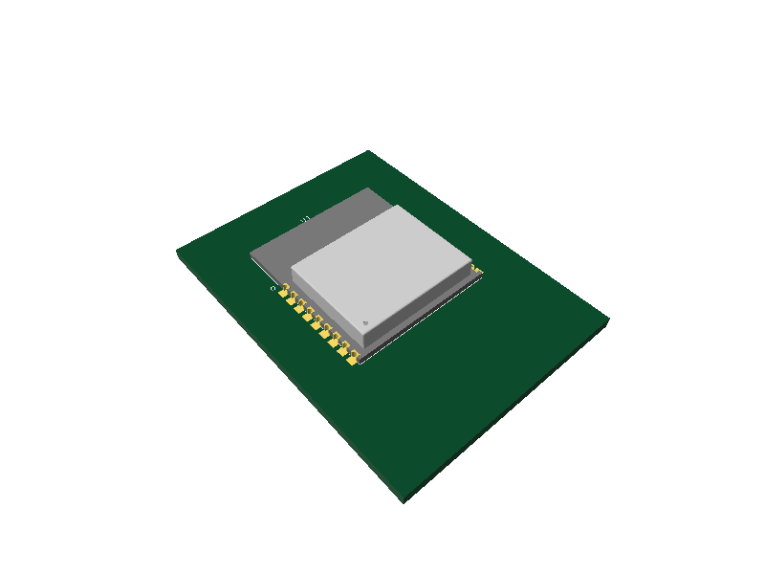
tscircuit-issues/evidence/075/imported-3d.png
