AnasSarkiz/magnetic-shutter-remote/tscircuit-issues/evidence/075/imported-pcb.png

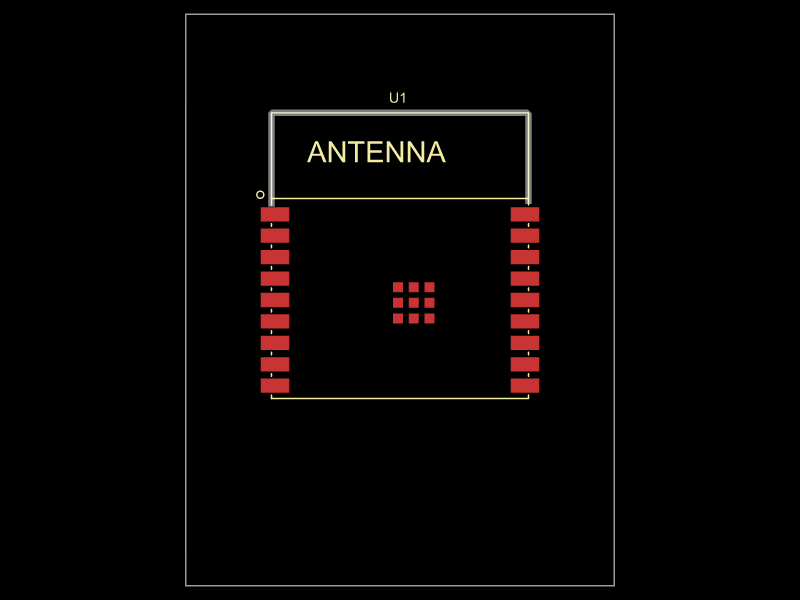
tscircuit-issues/evidence/075/imported-pcb.png
