AnasSarkiz/magnetic-shutter-remote/tscircuit-issues/evidence/075/land-comparison.png

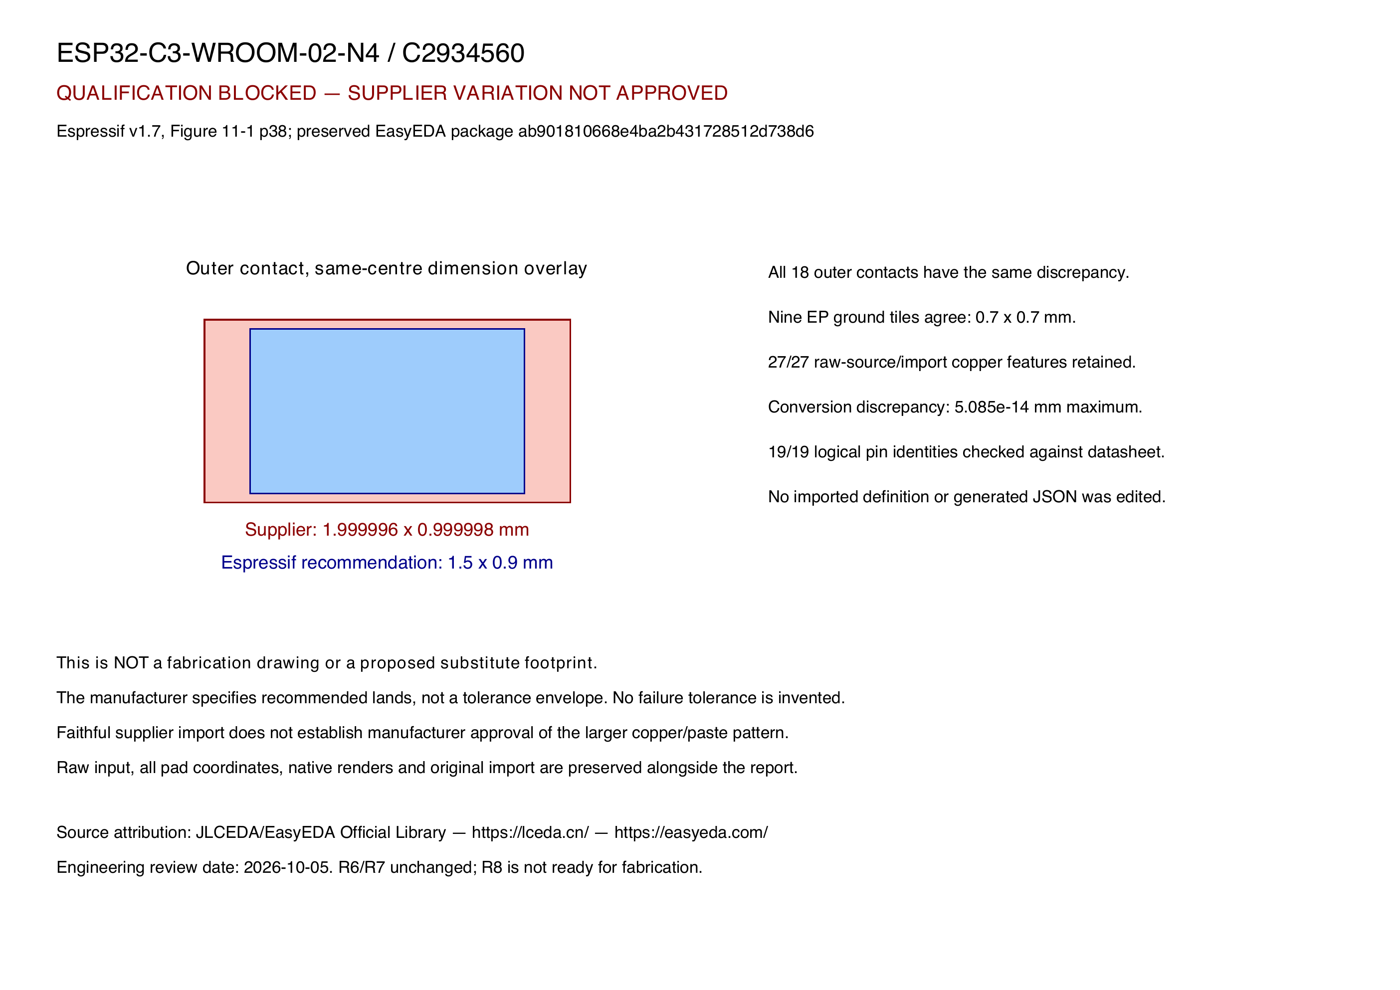
tscircuit-issues/evidence/075/land-comparison.png
